greenmagics/Ender5plus_greenmaker_mod/zdj/1.jpg

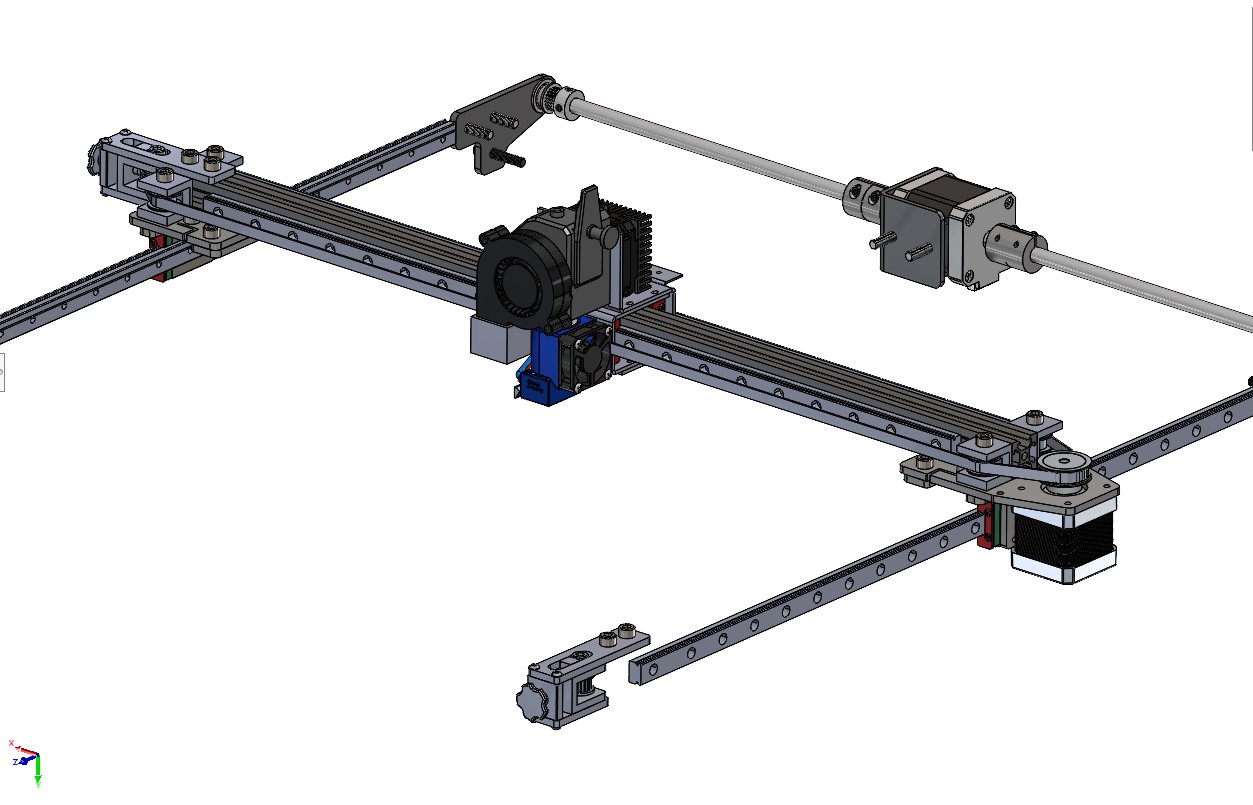
zdj/1.jpg
