greenmagics/Ender5plus_greenmaker_mod/zdj/2.jpg

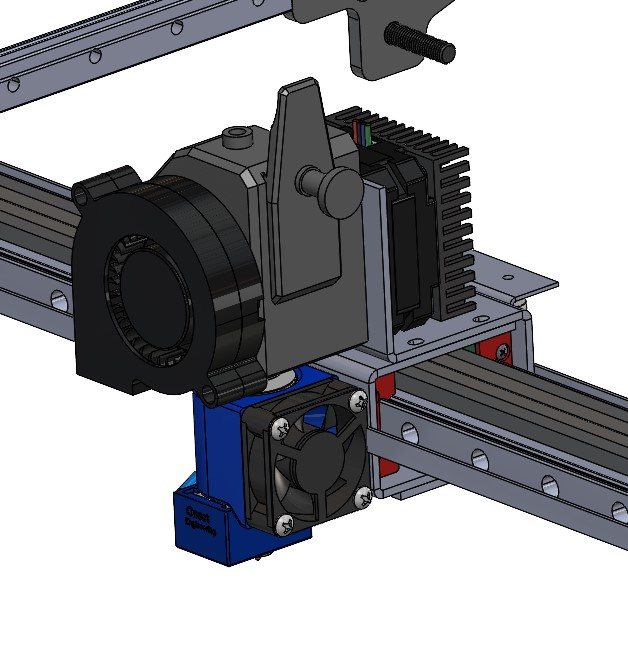
zdj/2.jpg
