greenmagics/Ender5plus_greenmaker_mod/zdj/3.jpg

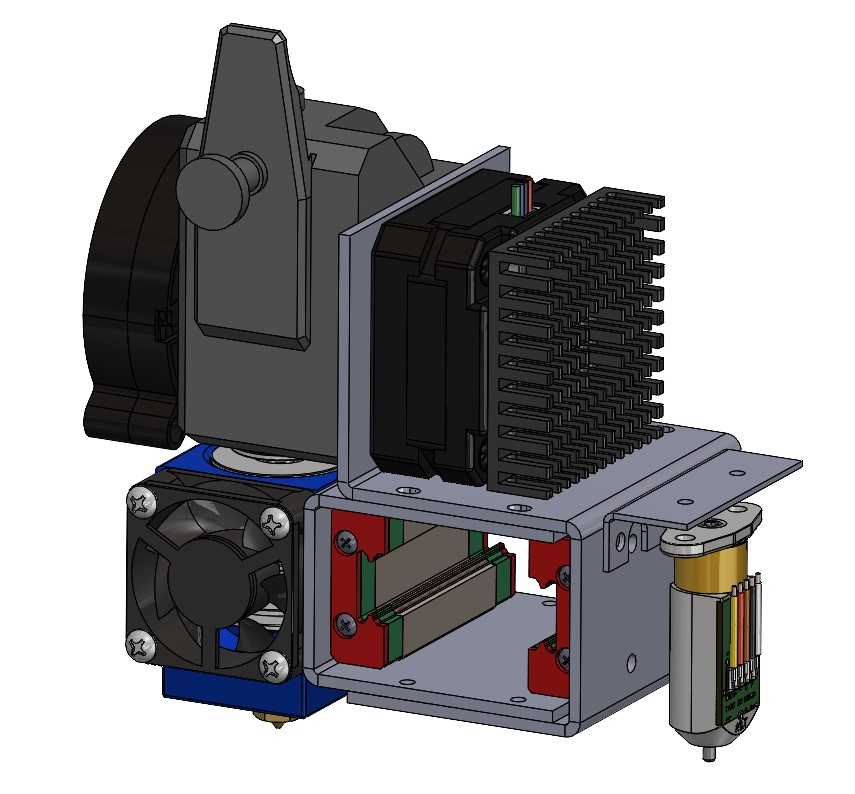
zdj/3.jpg
