greenmagics/Ender5plus_greenmaker_mod/zdj/4.jpg

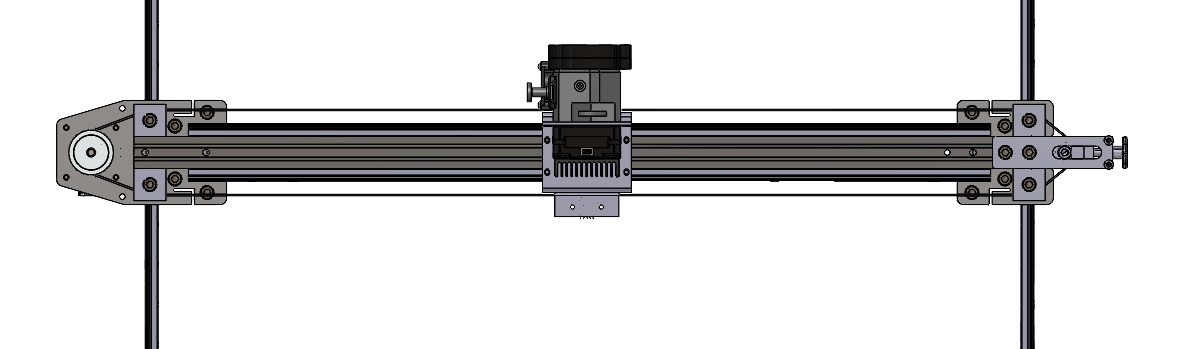
zdj/4.jpg
