greenmagics/Ender5plus_greenmaker_mod/zdj/5.jpg

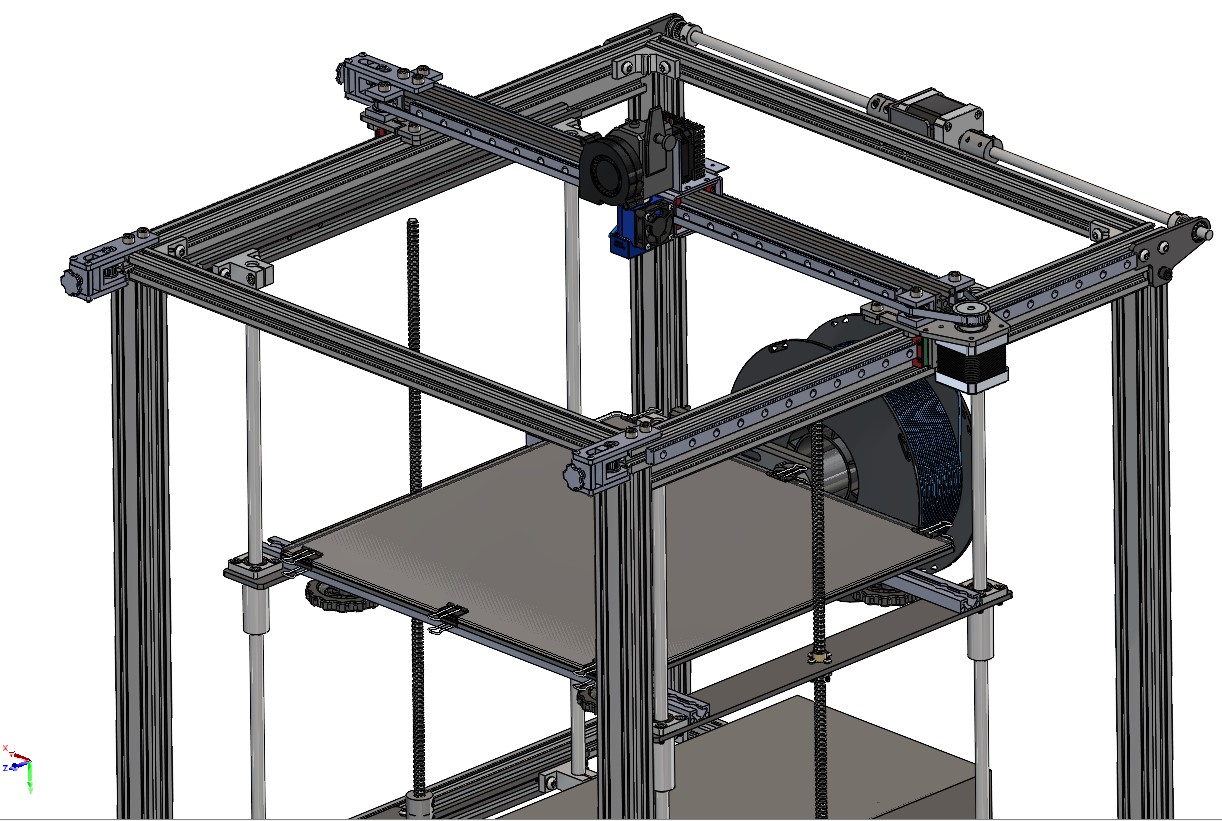
zdj/5.jpg
