greenmagics/Ender5plus_greenmaker_mod/parts/z-axis-drive-assem/z-axis-assem.SLDASM

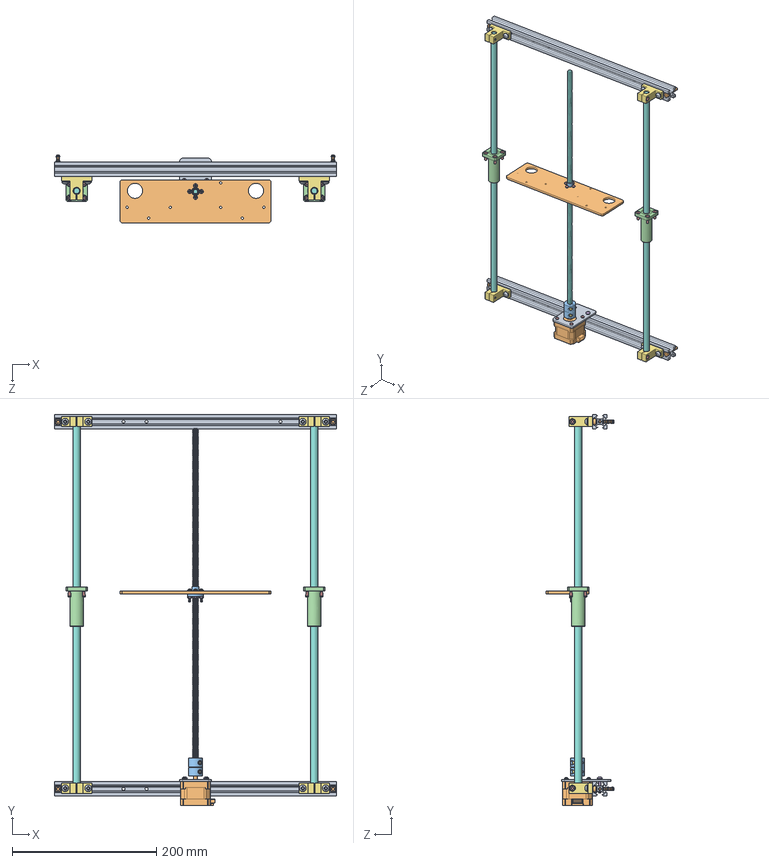
[picture p20: CAD file, 2021-08-18]
parts/z-axis-drive-assem/z-axis-assem.SLDASM
392.0 x 543.0 x 95.0 mm
z-axis-stepper-bracket
stepper-motor
shaft-coupling
lock-washer x 22
bhcs-M3 x 8
bhcs-M4 x 2
shcs-M3 x 2
lead-screw
z-axis-strut-20x20 x 2
z-axis-bearing-plate
lead-screw-nut
flanged-bearing-10mm x 2
shcs-M4 x 12
hex-nut-3mm x 4
guide-rod-bracket x 4
guide-rod x 2
bhcs-M5 x 8
shcs-M5 x 4
