greenmagics/Ender5plus_greenmaker_mod/heatbreak and part cooling fan/heatbreak fan mount assembly.SLDASM

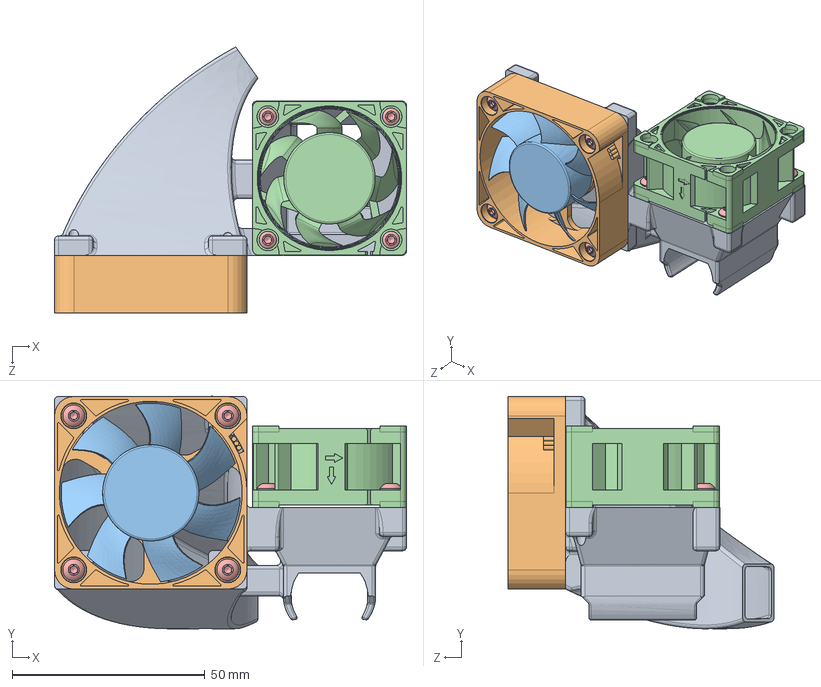
[picture p21: CAD file, 2021-08-12]
heatbreak and part cooling fan/heatbreak fan mount assembly.SLDASM
91.4 x 60.4 x 69.1 mm
heatbreak fan mount
Gelid Silent 5 frame
Gelid Silent 5 rotor
NF-A4X20 5V PWM.step
socket button head cap screw_am x 8
