greenmagics/Ender5plus_greenmaker_mod/parts/frame/frame assembly.SLDASM

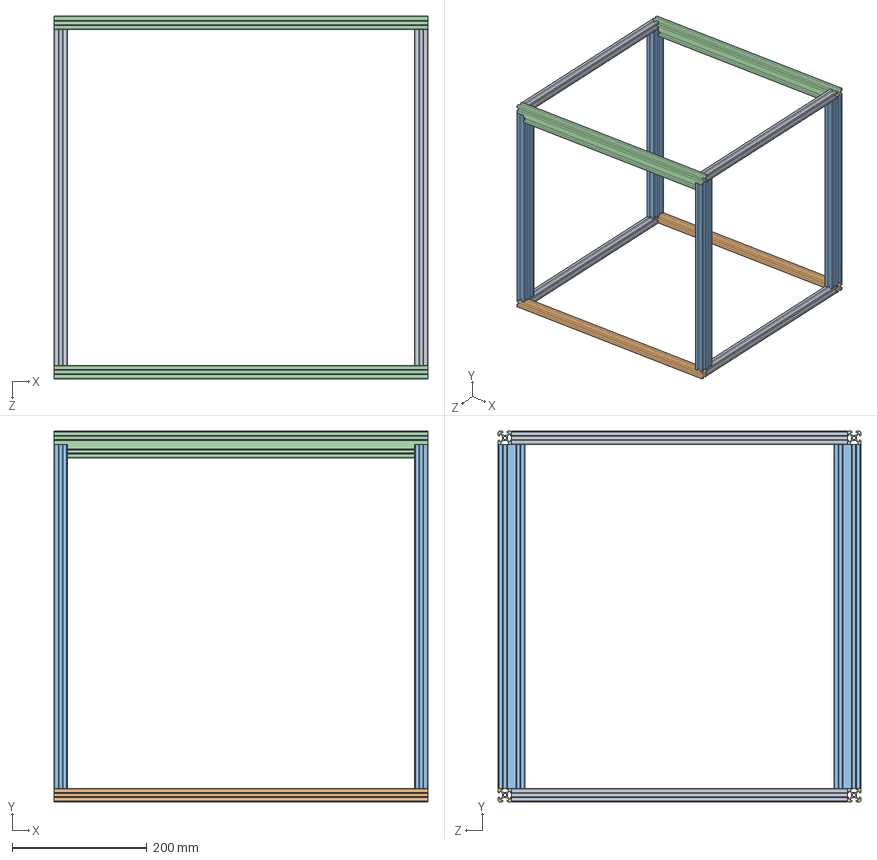
[picture p22: CAD file, 2021-08-12]
parts/frame/frame assembly.SLDASM
555.0 x 550.0 x 538.0 mm
base_498mm x 4
base_555mm x 2
vertical_510mm x 4
top_555 x 2
