greenmagics/Ender5plus_greenmaker_mod/parts/Y-AXIS-ASSEM/rear-pulley-assem.SLDASM

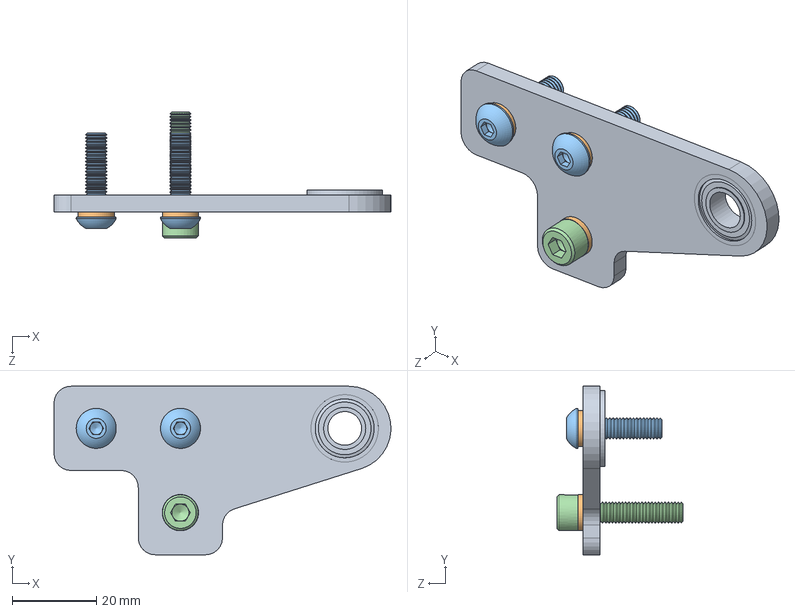
[picture p23: CAD file, 2021-08-12]
parts/Y-AXIS-ASSEM/rear-pulley-assem.SLDASM
80.0 x 40.0 x 30.0 mm
rear-pulley-bracket
lock-washer x 3
bhcs-M5 x 2
shcs-M5
