greenmagics/Ender5plus_greenmaker_mod/parts/z-axis-drive-assem/limit-switch-assem.sldasm

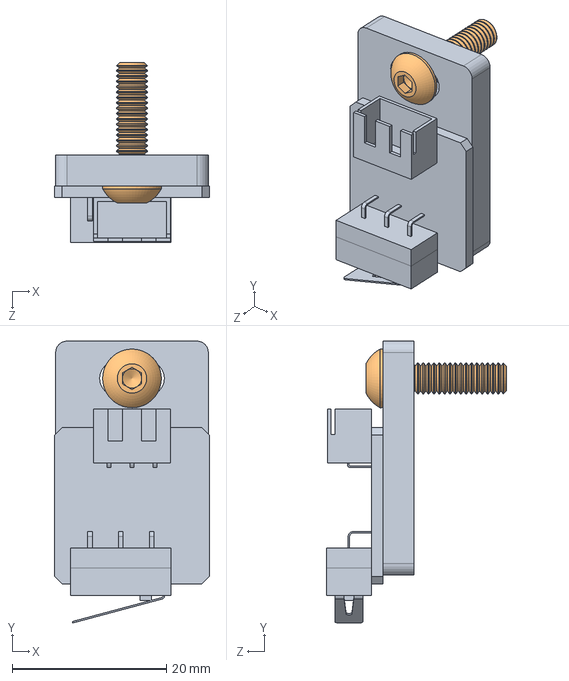
[picture p24: CAD file, 2021-08-12]
parts/z-axis-drive-assem/limit-switch-assem.sldasm
20.1 x 36.5 x 23.3 mm
limit-switch
bhcs-M4
