greenmagics/Ender5plus_greenmaker_mod/parts/hot-end/hot-end-assem.SLDASM

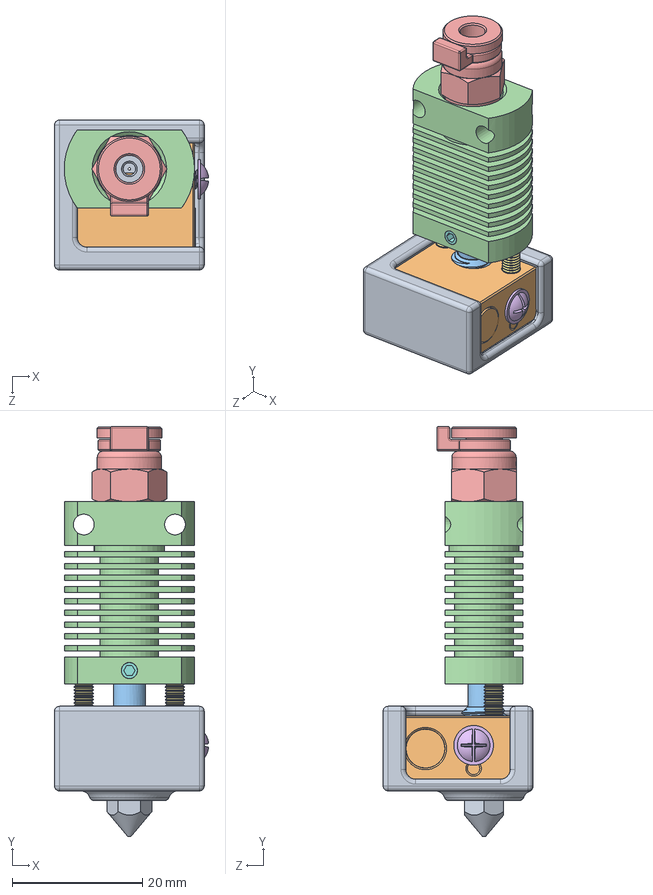
[picture p25: CAD file, 2021-08-12]
parts/hot-end/hot-end-assem.SLDASM
23.6 x 63.0 x 23.0 mm
nozzle-04
hot-end-heater-block
heat-break
heat-sink
hose-fitting-4x10mm
bh-screw-flanged-M3
fhsc-M3 x 2
set-screw-M3 x 2
hot-end-boot
