greenmagics/Ender5plus_greenmaker_mod/parts/x-axis-assem/x-axis-pulley-assem.SLDASM

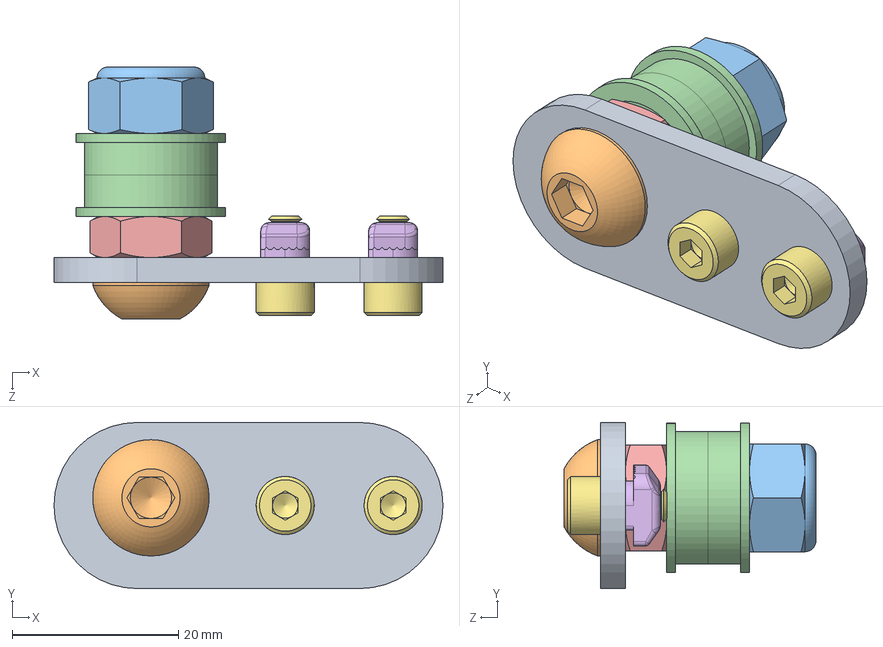
[picture p26: CAD file, 2021-08-12]
parts/x-axis-assem/x-axis-pulley-assem.SLDASM
46.8 x 20.0 x 30.4 mm
x-axis-pulley-mount
bhcs-M8
locknut-M8
pulley-half x 2
hex-nut-8mm
t-slot-nut x 2
shcs-M4 x 2
