greenmagics/Ender5plus_greenmaker_mod/czesci_dodane/GT2/GT2 Timing Pulley, Configurable.SLDASM

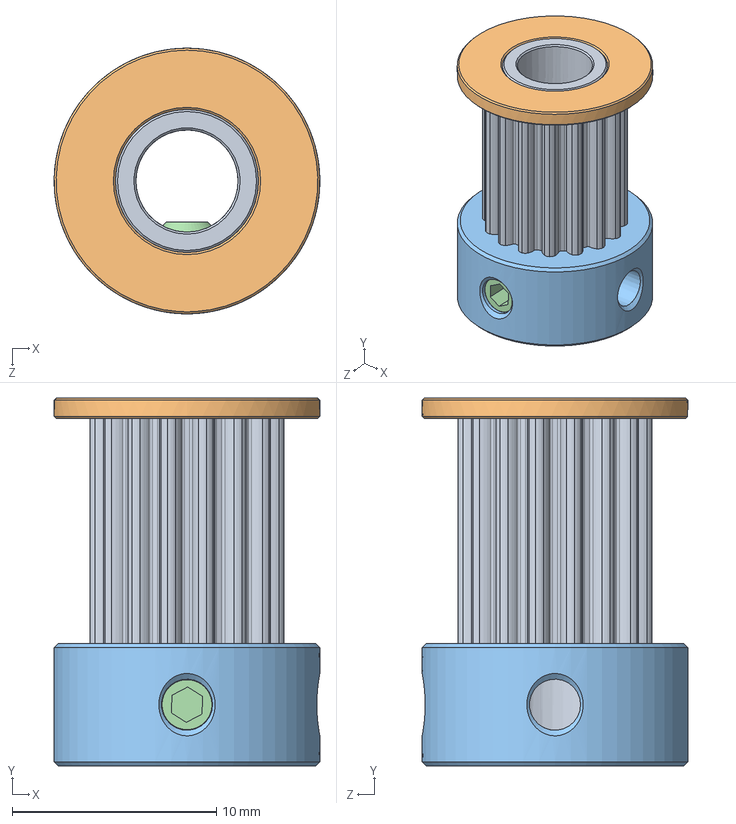
[picture p27: CAD file, 2021-08-12]
czesci_dodane/GT2/GT2 Timing Pulley, Configurable.SLDASM
13.0 x 18.0 x 13.0 mm
Body, GT2 Timing Pulley, Configurable
Top Flange, GT2 Timing Pulley, Configurable
Bottom Base, GT2 Timing Pulley, Configurable
socket set screw flat point_am
