greenmagics/Ender5plus_greenmaker_mod/parts/Y-AXIS-ASSEM/y-axis-drive-shaft-assem.sldasm

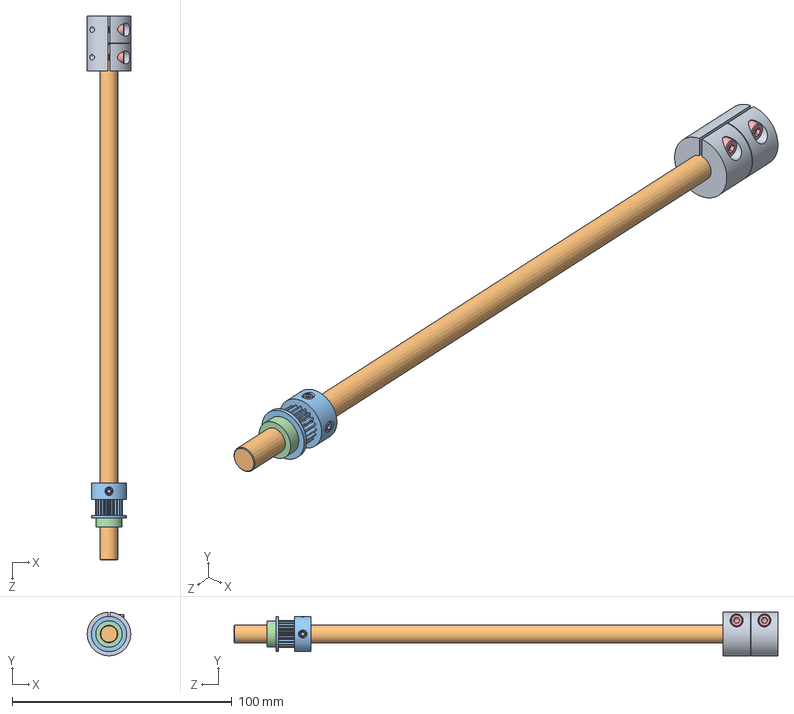
[picture p28: CAD file, 2021-08-12]
parts/Y-AXIS-ASSEM/y-axis-drive-shaft-assem.sldasm
19.8 x 19.8 x 247.6 mm
shaft-coupling
drive-shaft-8mm
toothed-pulley
delrin-spacer
shcs-M3 x 2
set-screw-M3 x 2
