greenmagics/Ender5plus_greenmaker_mod/czesci_dodane/GT2/Configurable GT2 Timing Pulleys Lined Up.SLDASM

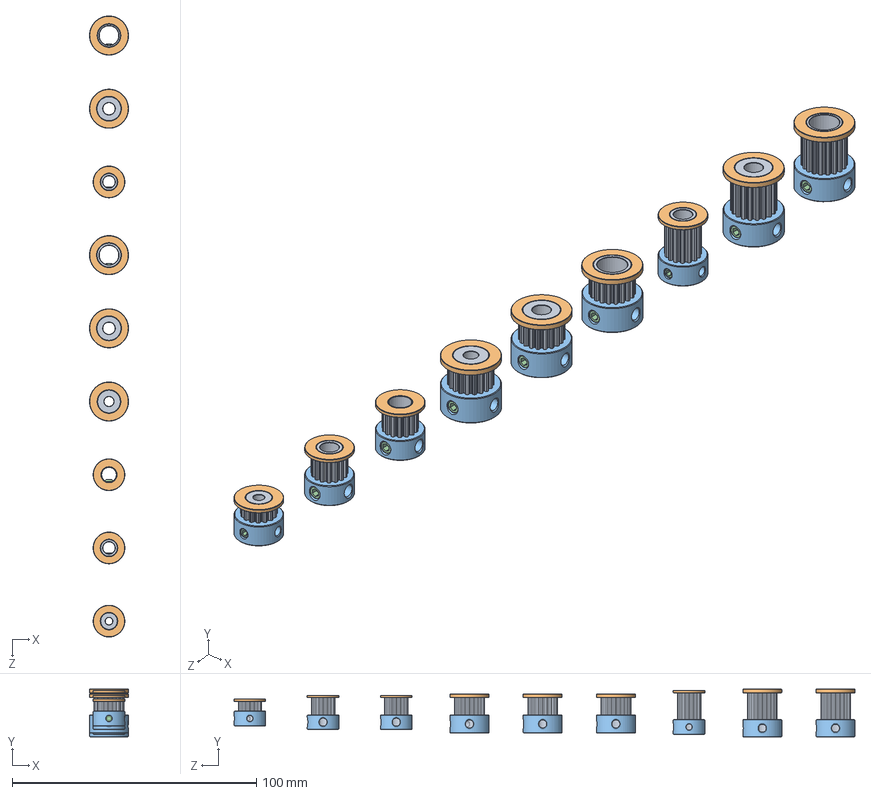
[picture p29: CAD file, 2021-08-12]
czesci_dodane/GT2/Configurable GT2 Timing Pulleys Lined Up.SLDASM
16.0 x 19.5 x 254.5 mm
Body, GT2 Timing Pulley, Configurable x 9
Top Flange, GT2 Timing Pulley, Configurable x 9
Bottom Base, GT2 Timing Pulley, Configurable x 9
socket set screw flat point_am x 9
