greenmagics/Ender5plus_greenmaker_mod/parts/x-axis-assem/x-axis-bogey-left.SLDASM

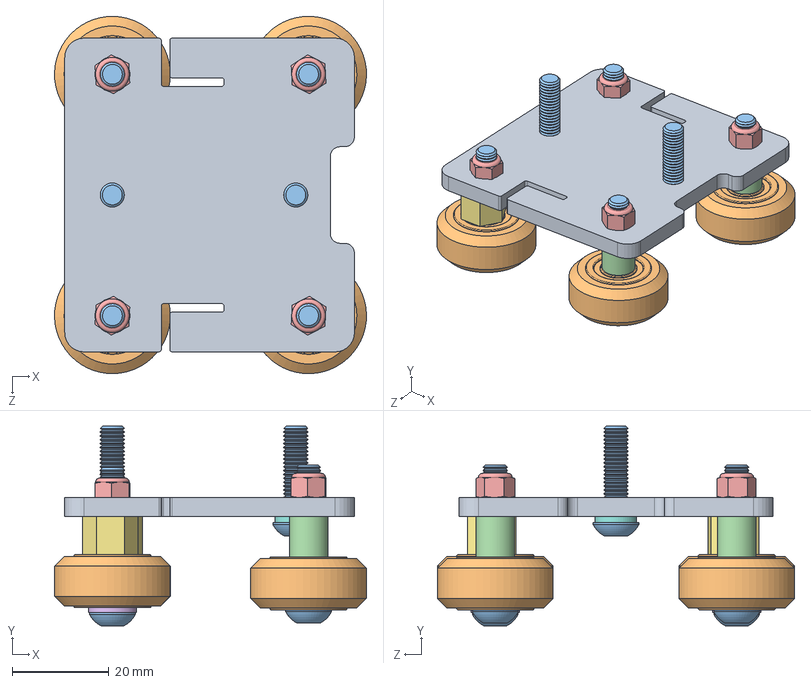
[picture p30: CAD file, 2021-08-12]
parts/x-axis-assem/x-axis-bogey-left.SLDASM
64.6 x 41.3 x 74.0 mm
x-axis-stepper-mount
wheel x 4
bhcs-M5 x 6
wheel-spacer x 2
locknut-M4 x 4
flat-washer x 2
eccentric-nut x 2
lock-washer x 2
