greenmagics/Ender5plus_greenmaker_mod/parts/Y-AXIS-ASSEM/y-axis-drive-assem.SLDASM

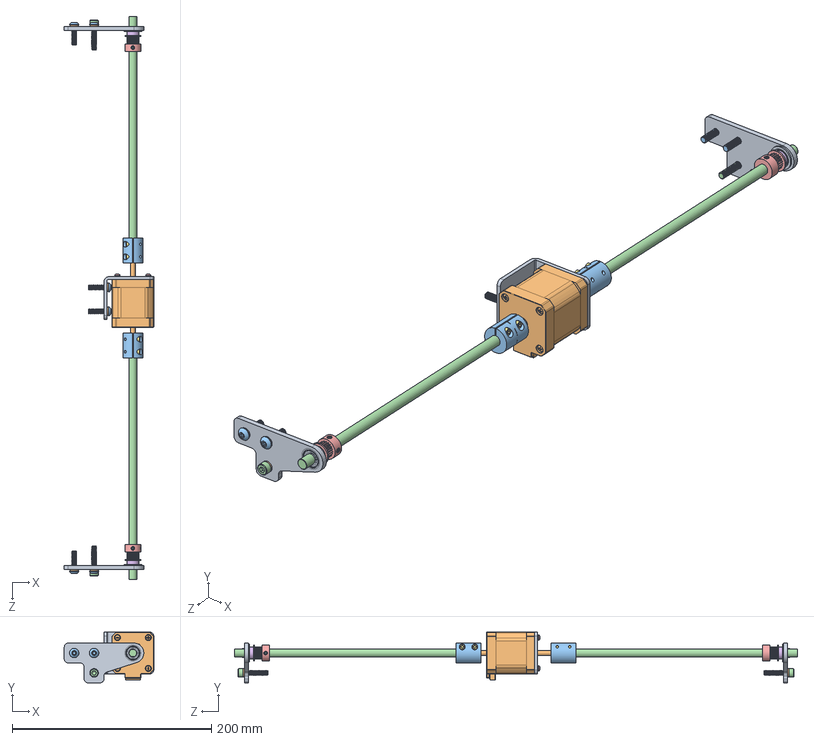
[picture p31: CAD file, 2021-08-12]
parts/Y-AXIS-ASSEM/y-axis-drive-assem.SLDASM
90.0 x 51.0 x 565.7 mm
y-axis-stepper-bracket
stepper-motor
shaft-coupling x 2
drive-shaft-8mm x 2
toothed-pulley x 2
delrin-spacer x 2
shcs-M3 x 4
set-screw-M3 x 4
rear-pulley-bracket x 2
lock-washer x 12
bhcs-M5 x 6
shcs-M5 x 2
bhcs-M3 x 4
