greenmagics/Ender5plus_greenmaker_mod/parts/x-axis-assem/x-axis-bogey-right.SLDASM

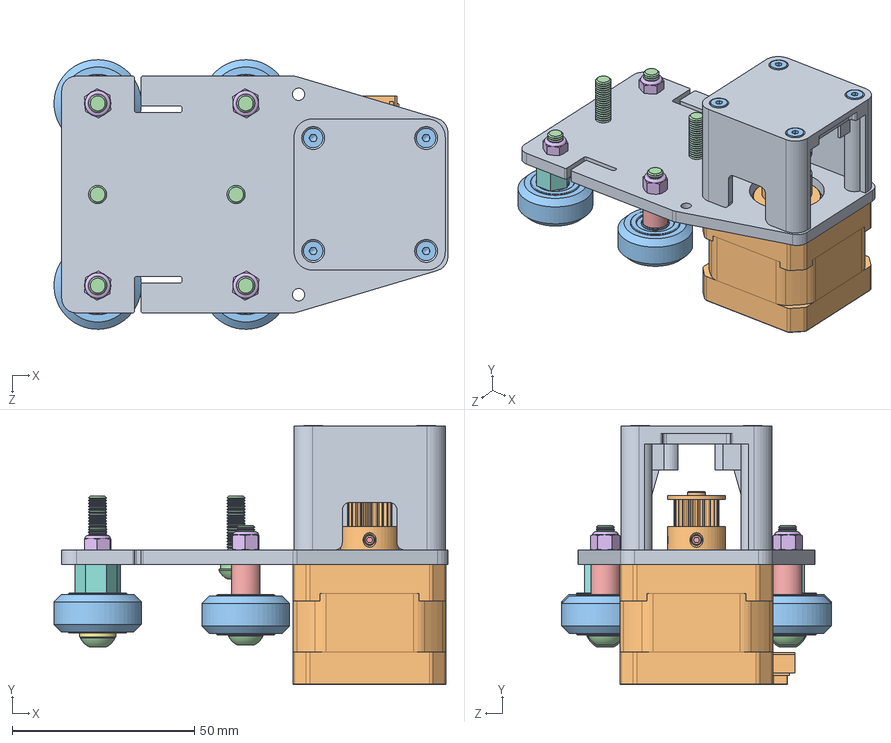
[picture p32: CAD file, 2021-08-12]
parts/x-axis-assem/x-axis-bogey-right.SLDASM
108.1 x 71.2 x 74.0 mm
x-axis-stepper-mount
toothed-pulley
wheel x 4
bhcs-M5 x 6
wheel-spacer x 2
locknut-M4 x 4
flat-washer x 2
eccentric-nut x 2
x-axis-stepper-cover
stepper-motor
fhsc-M3 x 4
lock-washer x 2
set-screw-M3 x 2
