greenmagics/Ender5plus_greenmaker_mod/parts/z-axis-drive-assem/guide-rod-assem.SLDASM

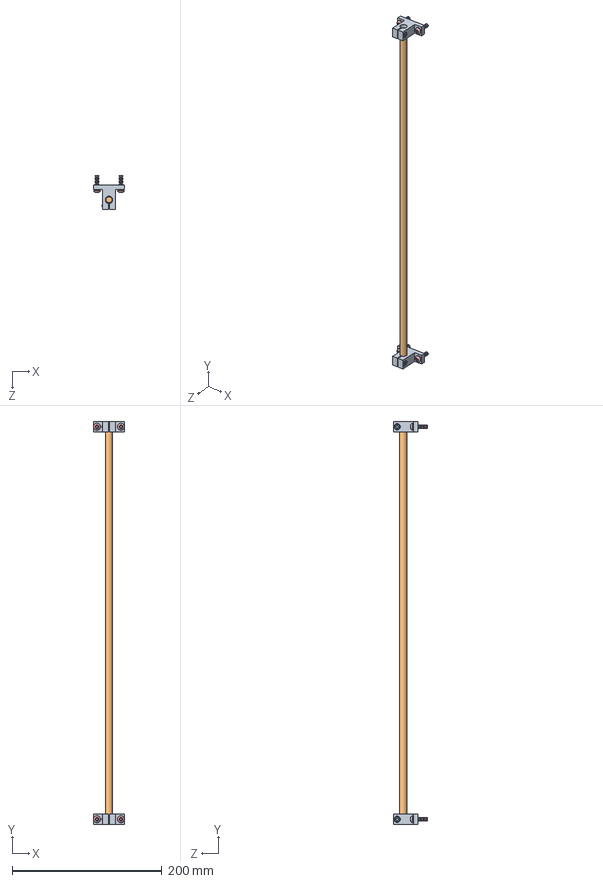
[picture p33: CAD file, 2021-08-12]
parts/z-axis-drive-assem/guide-rod-assem.SLDASM
42.0 x 538.0 x 45.5 mm
guide-rod-bracket x 2
guide-rod
shcs-M4 x 2
lock-washer x 4
bhcs-M5 x 4
