greenmagics/Ender5plus_greenmaker_mod/parts/extruder/bltouch assembly.SLDASM

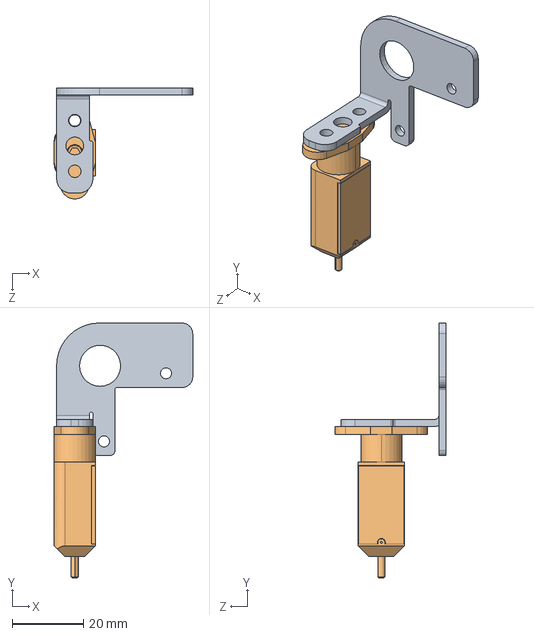
[picture p34: CAD file, 2021-08-12]
parts/extruder/bltouch assembly.SLDASM
38.9 x 71.5 x 31.1 mm
bltouch bracket
BLTouch.step
