greenmagics/Ender5plus_greenmaker_mod/parts/z-axis-drive-assem/z-axis-stepper-assem.sldasm

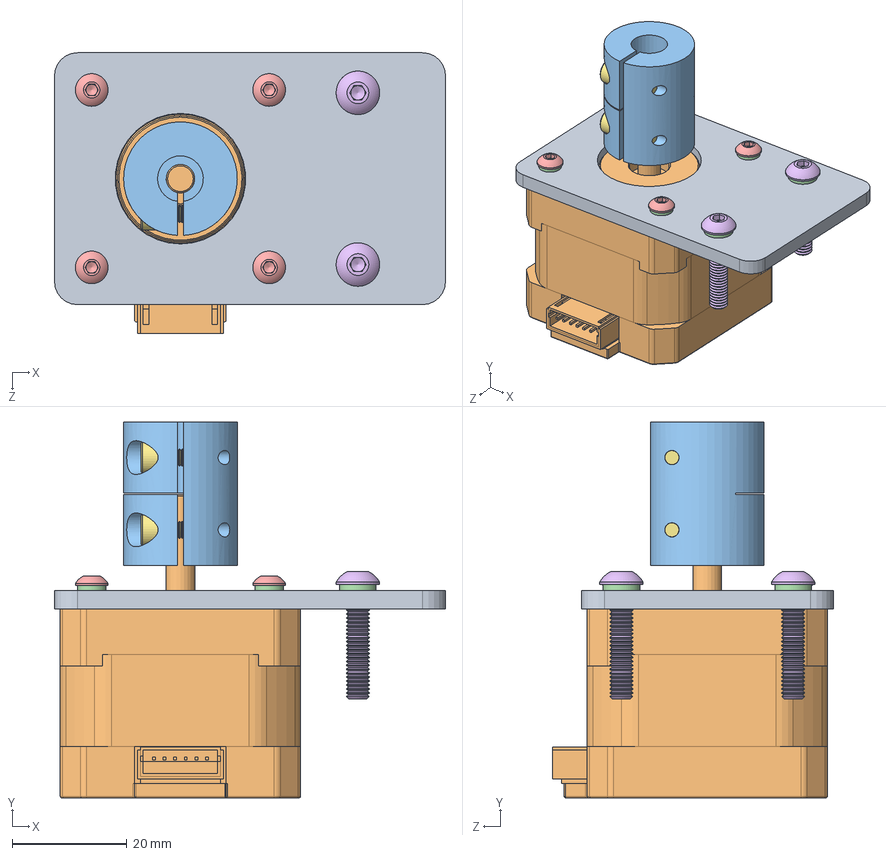
[picture p35: CAD file, 2021-08-12]
parts/z-axis-drive-assem/z-axis-stepper-assem.sldasm
68.3 x 65.6 x 49.0 mm
z-axis-stepper-bracket
stepper-motor
shaft-coupling
lock-washer x 6
bhcs-M3 x 4
bhcs-M4 x 2
shcs-M3 x 2
