greenmagics/Ender5plus_greenmaker_mod/czesci_dodane/direct/hotend_v6/grzalka.stp

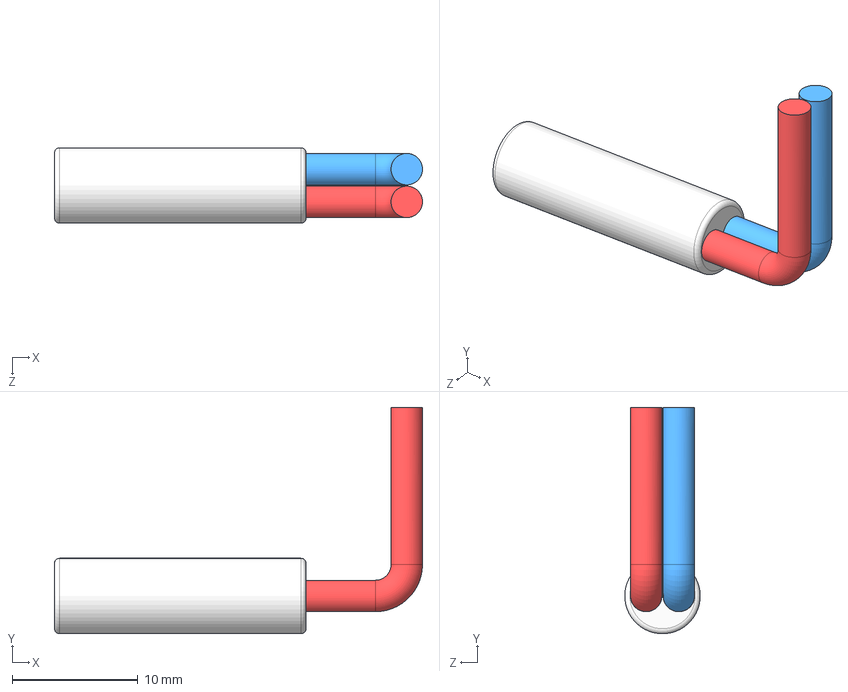
[picture p36: CAD file, 2021-08-12]
czesci_dodane/direct/hotend_v6/grzalka.stp
29.2 x 18.0 x 6.00 mm
