greenmagics/Ender5plus_greenmaker_mod/czesci_dodane/direct/karetka/cz2.SLDPRT

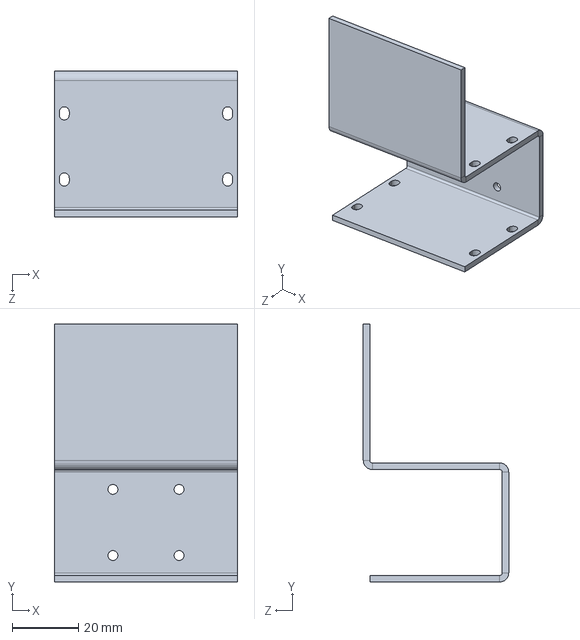
[picture p37: CAD file, 2021-08-12]
czesci_dodane/direct/karetka/cz2.SLDPRT
55.4 x 78.0 x 44.0 mm
