greenmagics/Ender5plus_greenmaker_mod/czesci_dodane/GT2/Belt Tensioner Type B.STEP

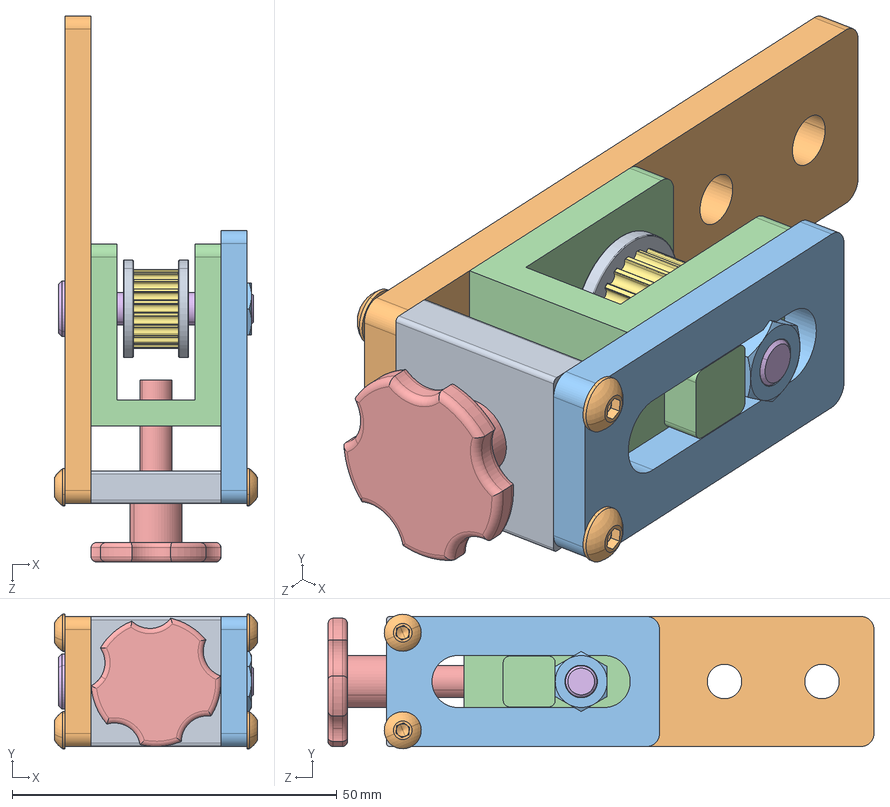
[picture p38: CAD file, 2021-08-12]
czesci_dodane/GT2/Belt Tensioner Type B.STEP
31.3 x 20.7 x 84.0 mm
Plate1
Plate2
Knob
socket head cap screw_am_B18.3.1M - 5 x 0.8 x 25 Hex SHCS -- 25NHX
Gates_2GT_20T_Toothed_Vychoz｡
socket button head cap screw_am_B18.3.4M - 3 x 0.5 x 8 SBHCS --N x 4
hex nut style 1_am_B18.2.4.1M - Hex nut, Style 1, M5 x 0.8 --D-N
