greenmagics/Ender5plus_greenmaker_mod/czesci_dodane/mgn12/szyna450mm.SLDPRT

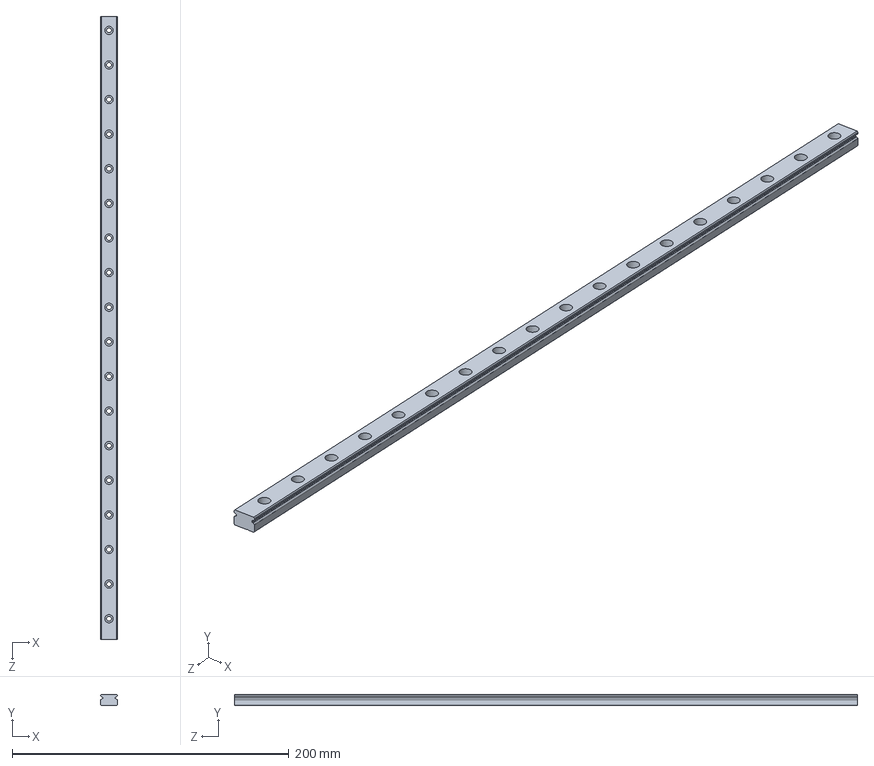
[picture p39: CAD file, 2021-08-18]
czesci_dodane/mgn12/szyna450mm.SLDPRT
12.0 x 8.00 x 450.0 mm
