greenmagics/Ender5plus_greenmaker_mod/czesci_dodane/mocowania_prowadnic/podstawa_prawa.stp

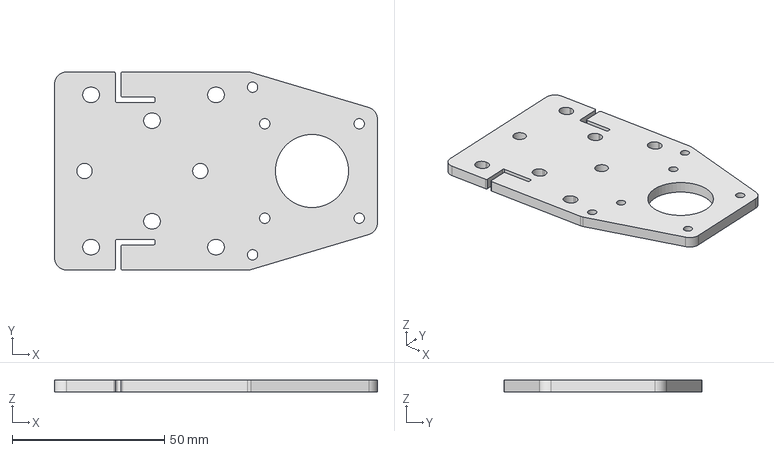
[picture p40: CAD file, 2021-08-12]
czesci_dodane/mocowania_prowadnic/podstawa_prawa.stp
106.0 x 65.0 x 4.00 mm
