greenmagics/Ender5plus_greenmaker_mod/czesci_dodane/nadmuch/dysza.SLDPRT

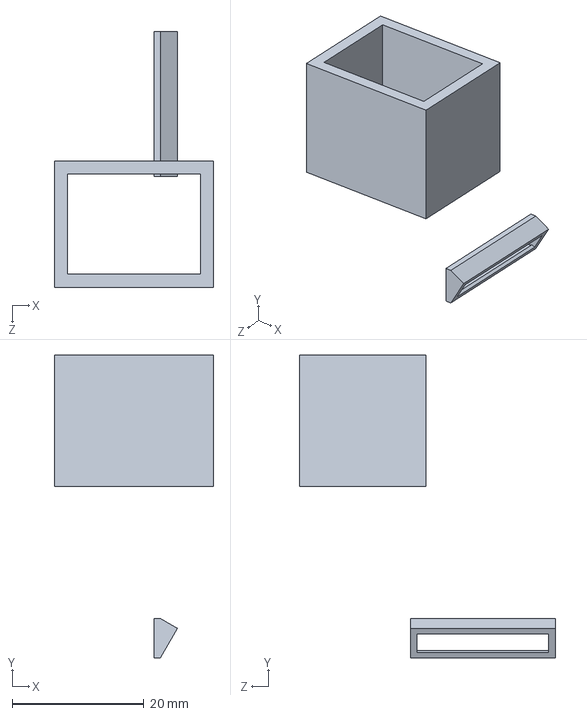
[picture p41: CAD file, 2021-08-12]
czesci_dodane/nadmuch/dysza.SLDPRT
24.2 x 46.0 x 38.8 mm
