greenmagics/Ender5plus_greenmaker_mod/heatbreak and part cooling fan/Gelid Silent 5 rotor.SLDPRT

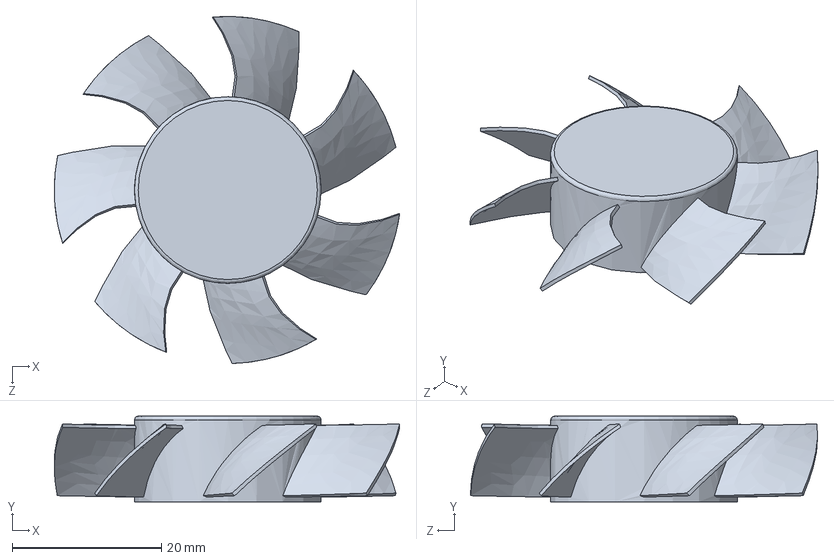
[picture p42: CAD file, 2021-08-12]
heatbreak and part cooling fan/Gelid Silent 5 rotor.SLDPRT
46.3 x 11.5 x 46.5 mm
