greenmagics/Ender5plus_greenmaker_mod/parts/build-plate-assem/leveling-wheel.SLDPRT

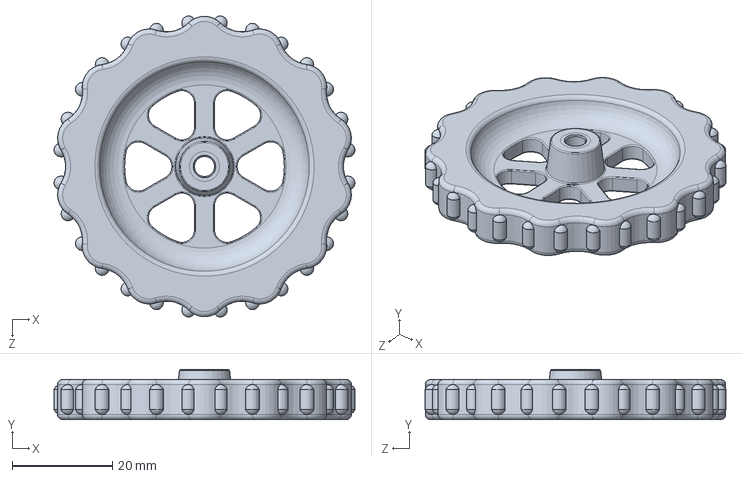
[picture p43: CAD file, 2021-08-12]
parts/build-plate-assem/leveling-wheel.SLDPRT
60.1 x 10.0 x 60.1 mm
