greenmagics/Ender5plus_greenmaker_mod/parts/endcap.SLDPRT

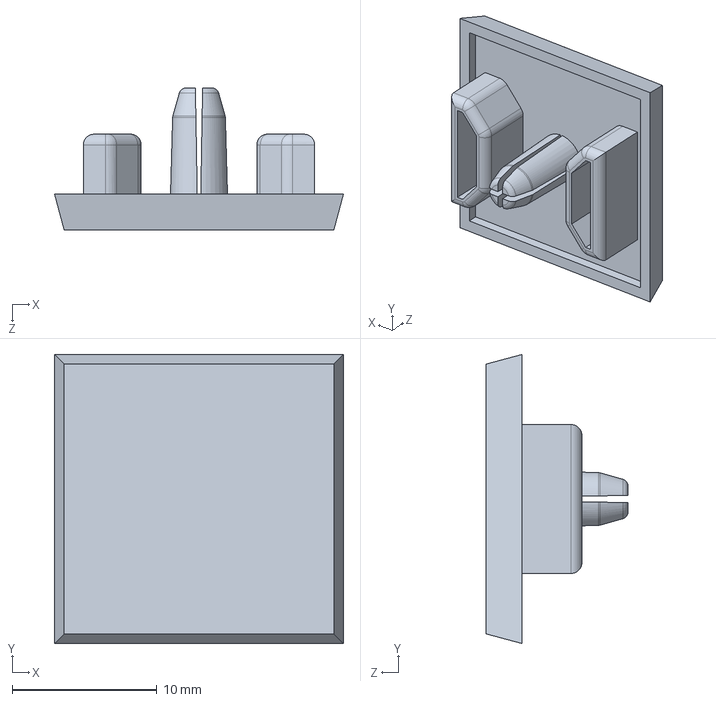
[picture p44: CAD file, 2021-08-12]
parts/endcap.SLDPRT
20.0 x 20.0 x 9.85 mm
