greenmagics/Ender5plus_greenmaker_mod/parts/extruder/extruder-pivot-bushing.SLDPRT

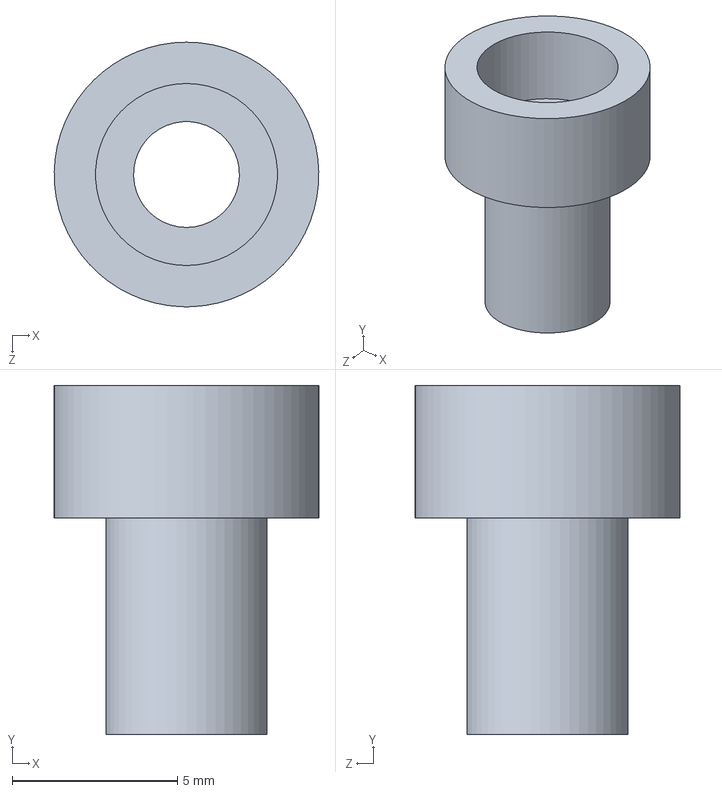
[picture p45: CAD file, 2021-08-12]
parts/extruder/extruder-pivot-bushing.SLDPRT
8.00 x 10.6 x 8.00 mm
