greenmagics/Ender5plus_greenmaker_mod/parts/frame/base_498mm.SLDPRT

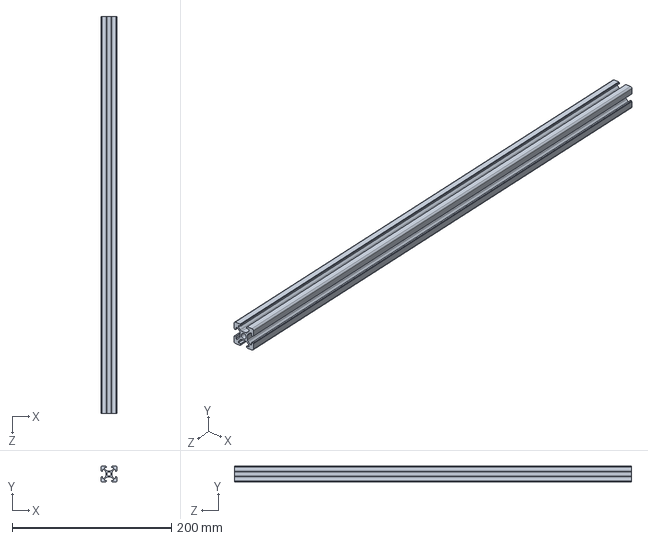
[picture p46: CAD file, 2021-08-12]
parts/frame/base_498mm.SLDPRT
20.0 x 20.0 x 498.0 mm
