greenmagics/Ender5plus_greenmaker_mod/parts/x-axis-assem/x-axis-stepper-cover.SLDPRT

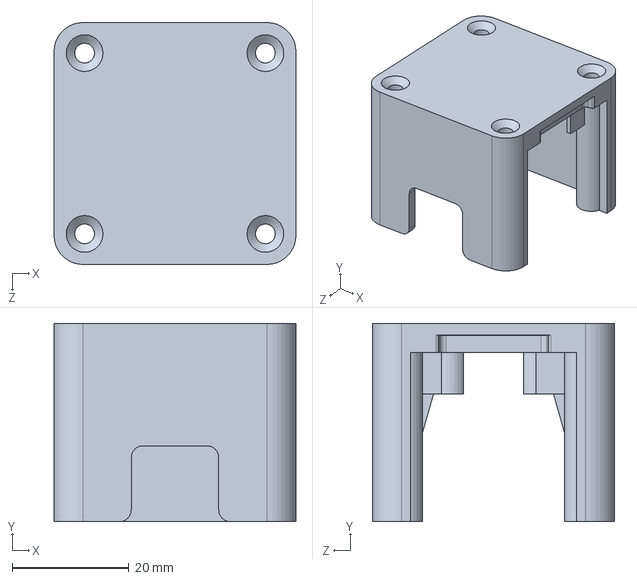
[picture p47: CAD file, 2021-08-12]
parts/x-axis-assem/x-axis-stepper-cover.SLDPRT
41.5 x 34.0 x 41.5 mm
