greenmagics/Ender5plus_greenmaker_mod/parts/Y-AXIS-ASSEM/delrin-spacer.SLDPRT

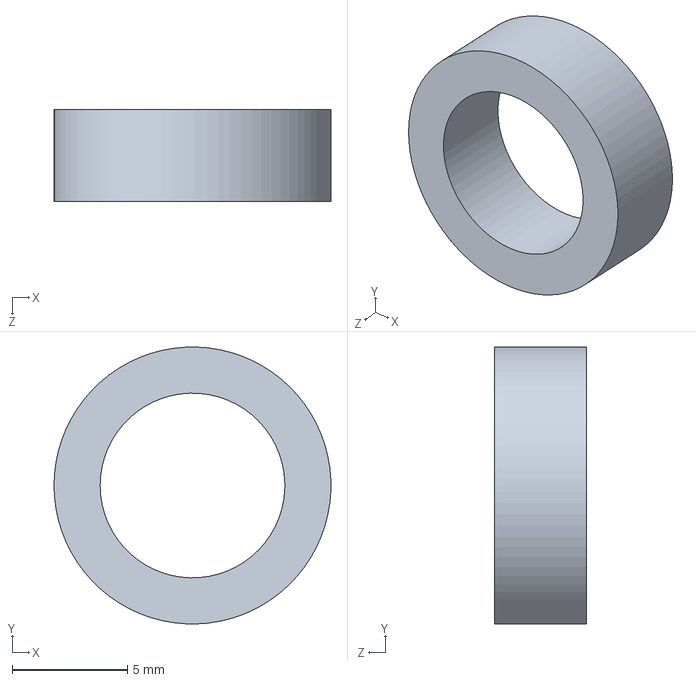
[picture p48: CAD file, 2021-08-12]
parts/Y-AXIS-ASSEM/delrin-spacer.SLDPRT
12.0 x 12.0 x 4.00 mm
