greenmagics/Ender5plus_greenmaker_mod/czesci_dodane/direct/hotend_v6/sock.step

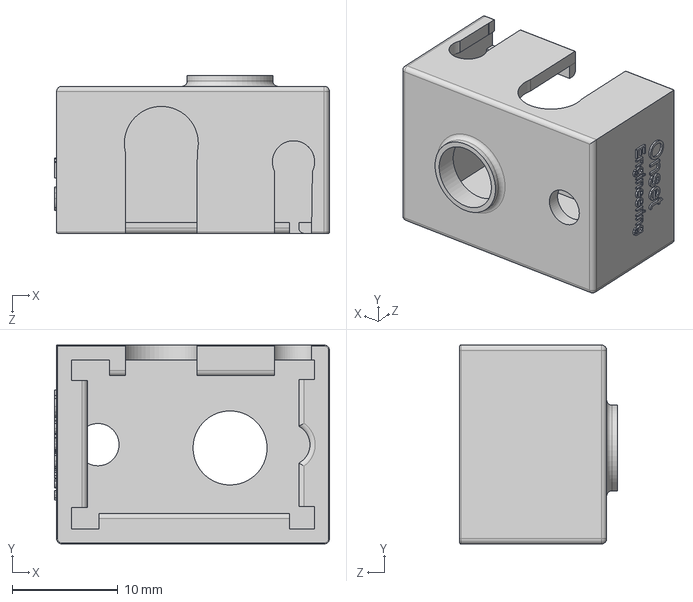
[picture p49: CAD file, 2021-08-12]
czesci_dodane/direct/hotend_v6/sock.step
26.0 x 18.8 x 14.9 mm
