greenmagics/Ender5plus_greenmaker_mod/czesci_dodane/direct/karetka/mocowanie_bltouch.SLDPRT

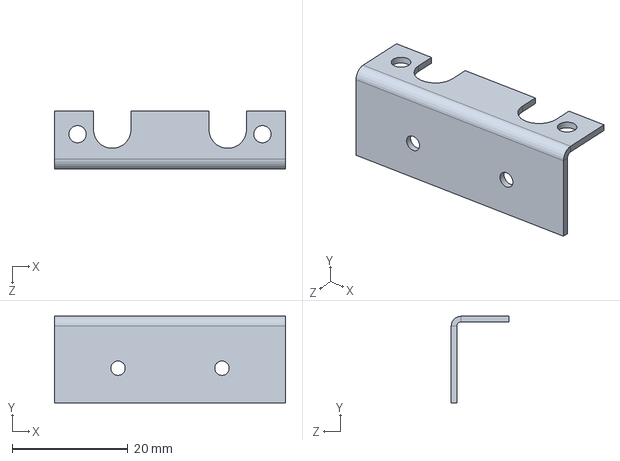
[picture p50: CAD file, 2021-08-12]
czesci_dodane/direct/karetka/mocowanie_bltouch.SLDPRT
40.0 x 15.0 x 10.0 mm
