greenmagics/Ender5plus_greenmaker_mod/czesci_dodane/GT2/GT2_20T-sh8.SLDPRT

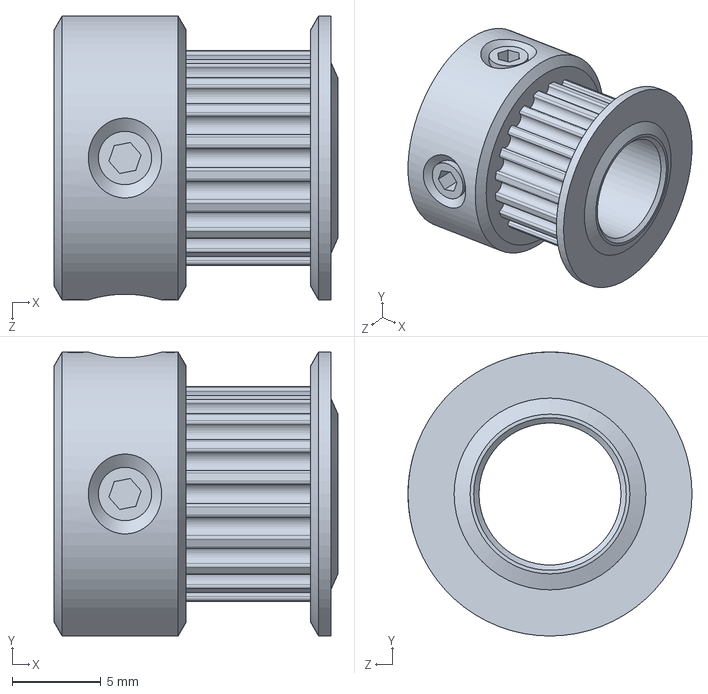
[picture p51: CAD file, 2021-08-12]
czesci_dodane/GT2/GT2_20T-sh8.SLDPRT
16.0 x 16.0 x 16.0 mm
