greenmagics/Ender5plus_greenmaker_mod/czesci_dodane/mgn12/MGN12 LINEAR GUIDE RAIL, CONFIGURABLE, 500 mm.STEP

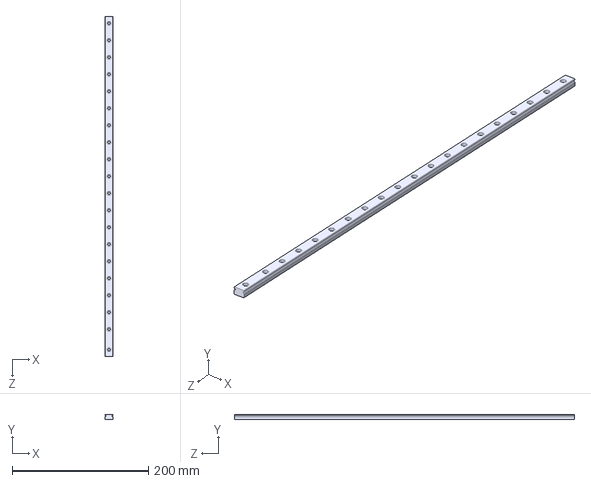
[picture p52: CAD file, 2021-08-12]
czesci_dodane/mgn12/MGN12 LINEAR GUIDE RAIL, CONFIGURABLE, 500 mm.STEP
12.0 x 8.00 x 500.0 mm
