greenmagics/Ender5plus_greenmaker_mod/czesci_dodane/mocowania_prowadnic/podstawa_lewa.stp

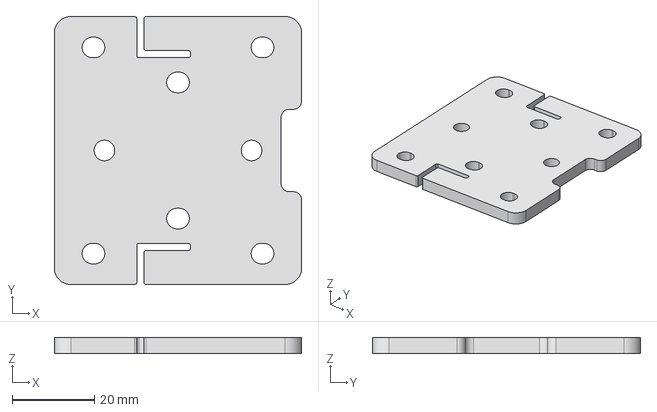
[picture p53: CAD file, 2021-08-12]
czesci_dodane/mocowania_prowadnic/podstawa_lewa.stp
60.0 x 65.0 x 4.00 mm
