greenmagics/Ender5plus_greenmaker_mod/czesci_dodane/nema17/Rotor.SLDPRT

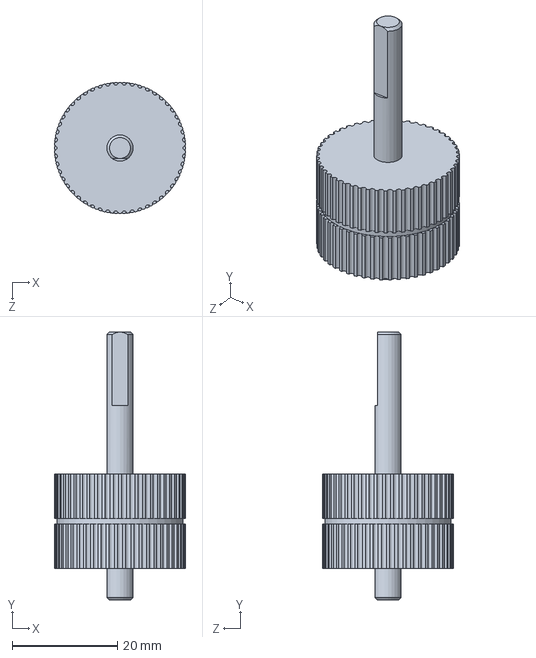
[picture p54: CAD file, 2021-08-12]
czesci_dodane/nema17/Rotor.SLDPRT
25.0 x 51.0 x 25.0 mm
