greenmagics/Ender5plus_greenmaker_mod/parts/build-plate-assem/hotbed crossmember short.SLDPRT

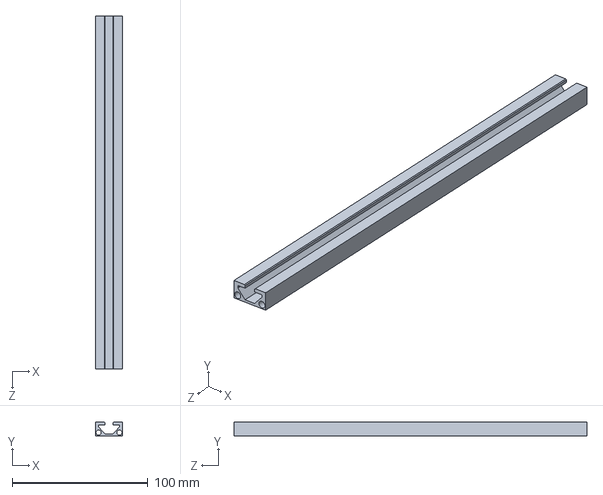
[picture p55: CAD file, 2021-08-12]
parts/build-plate-assem/hotbed crossmember short.SLDPRT
20.0 x 10.0 x 260.0 mm
