greenmagics/Ender5plus_greenmaker_mod/parts/electronics/iec320_703W-00_04.SLDPRT

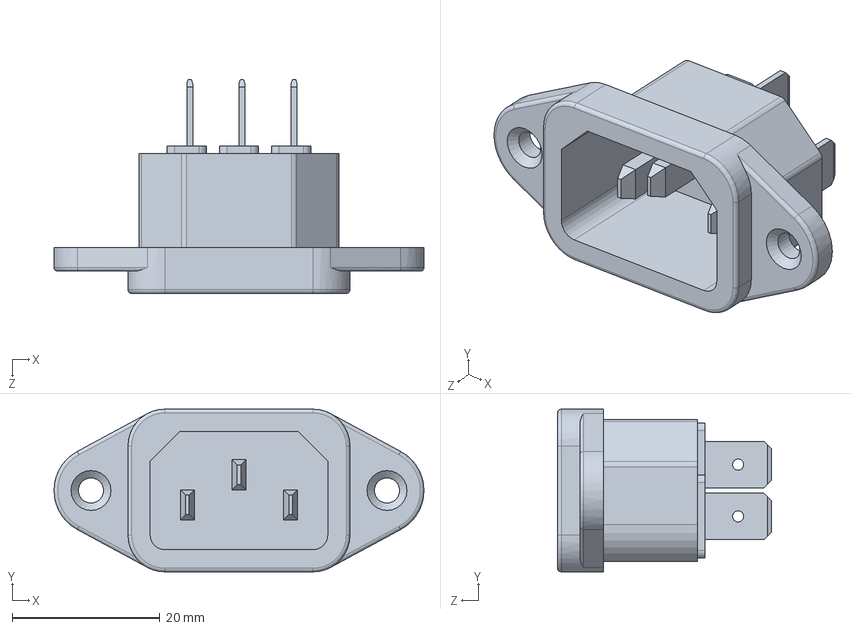
[picture p56: CAD file, 2021-08-12]
parts/electronics/iec320_703W-00_04.SLDPRT
50.0 x 22.0 x 28.9 mm
