greenmagics/Ender5plus_greenmaker_mod/parts/extruder/bltouch bracket.SLDPRT

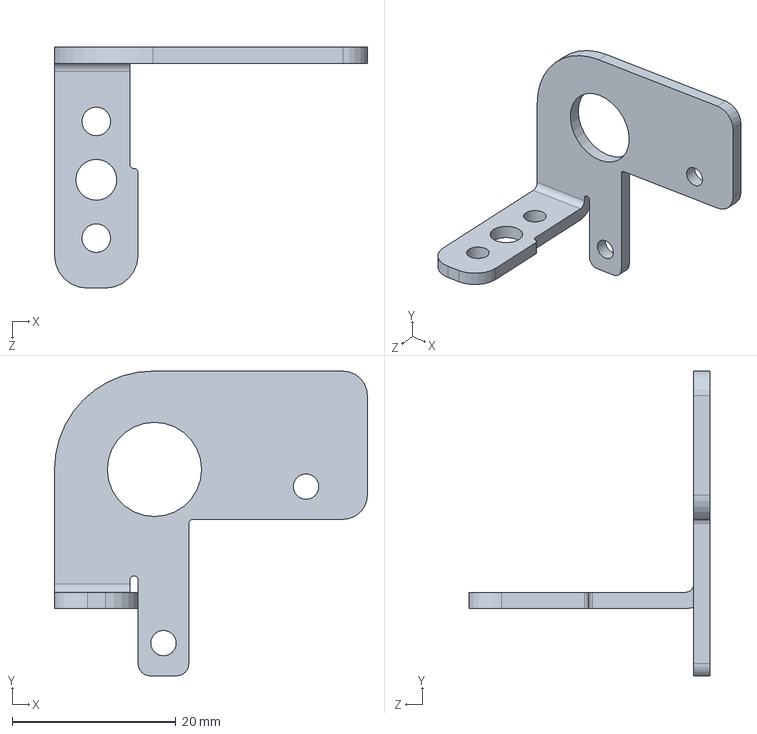
[picture p57: CAD file, 2021-08-12]
parts/extruder/bltouch bracket.SLDPRT
38.2 x 37.2 x 29.4 mm
