greenmagics/Ender5plus_greenmaker_mod/parts/frame/top_555.SLDPRT

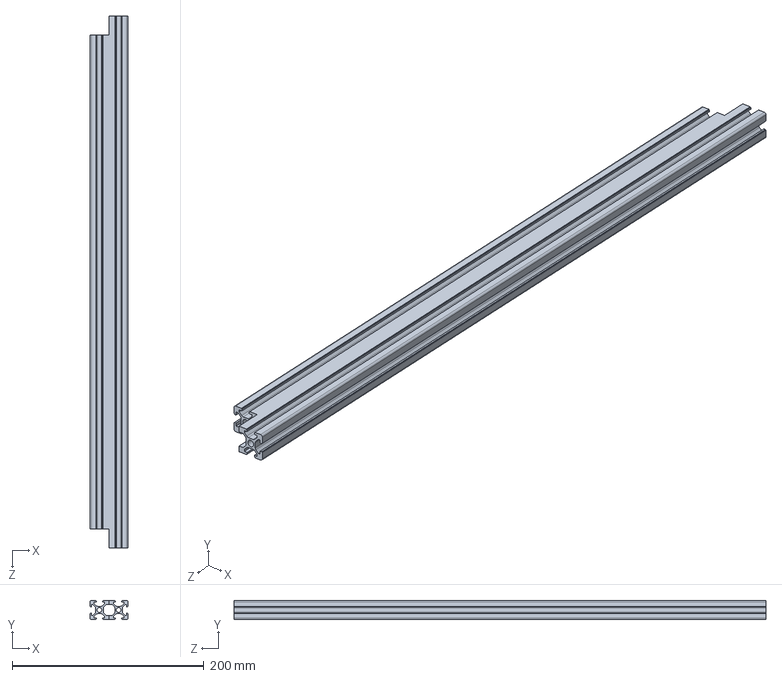
[picture p58: CAD file, 2021-08-12]
parts/frame/top_555.SLDPRT
40.0 x 20.0 x 555.0 mm
