greenmagics/Ender5plus_greenmaker_mod/parts/hot-end/hot-end-fan.SLDPRT

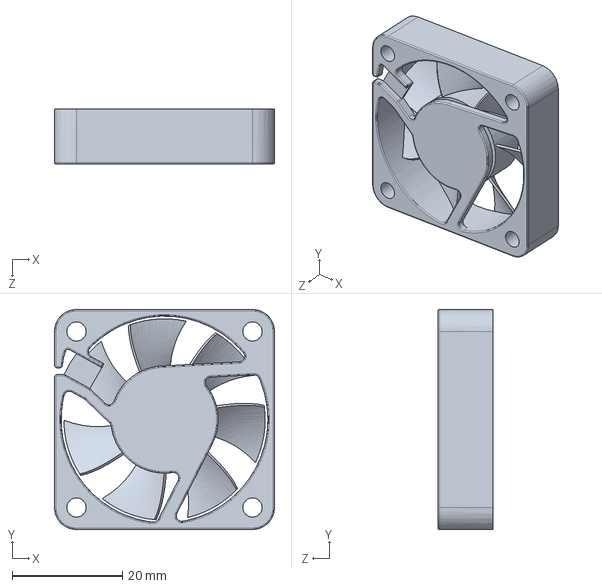
[picture p59: CAD file, 2021-08-12]
parts/hot-end/hot-end-fan.SLDPRT
40.0 x 40.0 x 10.0 mm
