greenmagics/Ender5plus_greenmaker_mod/parts/spool-holder/spool-spindle-ring.SLDPRT

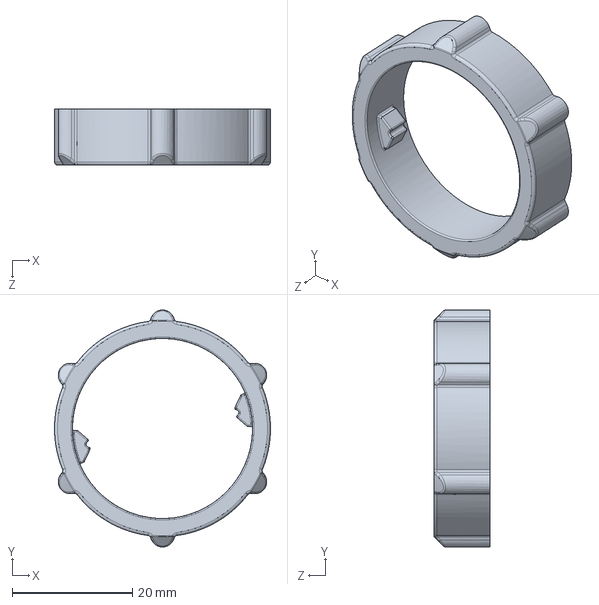
[picture p60: CAD file, 2021-08-12]
parts/spool-holder/spool-spindle-ring.SLDPRT
36.0 x 39.5 x 9.40 mm
