greenmagics/Ender5plus_greenmaker_mod/parts/x-axis-assem/wheel-assem/wheel.SLDPRT

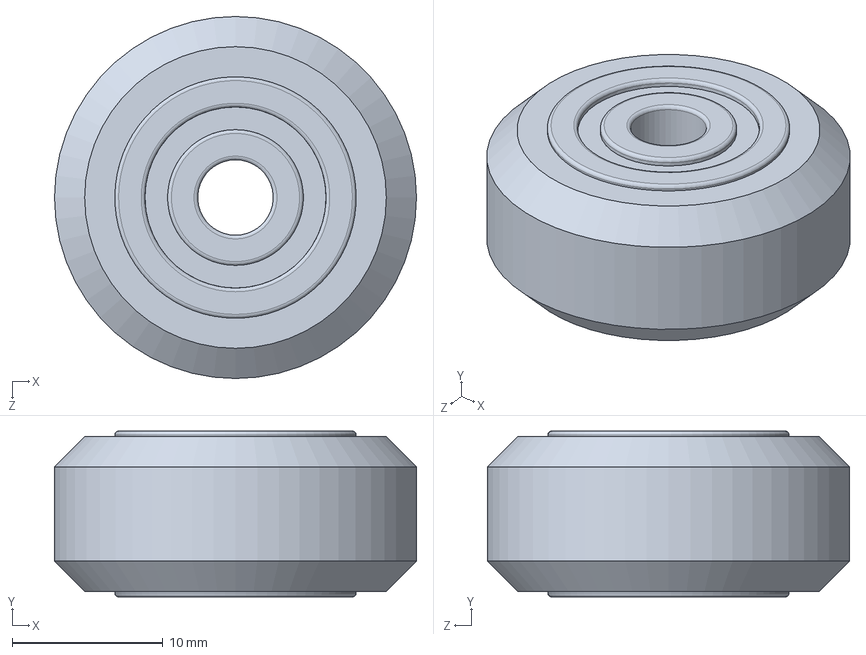
[picture p61: CAD file, 2021-08-12]
parts/x-axis-assem/wheel-assem/wheel.SLDPRT
24.0 x 11.0 x 24.0 mm
