greenmagics/Ender5plus_greenmaker_mod/parts/Y-AXIS-ASSEM/rear-pulley-bracket.SLDPRT

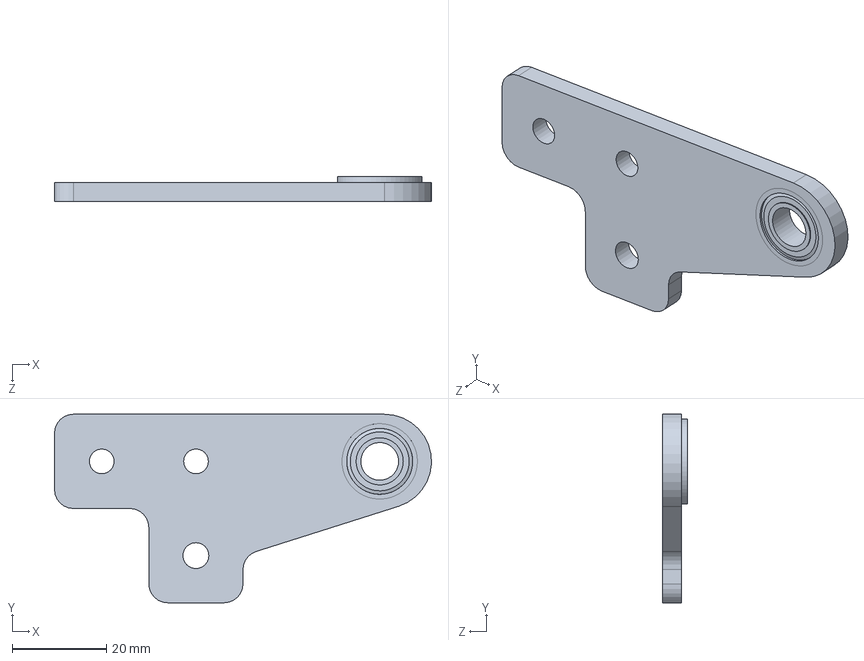
[picture p62: CAD file, 2021-08-12]
parts/Y-AXIS-ASSEM/rear-pulley-bracket.SLDPRT
80.0 x 40.0 x 5.20 mm
