greenmagics/Ender5plus_greenmaker_mod/squash ball feet/squash ball foot v1.SLDPRT

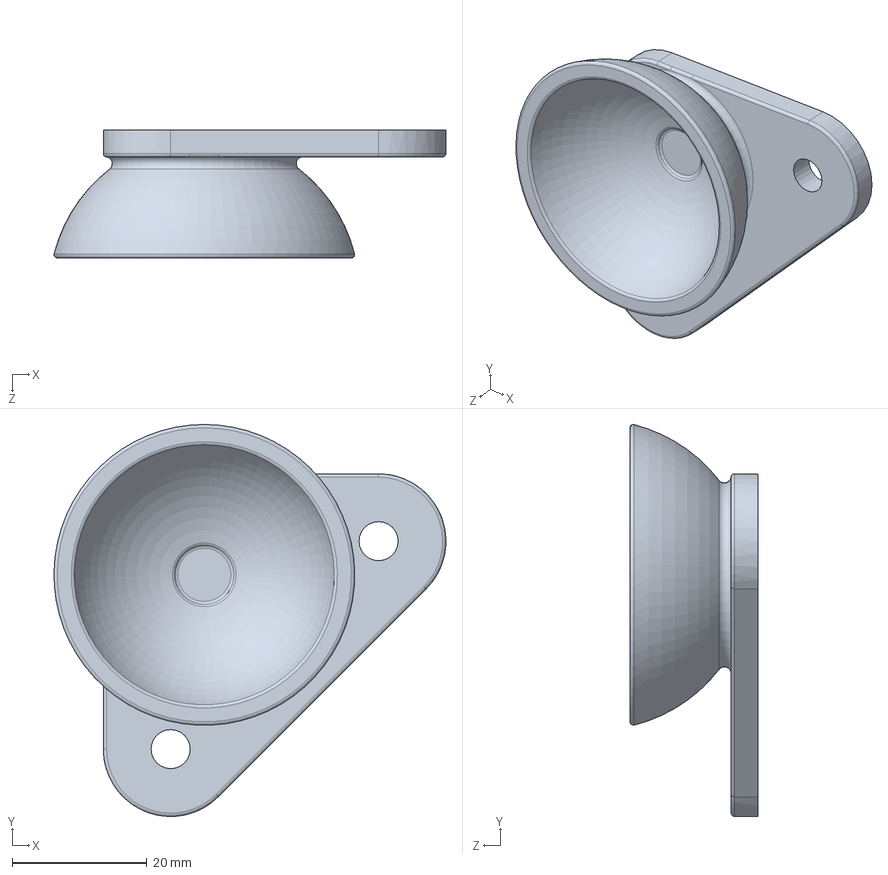
[picture p63: CAD file, 2021-08-12]
squash ball feet/squash ball foot v1.SLDPRT
58.2 x 58.2 x 19.0 mm
