greenmagics/Ender5plus_greenmaker_mod/czesci_dodane/direct/hotend_v6/heat_block.stp

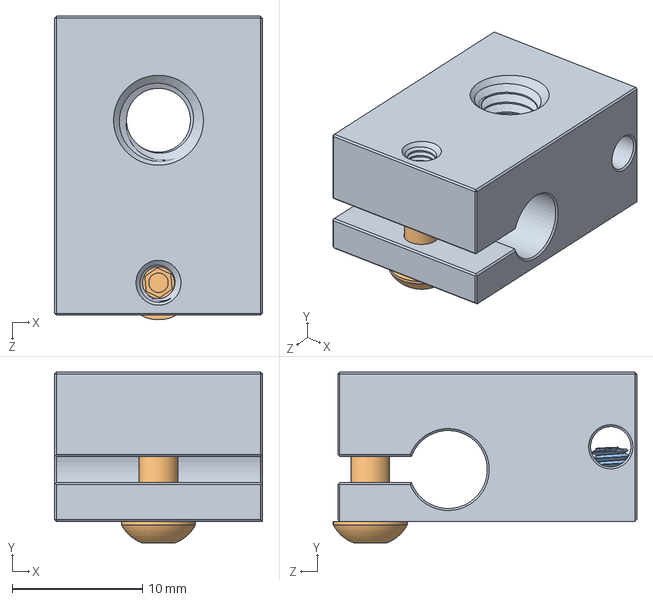
[picture p64: CAD file, 2021-08-12]
czesci_dodane/direct/hotend_v6/heat_block.stp
16.0 x 13.2 x 23.3 mm
