greenmagics/Ender5plus_greenmaker_mod/czesci_dodane/direct/karetka/cz1.SLDPRT

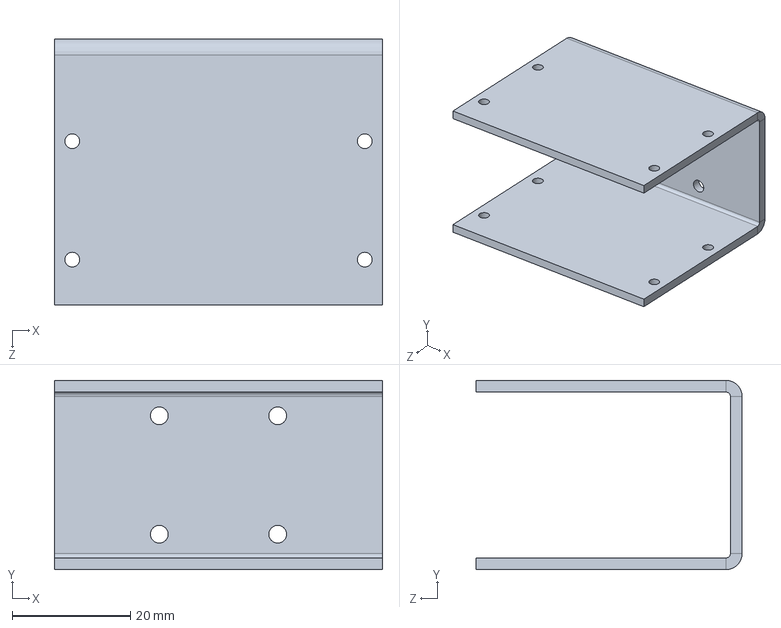
[picture p65: CAD file, 2021-08-12]
czesci_dodane/direct/karetka/cz1.SLDPRT
55.4 x 32.0 x 45.0 mm
