greenmagics/Ender5plus_greenmaker_mod/czesci_dodane/direct/monowanie_wentylatora.SLDPRT

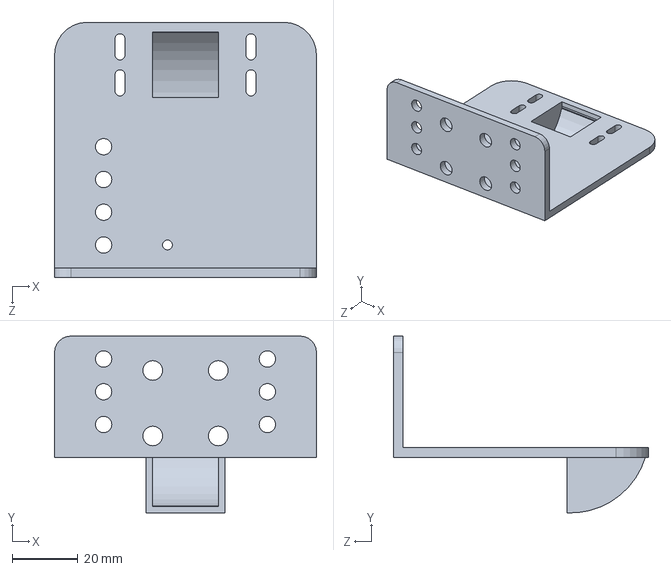
[picture p66: CAD file, 2021-08-12]
czesci_dodane/direct/monowanie_wentylatora.SLDPRT
80.0 x 54.0 x 78.0 mm
