greenmagics/Ender5plus_greenmaker_mod/czesci_dodane/GT2/pasek_gt2.SLDPRT

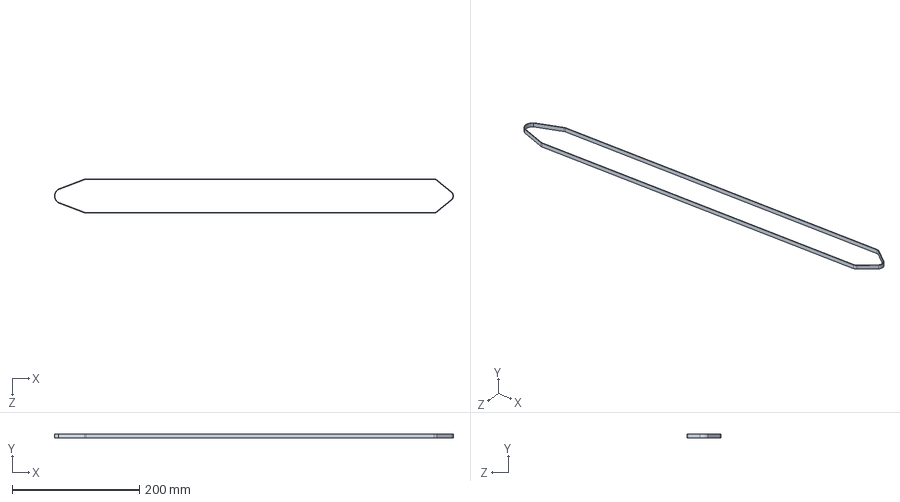
[picture p67: CAD file, 2021-08-12]
czesci_dodane/GT2/pasek_gt2.SLDPRT
628.1 x 6.00 x 54.0 mm
