greenmagics/Ender5plus_greenmaker_mod/czesci_dodane/mgn12/MGN12H.SLDPRT

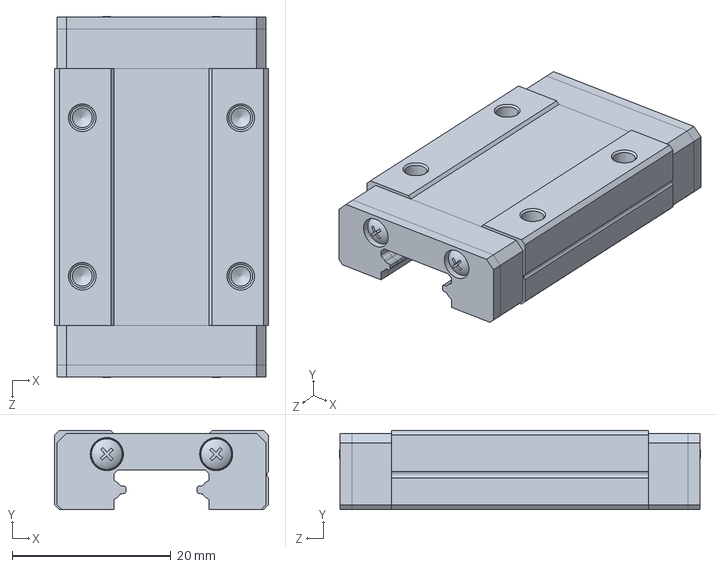
[picture p68: CAD file, 2021-08-12]
czesci_dodane/mgn12/MGN12H.SLDPRT
27.0 x 10.0 x 45.6 mm
