greenmagics/Ender5plus_greenmaker_mod/czesci_dodane/mocowania_prowadnic/mocowanie_prowadnic.stp

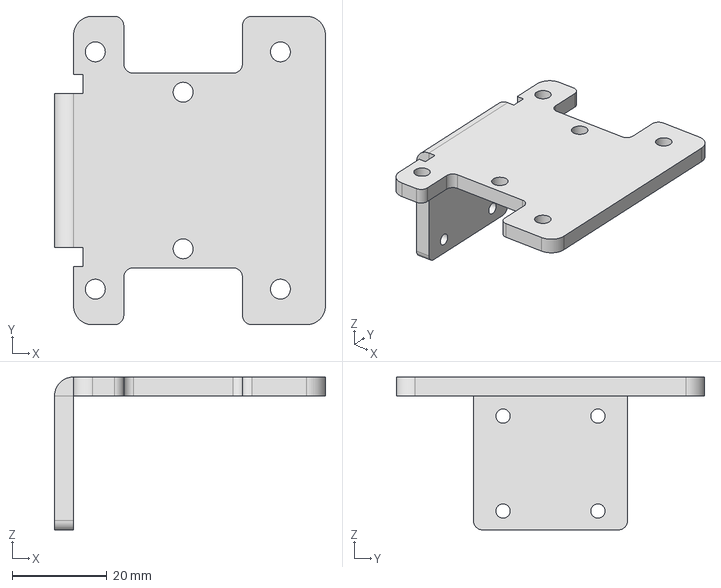
[picture p69: CAD file, 2021-08-12]
czesci_dodane/mocowania_prowadnic/mocowanie_prowadnic.stp
57.1 x 65.0 x 32.2 mm
