greenmagics/Ender5plus_greenmaker_mod/heatbreak and part cooling fan/heatbreak fan mount.SLDPRT

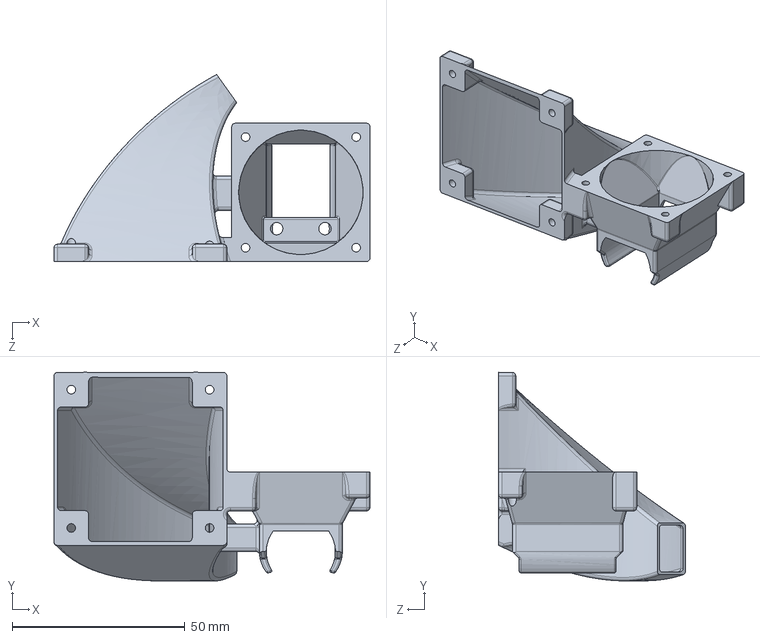
[picture p70: CAD file, 2021-08-12]
heatbreak and part cooling fan/heatbreak fan mount.SLDPRT
91.4 x 60.4 x 54.1 mm
