greenmagics/Ender5plus_greenmaker_mod/parts/build-plate-assem/glass-plate.SLDPRT

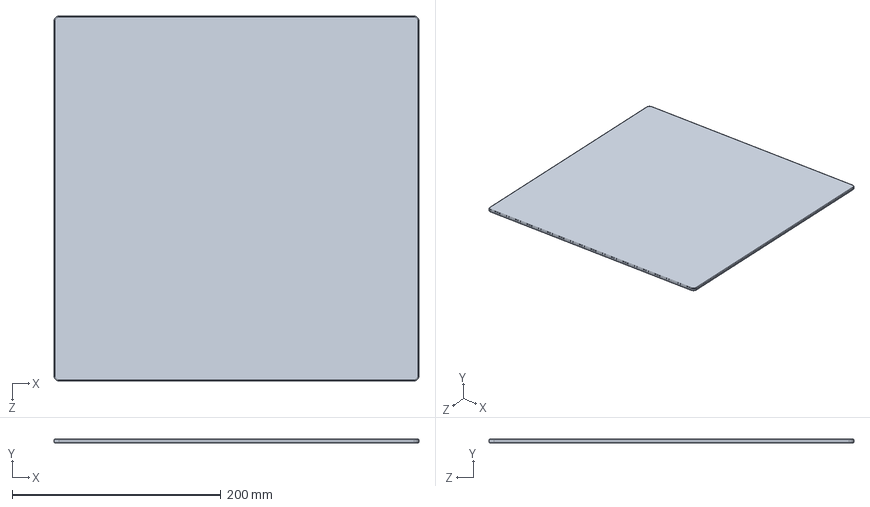
[picture p71: CAD file, 2021-08-12]
parts/build-plate-assem/glass-plate.SLDPRT
350.0 x 4.00 x 350.0 mm
