greenmagics/Ender5plus_greenmaker_mod/parts/corner-bracket.SLDPRT

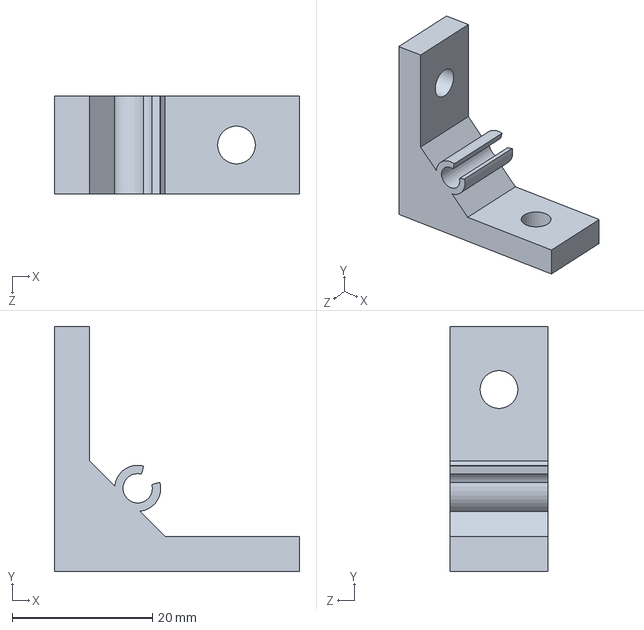
[picture p72: CAD file, 2021-08-12]
parts/corner-bracket.SLDPRT
35.0 x 35.0 x 14.0 mm
