greenmagics/Ender5plus_greenmaker_mod/parts/electronics/electronics box.SLDPRT

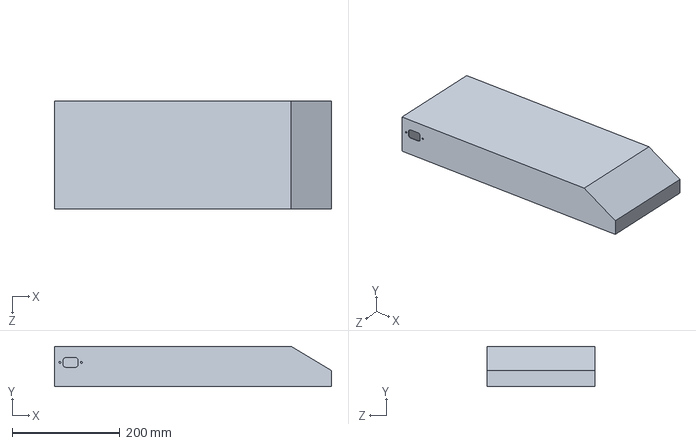
[picture p73: CAD file, 2021-08-12]
parts/electronics/electronics box.SLDPRT
515.0 x 75.0 x 200.0 mm
