greenmagics/Ender5plus_greenmaker_mod/parts/frame/base_555mm.SLDPRT

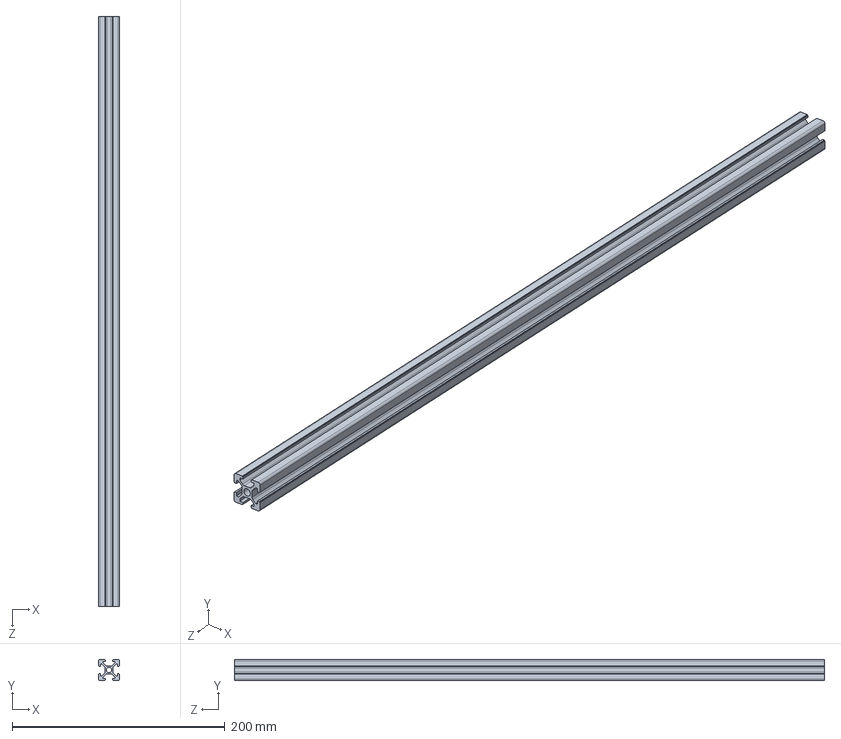
[picture p74: CAD file, 2021-08-12]
parts/frame/base_555mm.SLDPRT
20.0 x 20.0 x 555.0 mm
