greenmagics/Ender5plus_greenmaker_mod/parts/hot-end/hot-end-boot.SLDPRT

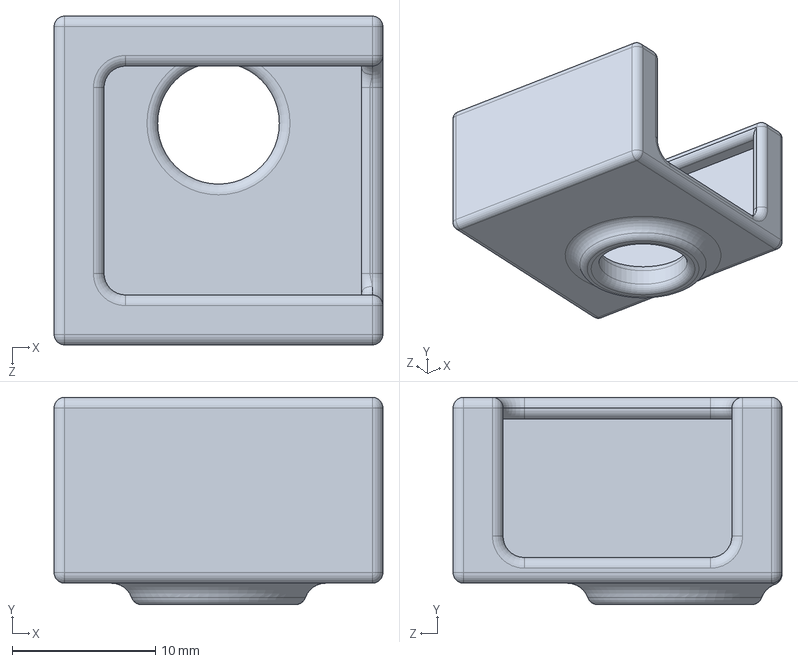
[picture p75: CAD file, 2021-08-12]
parts/hot-end/hot-end-boot.SLDPRT
23.0 x 14.5 x 23.0 mm
