greenmagics/Ender5plus_greenmaker_mod/parts/spool-holder/spool-bracket.SLDPRT

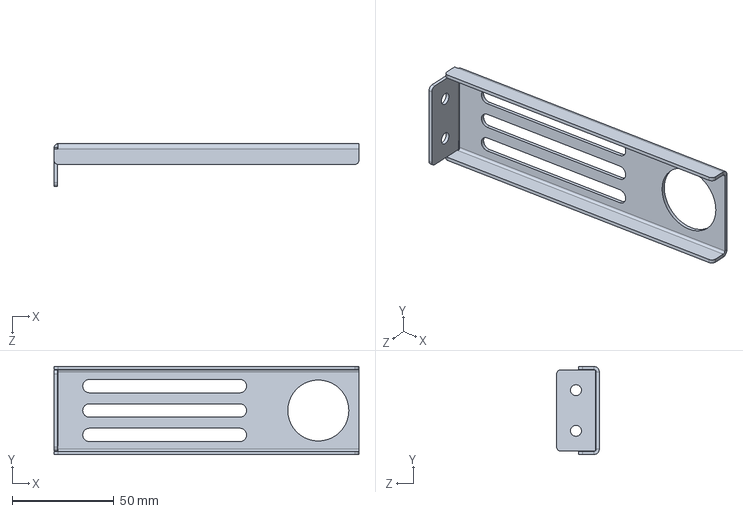
[picture p76: CAD file, 2021-08-12]
parts/spool-holder/spool-bracket.SLDPRT
150.0 x 43.4 x 21.0 mm
