greenmagics/Ender5plus_greenmaker_mod/squash ball feet/squash ball.SLDPRT

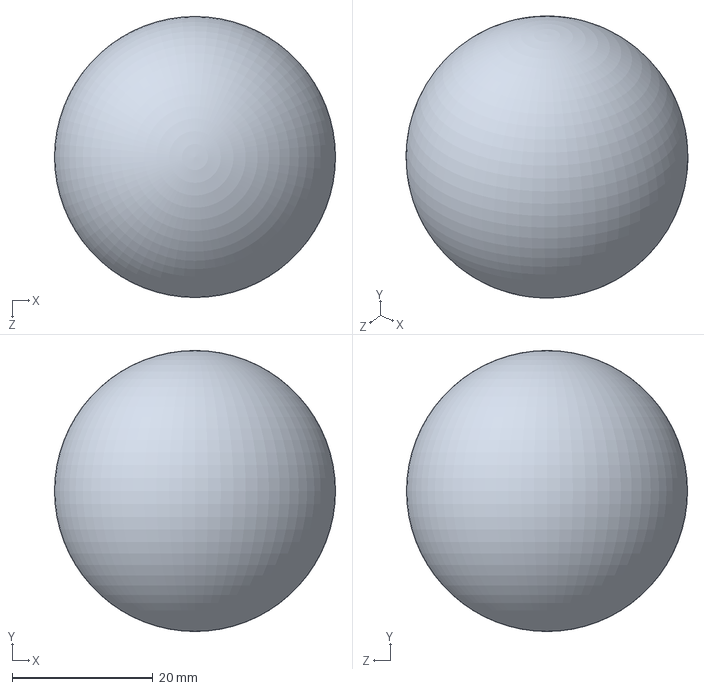
[picture p77: CAD file, 2021-08-12]
squash ball feet/squash ball.SLDPRT
40.0 x 40.0 x 40.0 mm
