greenmagics/Ender5plus_greenmaker_mod/czesci_dodane/direct/Kit Extrusora - Hotend E3D-V6_175-300.stp

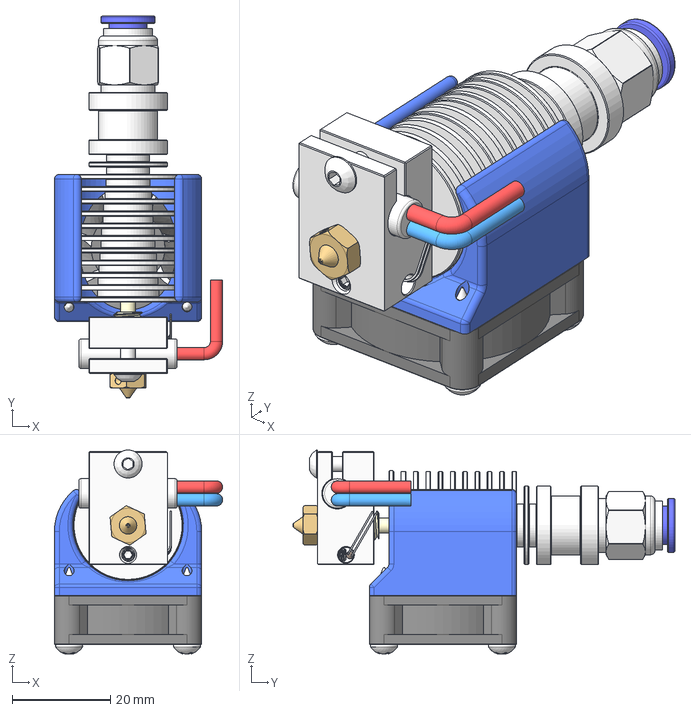
[picture p78: CAD file, 2021-08-12]
czesci_dodane/direct/Kit Extrusora - Hotend E3D-V6_175-300.stp
34.2 x 77.7 x 41.5 mm
