greenmagics/Ender5plus_greenmaker_mod/czesci_dodane/GT2/GT2 - 20T_Tension Pulley Without Teeth+603ZZ _dzino.SLDPRT

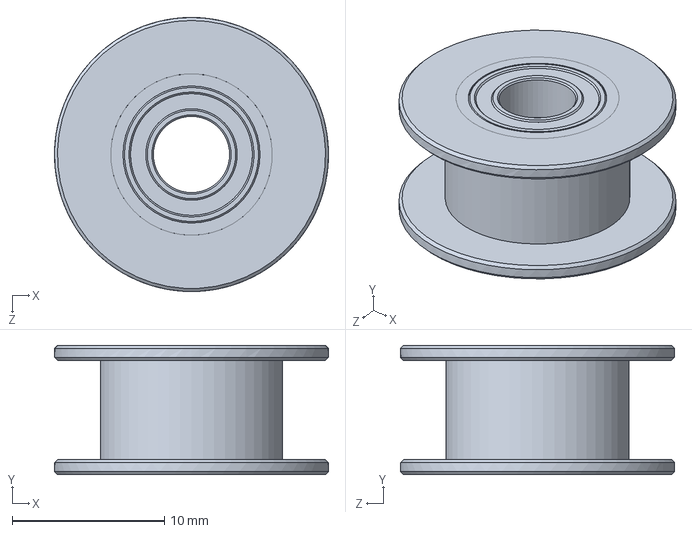
[picture p79: CAD file, 2021-08-12]
czesci_dodane/GT2/GT2 - 20T_Tension Pulley Without Teeth+603ZZ _dzino.SLDPRT
18.0 x 8.50 x 18.0 mm
