greenmagics/Ender5plus_greenmaker_mod/czesci_dodane/nema17/Top_cap.SLDPRT

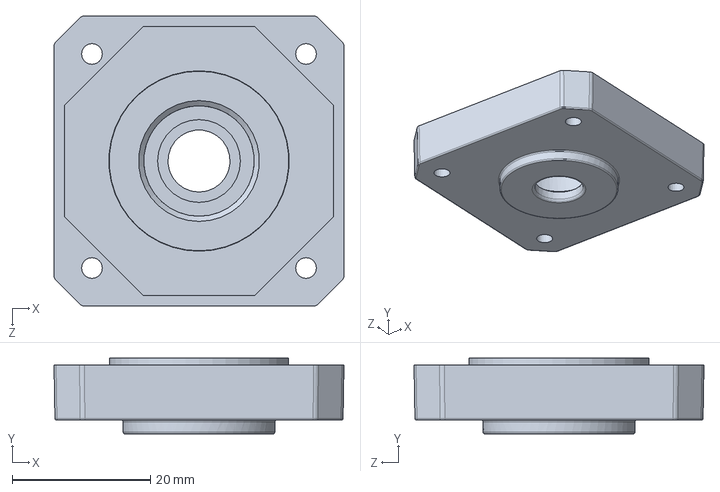
[picture p80: CAD file, 2021-08-12]
czesci_dodane/nema17/Top_cap.SLDPRT
42.0 x 11.0 x 42.0 mm
