greenmagics/Ender5plus_greenmaker_mod/parts/build-plate-assem/hotbed crossmember.SLDPRT

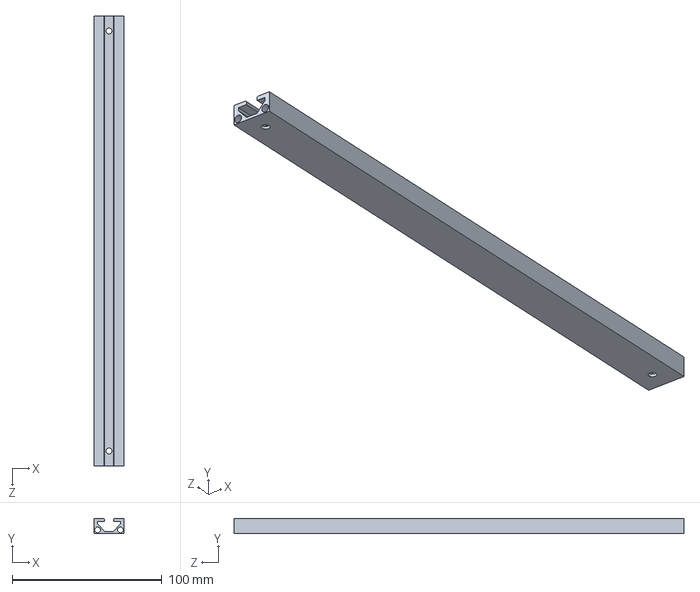
[picture p81: CAD file, 2021-08-12]
parts/build-plate-assem/hotbed crossmember.SLDPRT
20.0 x 10.0 x 300.0 mm
