greenmagics/Ender5plus_greenmaker_mod/parts/electronics/rsp-500-24.SLDPRT

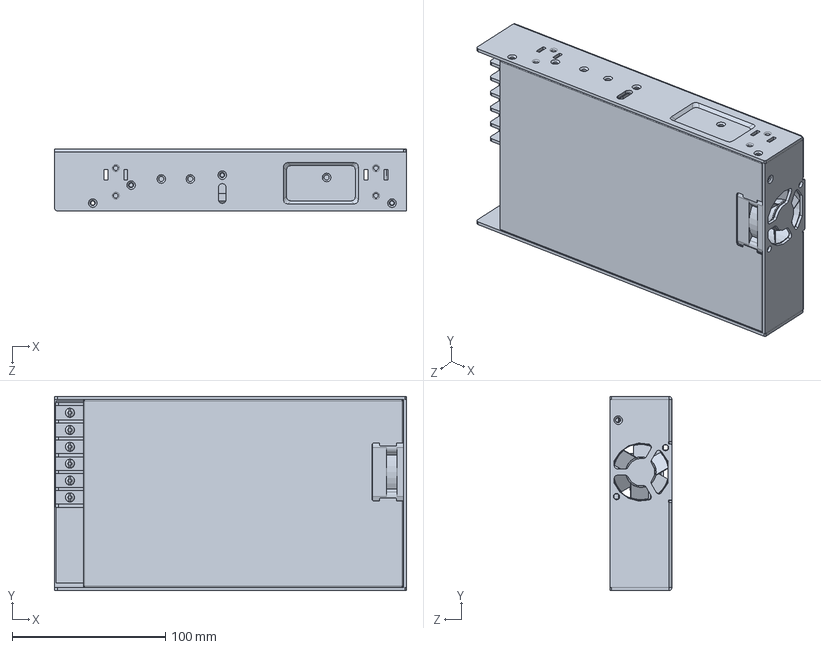
[picture p82: CAD file, 2021-08-12]
parts/electronics/rsp-500-24.SLDPRT
230.0 x 127.0 x 40.5 mm
