greenmagics/Ender5plus_greenmaker_mod/parts/extruder/BLTouch.STEP

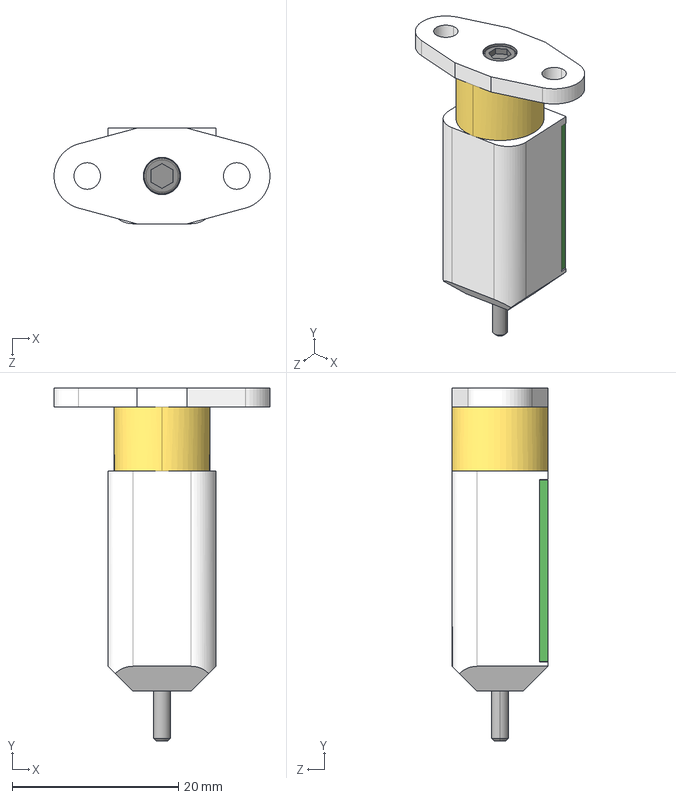
[picture p83: CAD file, 2021-08-12]
parts/extruder/BLTouch.STEP
26.0 x 42.5 x 11.5 mm
