greenmagics/Ender5plus_greenmaker_mod/parts/hot-end/hose-fitting-4x10mm.SLDPRT

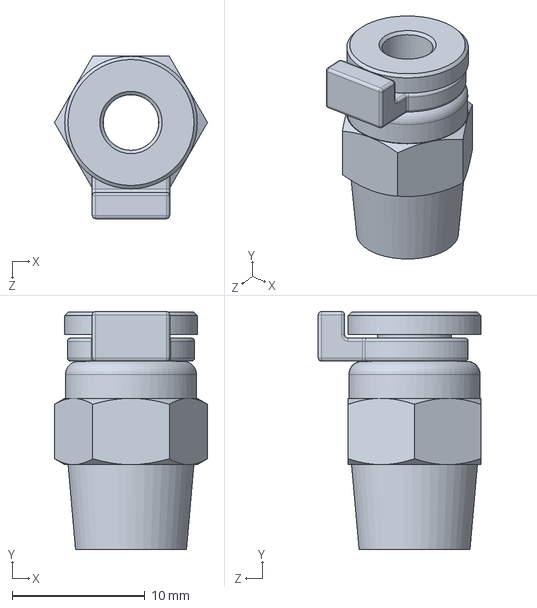
[picture p84: CAD file, 2021-08-12]
parts/hot-end/hose-fitting-4x10mm.SLDPRT
11.5 x 18.0 x 12.3 mm
