greenmagics/Ender5plus_greenmaker_mod/parts/spool-holder/spool-spindle.SLDPRT

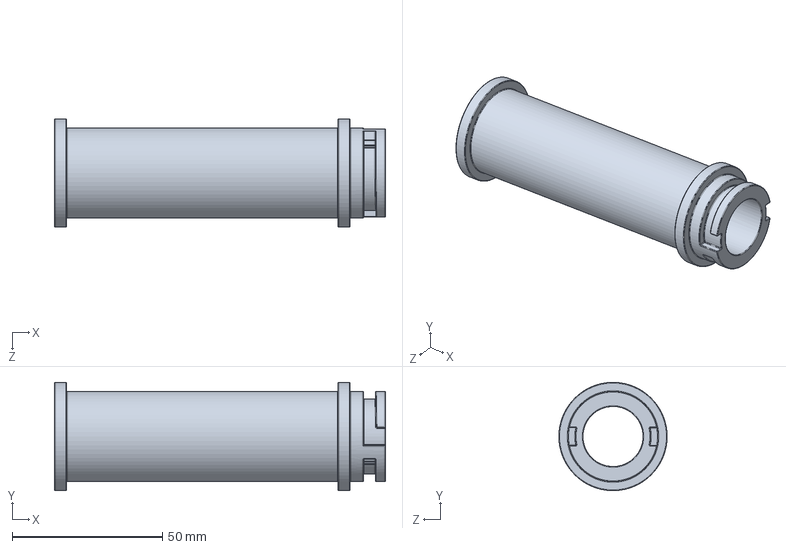
[picture p85: CAD file, 2021-08-12]
parts/spool-holder/spool-spindle.SLDPRT
110.0 x 36.0 x 36.0 mm
