greenmagics/Ender5plus_greenmaker_mod/parts/x-axis-assem/hot-end-carriage-plate.SLDPRT

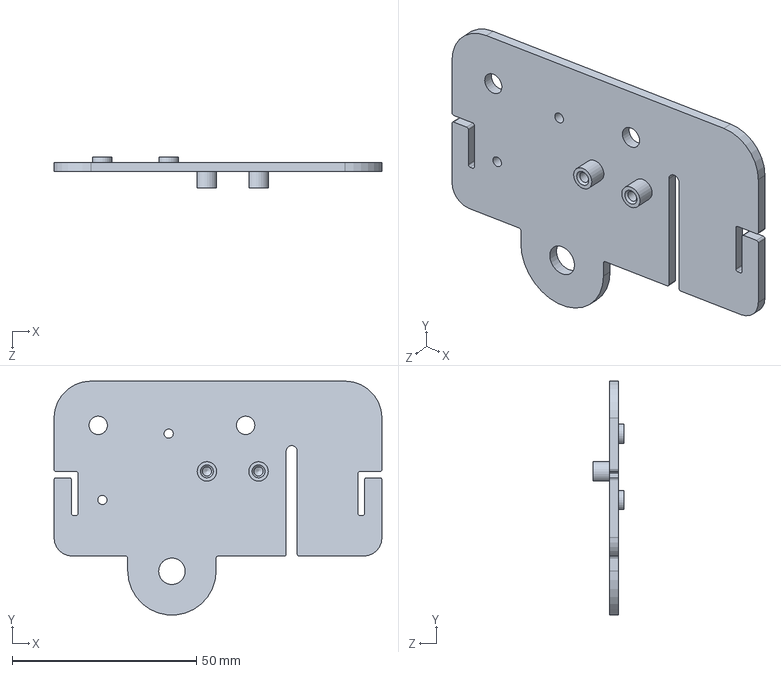
[picture p86: CAD file, 2021-08-12]
parts/x-axis-assem/hot-end-carriage-plate.SLDPRT
89.0 x 63.4 x 8.50 mm
