greenmagics/Ender5plus_greenmaker_mod/parts/x-axis-assem/wheel-assem/wheel-spacer.SLDPRT

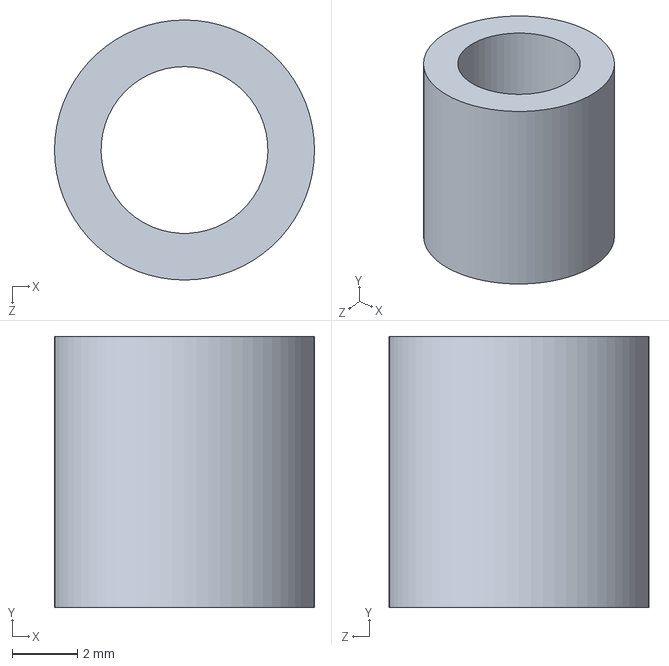
[picture p87: CAD file, 2021-08-12]
parts/x-axis-assem/wheel-assem/wheel-spacer.SLDPRT
7.95 x 8.30 x 7.95 mm
