greenmagics/Ender5plus_greenmaker_mod/czesci_dodane/direct/Nozzle V6 v3.SLDPRT

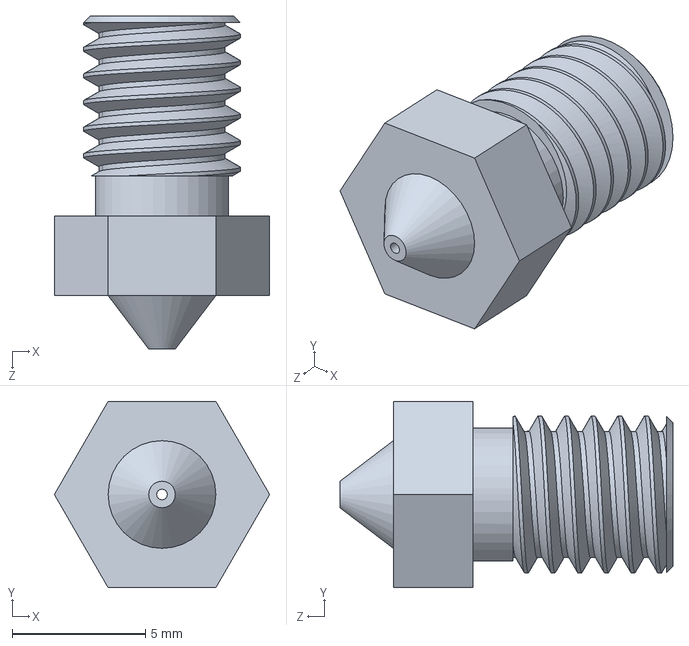
[picture p88: CAD file, 2021-08-12]
czesci_dodane/direct/Nozzle V6 v3.SLDPRT
8.08 x 7.00 x 12.5 mm
