greenmagics/Ender5plus_greenmaker_mod/czesci_dodane/GT2/GT2_40T_5_6.SLDPRT

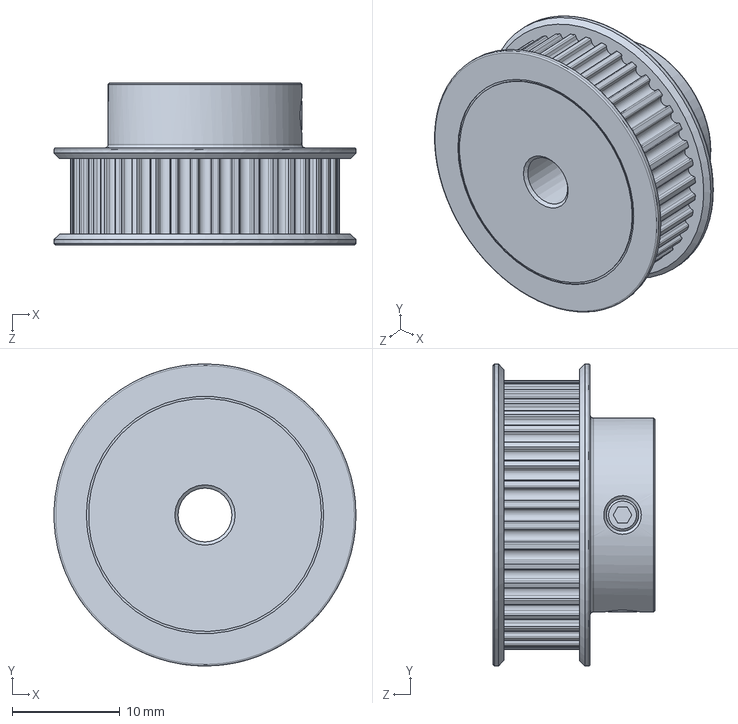
[picture p89: CAD file, 2021-08-12]
czesci_dodane/GT2/GT2_40T_5_6.SLDPRT
28.0 x 28.0 x 15.0 mm
