greenmagics/Ender5plus_greenmaker_mod/heatbreak and part cooling fan/NF-A4X20 5V PWM.STEP

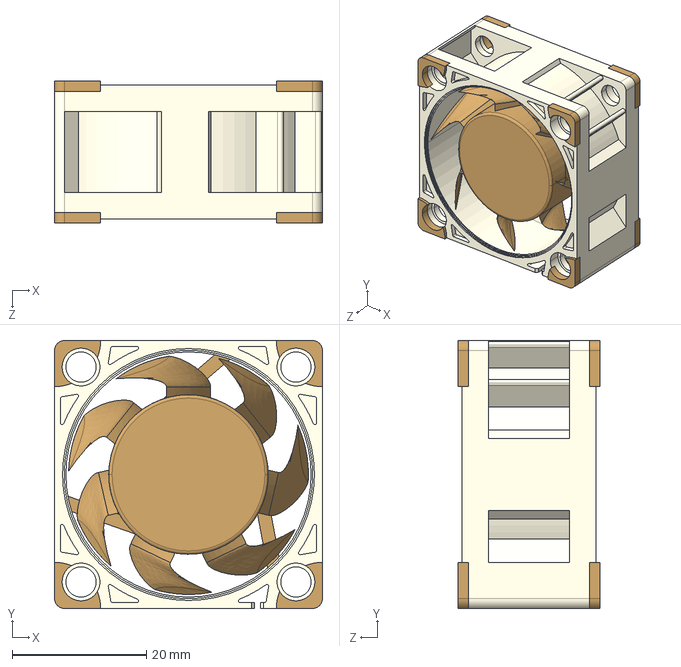
[picture p90: CAD file, 2021-08-12]
heatbreak and part cooling fan/NF-A4X20 5V PWM.STEP
39.9 x 39.9 x 21.1 mm
