greenmagics/Ender5plus_greenmaker_mod/parts/build-plate-assem/build plate crossmember.SLDPRT

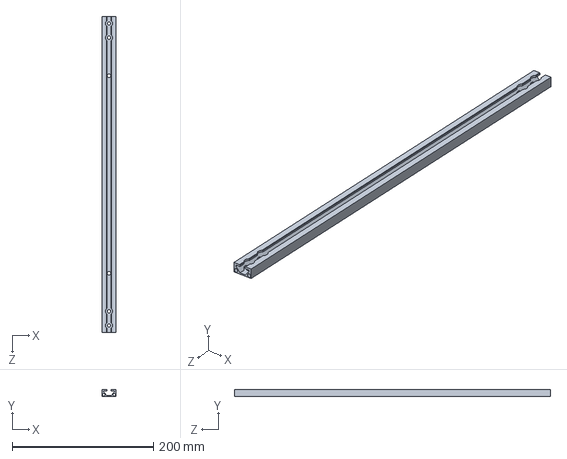
[picture p91: CAD file, 2021-08-12]
parts/build-plate-assem/build plate crossmember.SLDPRT
20.0 x 10.0 x 448.0 mm
