greenmagics/Ender5plus_greenmaker_mod/parts/extruder/extruder-gear.SLDPRT

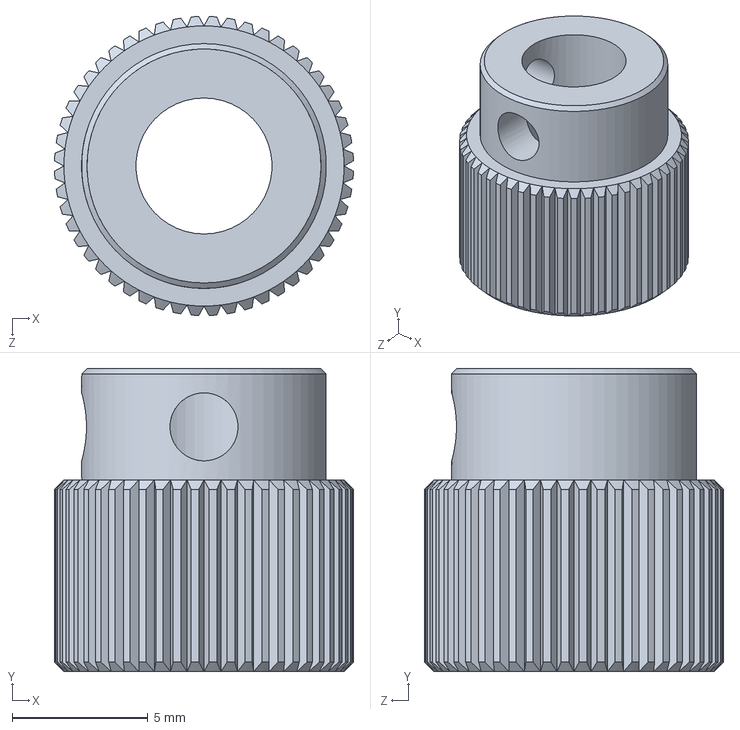
[picture p92: CAD file, 2021-08-12]
parts/extruder/extruder-gear.SLDPRT
11.0 x 11.1 x 11.0 mm
