greenmagics/Ender5plus_greenmaker_mod/parts/frame/vertical_510mm.SLDPRT

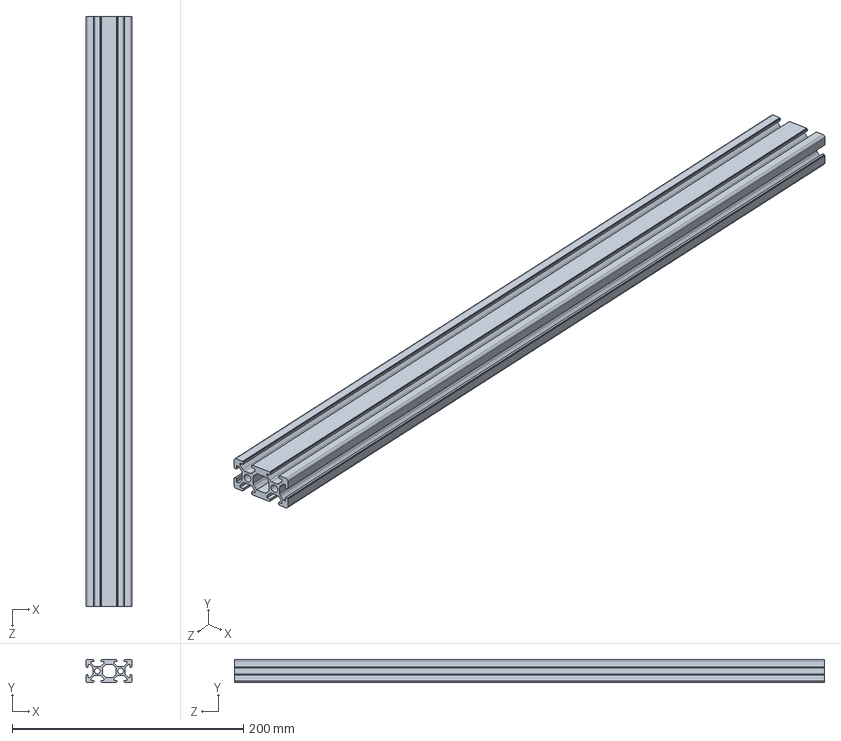
[picture p93: CAD file, 2021-08-12]
parts/frame/vertical_510mm.SLDPRT
40.0 x 20.0 x 510.0 mm
