greenmagics/Ender5plus_greenmaker_mod/parts/Y-AXIS-ASSEM/y-axis-stepper-bracket.SLDPRT

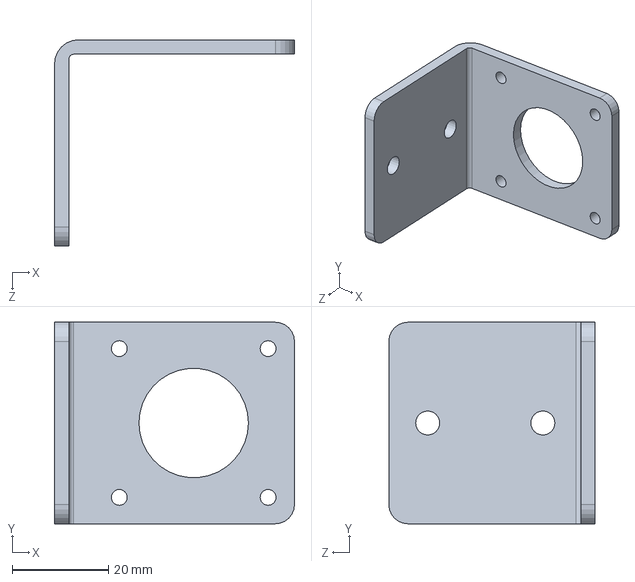
[picture p94: CAD file, 2021-08-12]
parts/Y-AXIS-ASSEM/y-axis-stepper-bracket.SLDPRT
50.0 x 42.0 x 43.0 mm
