greenmagics/Ender5plus_greenmaker_mod/czesci_dodane/direct/uchwyt_bl.SLDPRT

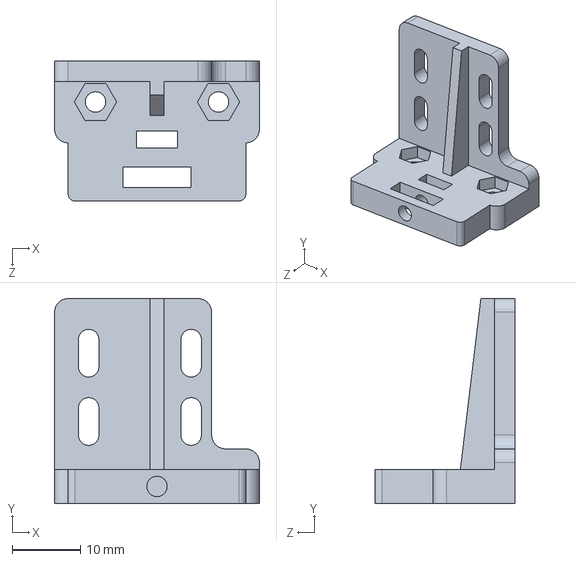
[picture p95: CAD file, 2021-08-12]
czesci_dodane/direct/uchwyt_bl.SLDPRT
30.0 x 30.0 x 20.5 mm
