greenmagics/Ender5plus_greenmaker_mod/czesci_dodane/nema17/Protective_film_bottom.SLDPRT

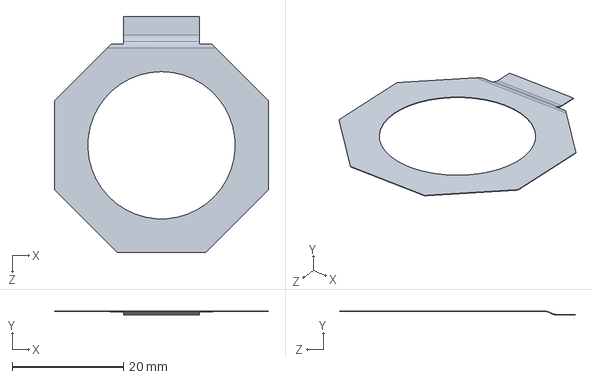
[picture p96: CAD file, 2021-08-12]
czesci_dodane/nema17/Protective_film_bottom.SLDPRT
38.5 x 0.74 x 42.4 mm
