greenmagics/Ender5plus_greenmaker_mod/heatbreak and part cooling fan/Gelid Silent 5 frame.SLDPRT

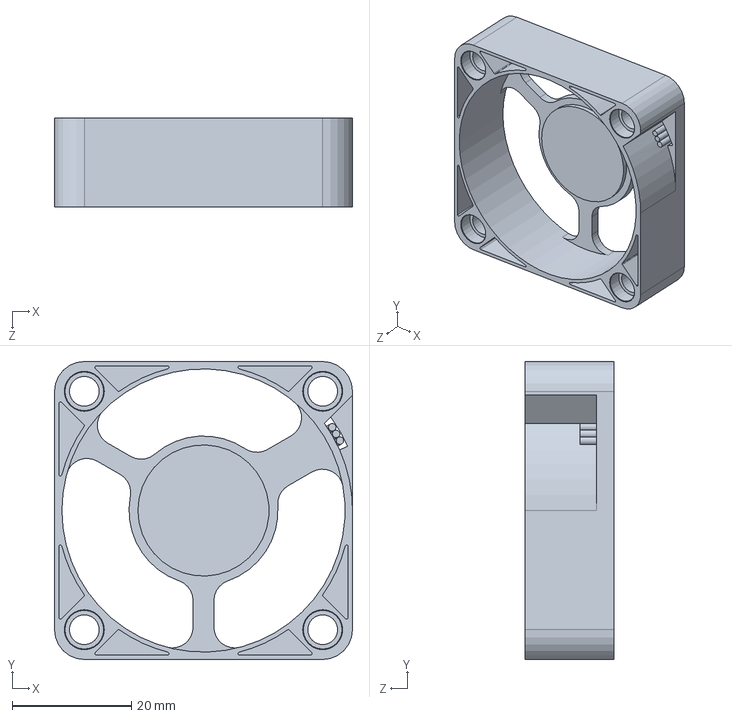
[picture p97: CAD file, 2021-08-12]
heatbreak and part cooling fan/Gelid Silent 5 frame.SLDPRT
50.0 x 50.0 x 15.0 mm
