greenmagics/Ender5plus_greenmaker_mod/parts/build-plate-assem/binder-clip.SLDPRT

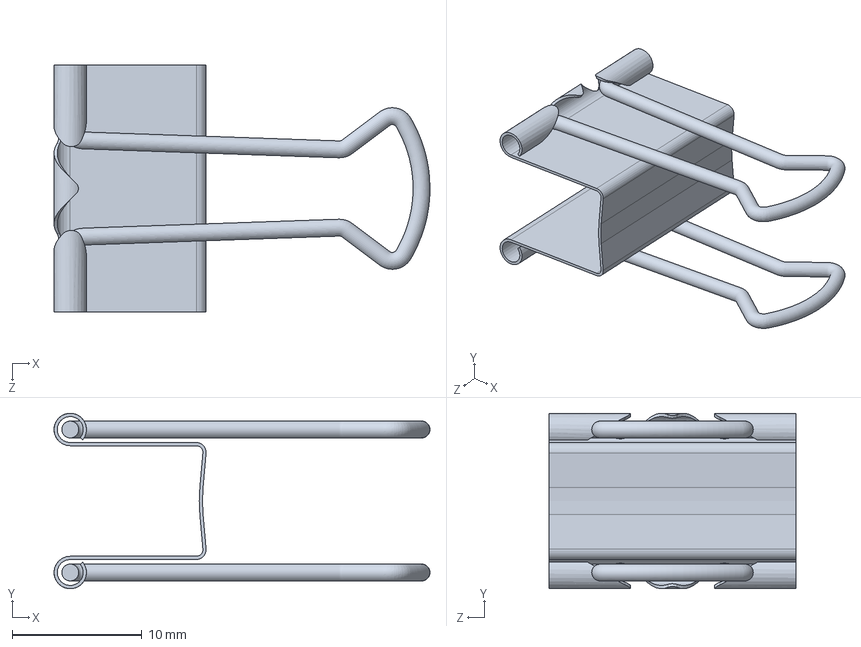
[picture p98: CAD file, 2021-08-12]
parts/build-plate-assem/binder-clip.SLDPRT
28.9 x 13.5 x 19.0 mm
