greenmagics/Ender5plus_greenmaker_mod/parts/extruder/BLTouch.step.SLDPRT

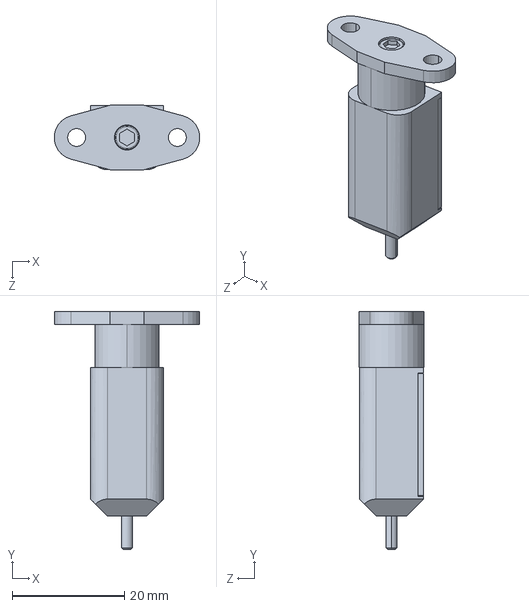
[picture p99: CAD file, 2021-08-12]
parts/extruder/BLTouch.step.SLDPRT
25.9 x 42.5 x 11.5 mm
