greenmagics/Ender5plus_greenmaker_mod/parts/hot-end/nozzle-04.SLDPRT

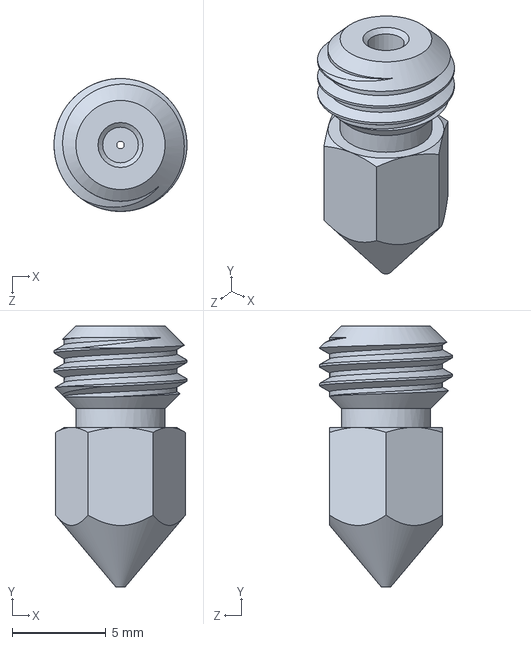
[picture p100: CAD file, 2021-08-12]
parts/hot-end/nozzle-04.SLDPRT
7.08 x 13.9 x 7.08 mm
