greenmagics/Ender5plus_greenmaker_mod/parts/Y-AXIS-ASSEM/front-pulley-bracket.SLDPRT

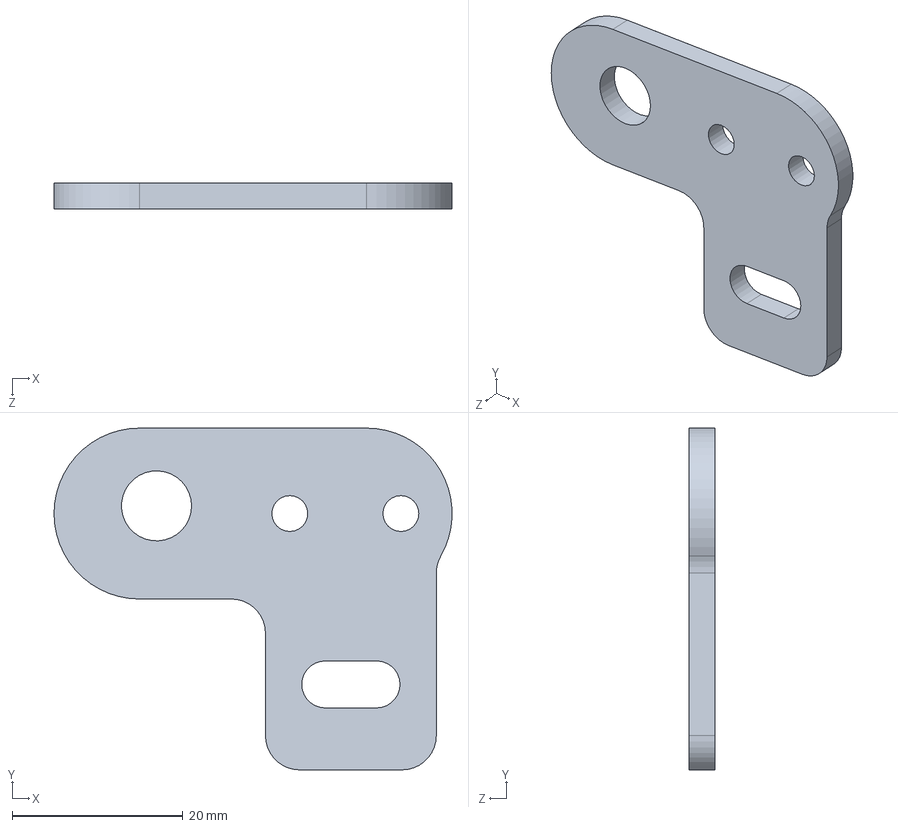
[picture p101: CAD file, 2021-08-12]
parts/Y-AXIS-ASSEM/front-pulley-bracket.SLDPRT
46.6 x 40.0 x 3.00 mm
