greenmagics/Ender5plus_greenmaker_mod/parts/z-axis-drive-assem/guide-rod.SLDPRT

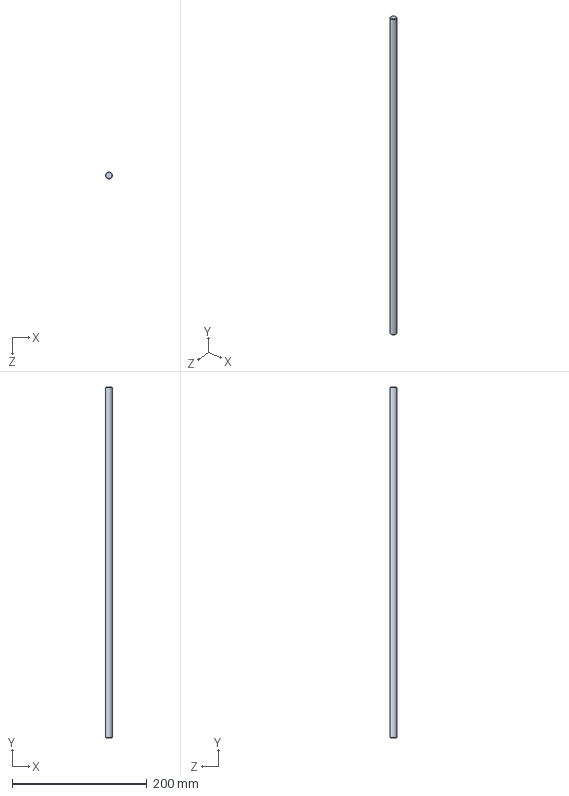
[picture p102: CAD file, 2021-08-12]
parts/z-axis-drive-assem/guide-rod.SLDPRT
10.0 x 520.0 x 10.0 mm
