greenmagics/Ender5plus_greenmaker_mod/czesci_dodane/direct/nema 17 Heatsink 40x40x11 v4.step

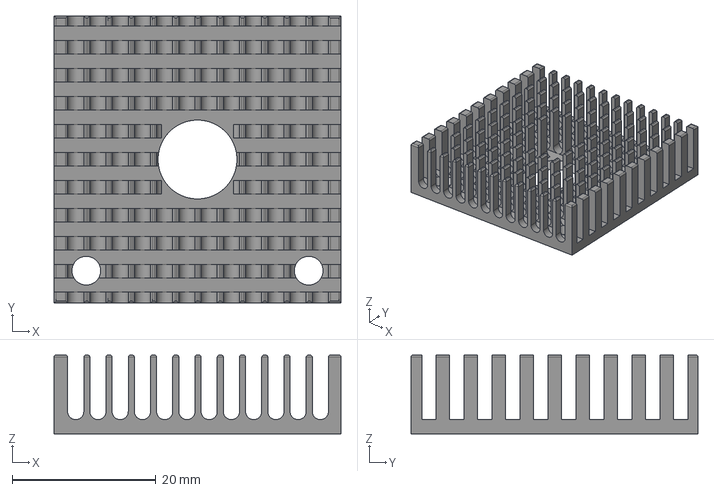
[picture p103: CAD file, 2021-08-12]
czesci_dodane/direct/nema 17 Heatsink 40x40x11 v4.step
40.0 x 40.0 x 11.0 mm
