greenmagics/Ender5plus_greenmaker_mod/czesci_dodane/nema17/Bearing.SLDPRT

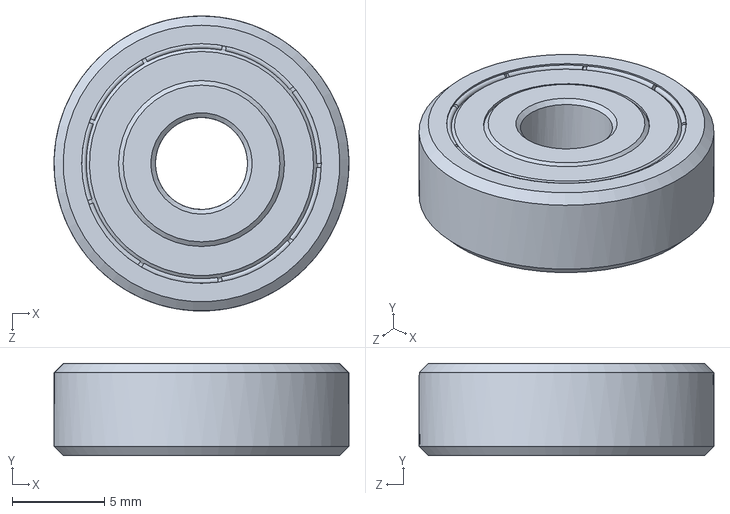
[picture p105: CAD file, 2021-08-12]
czesci_dodane/nema17/Bearing.SLDPRT
16.0 x 5.00 x 16.0 mm
