greenmagics/Ender5plus_greenmaker_mod/parts/extruder/extruder-mount-plate.SLDPRT

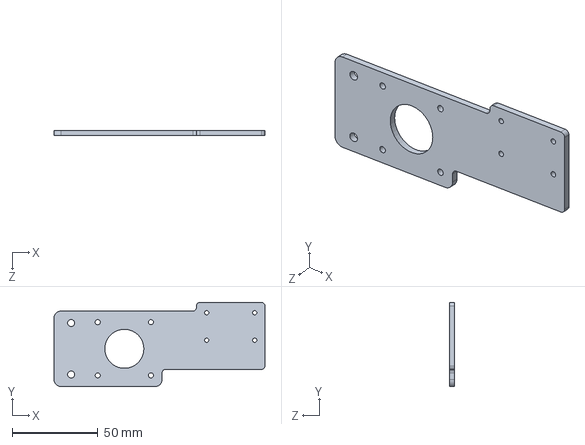
[picture p106: CAD file, 2021-08-12]
parts/extruder/extruder-mount-plate.SLDPRT
123.0 x 49.0 x 3.00 mm
