greenmagics/Ender5plus_greenmaker_mod/parts/hot-end/part-fan-duct.SLDPRT

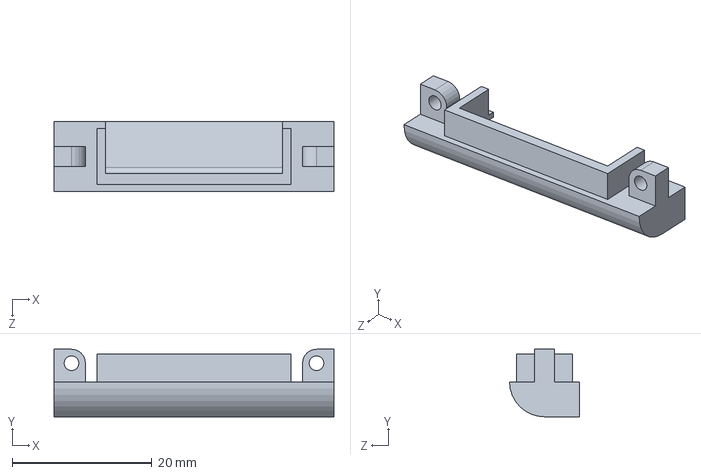
[picture p107: CAD file, 2021-08-12]
parts/hot-end/part-fan-duct.SLDPRT
40.0 x 9.65 x 10.0 mm
