greenmagics/Ender5plus_greenmaker_mod/parts/z-axis-drive-assem/z-axis-strut-20x20.SLDPRT

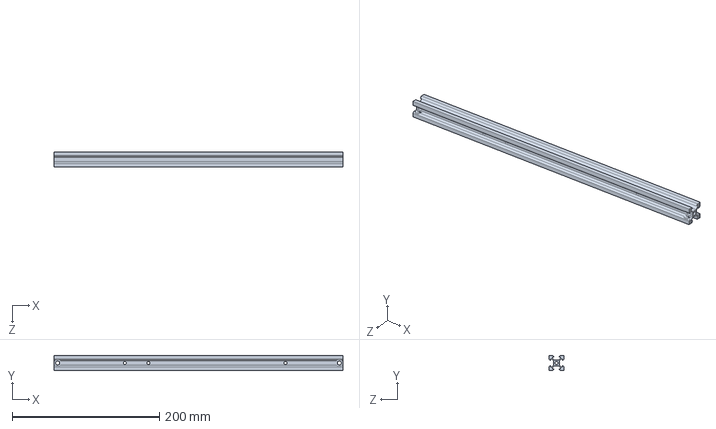
[picture p108: CAD file, 2021-08-12]
parts/z-axis-drive-assem/z-axis-strut-20x20.SLDPRT
392.0 x 20.0 x 20.0 mm
