greenmagics/Ender5plus_greenmaker_mod/czesci_dodane/direct/17HM08-1204S Nema17 Pancake 21mm.step

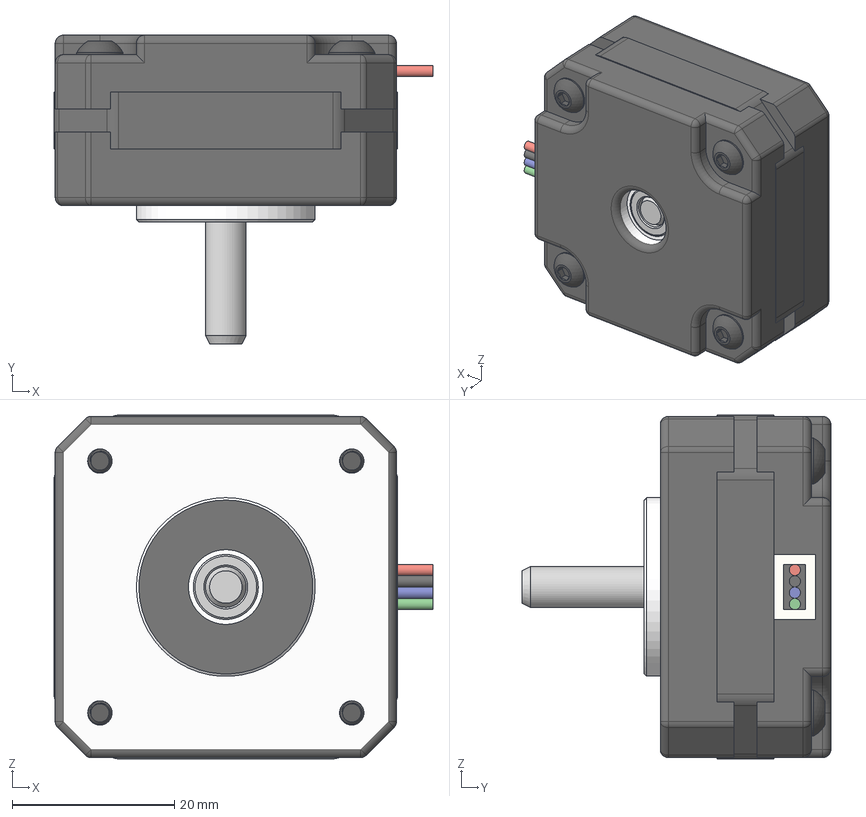
[picture p109: CAD file, 2021-08-12]
czesci_dodane/direct/17HM08-1204S Nema17 Pancake 21mm.step
46.7 x 38.0 x 42.3 mm
M3 - 12mm 92095A183 x 4
Front body
Back body
Middle body
Bearings
Shaft
Wire guard
Wires
