greenmagics/Ender5plus_greenmaker_mod/czesci_dodane/nema17/Bottom_cap.SLDPRT

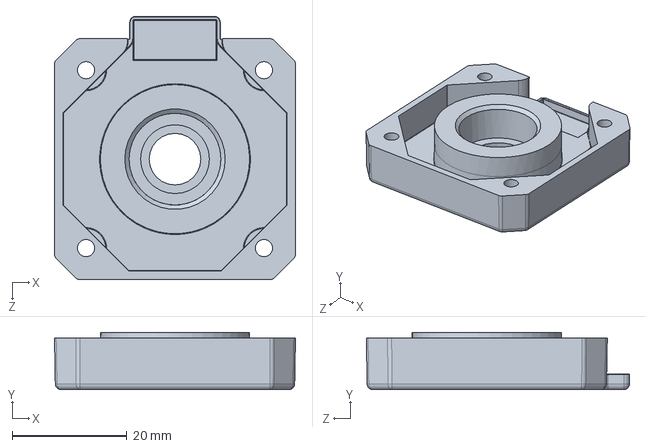
[picture p110: CAD file, 2021-08-12]
czesci_dodane/nema17/Bottom_cap.SLDPRT
42.0 x 10.0 x 45.9 mm
