greenmagics/Ender5plus_greenmaker_mod/parts/extruder/extruder-feed-arm.SLDPRT

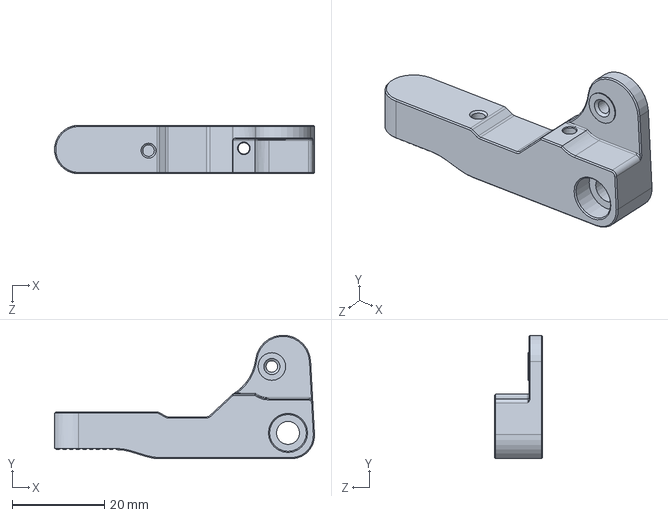
[picture p111: CAD file, 2021-08-12]
parts/extruder/extruder-feed-arm.SLDPRT
56.4 x 26.8 x 10.5 mm
