greenmagics/Ender5plus_greenmaker_mod/parts/hot-end/heat-sink.SLDPRT

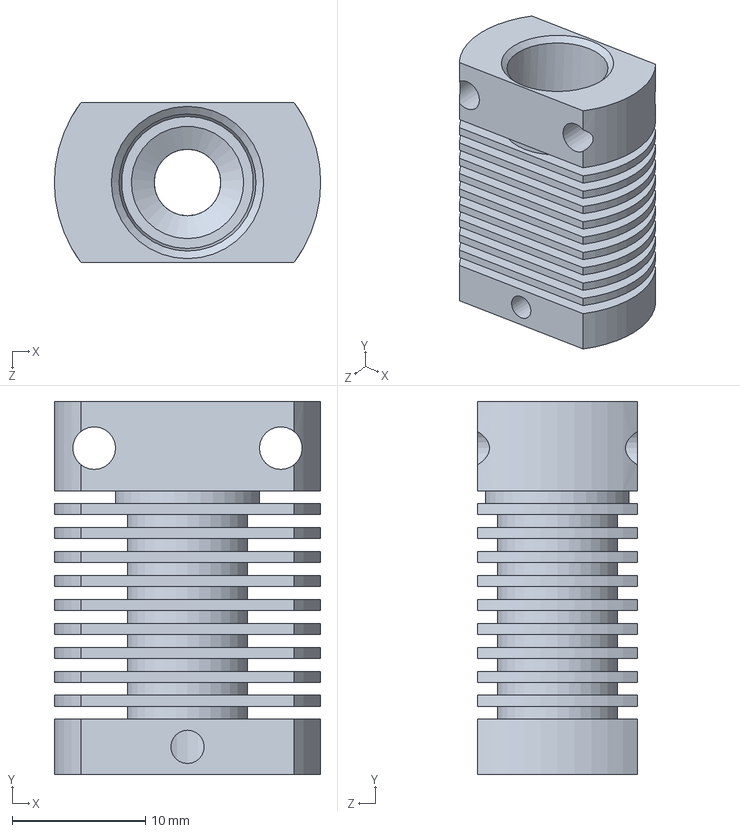
[picture p112: CAD file, 2021-08-12]
parts/hot-end/heat-sink.SLDPRT
20.0 x 28.0 x 12.0 mm
