greenmagics/Ender5plus_greenmaker_mod/czesci_dodane/direct/stabilizator.SLDPRT

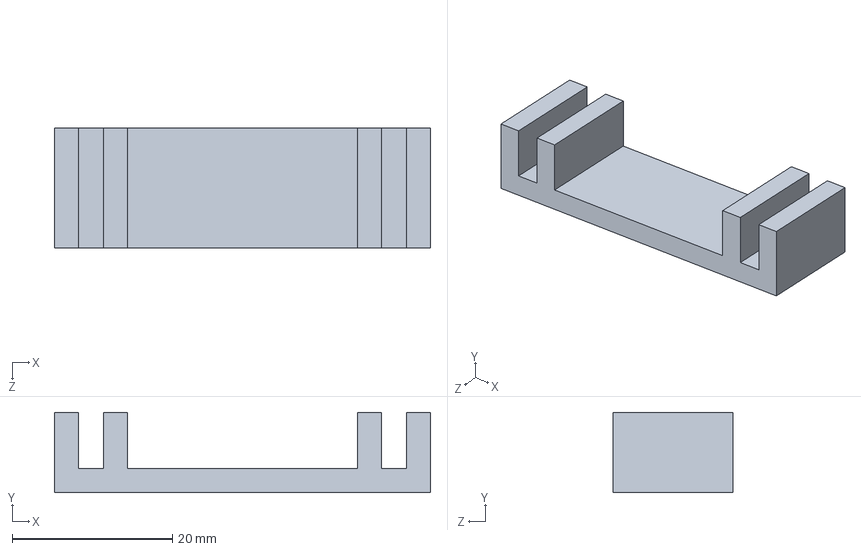
[picture p113: CAD file, 2021-08-12]
czesci_dodane/direct/stabilizator.SLDPRT
47.0 x 10.0 x 15.0 mm
