greenmagics/Ender5plus_greenmaker_mod/czesci_dodane/GT2/mocowanie_rolki.SLDPRT

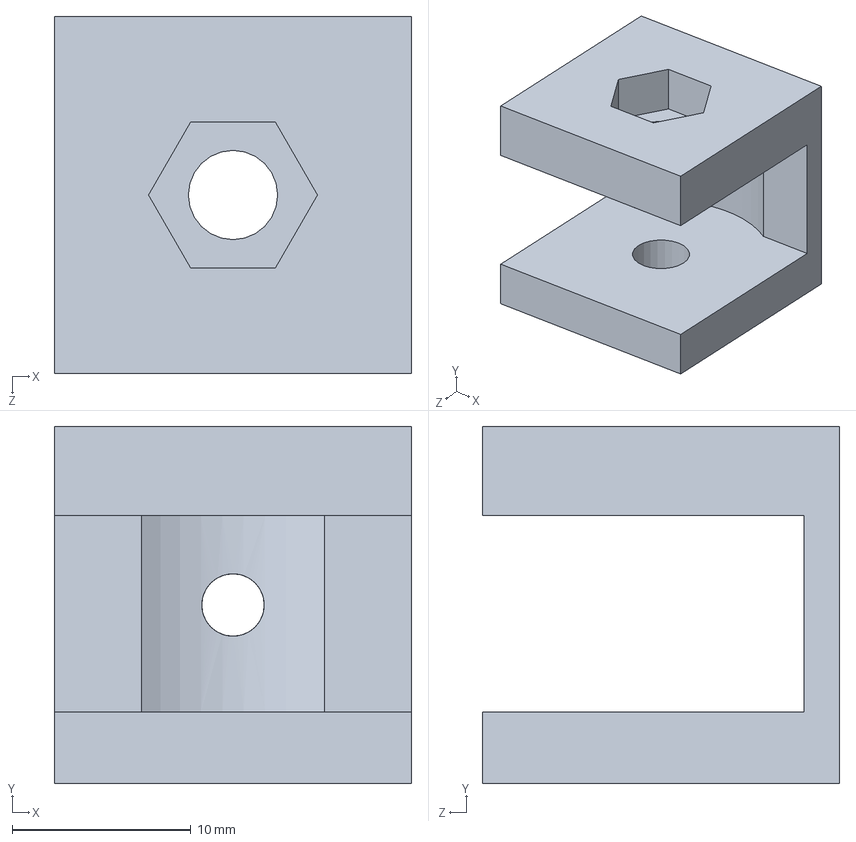
[picture p114: CAD file, 2021-08-12]
czesci_dodane/GT2/mocowanie_rolki.SLDPRT
20.0 x 20.0 x 20.0 mm
