greenmagics/Ender5plus_greenmaker_mod/czesci_dodane/nema17/Bearing_spring.SLDPRT

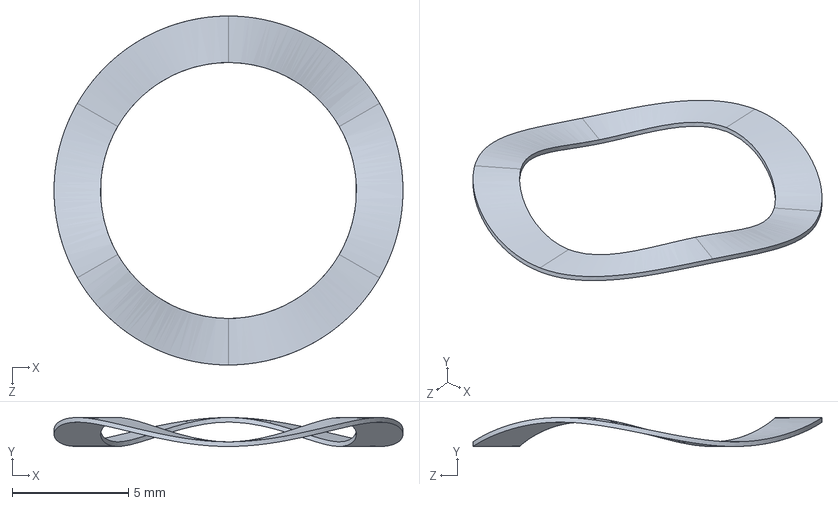
[picture p115: CAD file, 2021-08-12]
czesci_dodane/nema17/Bearing_spring.SLDPRT
15.0 x 1.25 x 15.0 mm
