greenmagics/Ender5plus_greenmaker_mod/parts/extruder/filament sensor.SLDPRT

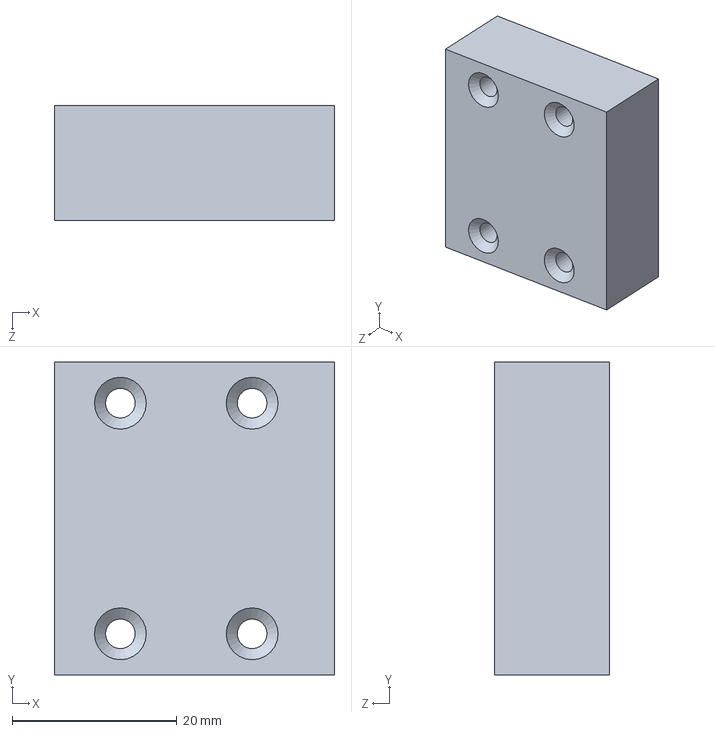
[picture p116: CAD file, 2021-08-12]
parts/extruder/filament sensor.SLDPRT
34.0 x 38.0 x 14.0 mm
