greenmagics/Ender5plus_greenmaker_mod/parts/hot-end/heat-break.SLDPRT

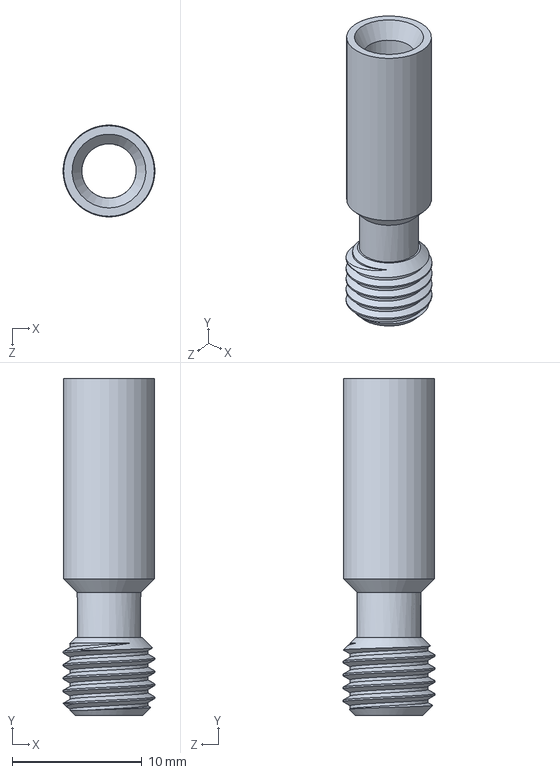
[picture p117: CAD file, 2021-08-12]
parts/hot-end/heat-break.SLDPRT
7.08 x 26.0 x 7.08 mm
