greenmagics/Ender5plus_greenmaker_mod/parts/Y-AXIS-ASSEM/drive-shaft-8mm.SLDPRT

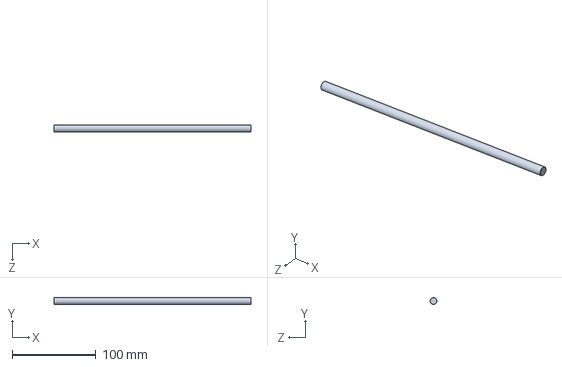
[picture p118: CAD file, 2021-08-12]
parts/Y-AXIS-ASSEM/drive-shaft-8mm.SLDPRT
235.0 x 8.00 x 8.00 mm
