greenmagics/Ender5plus_greenmaker_mod/parts/z-axis-drive-assem/stepper-motor.SLDPRT

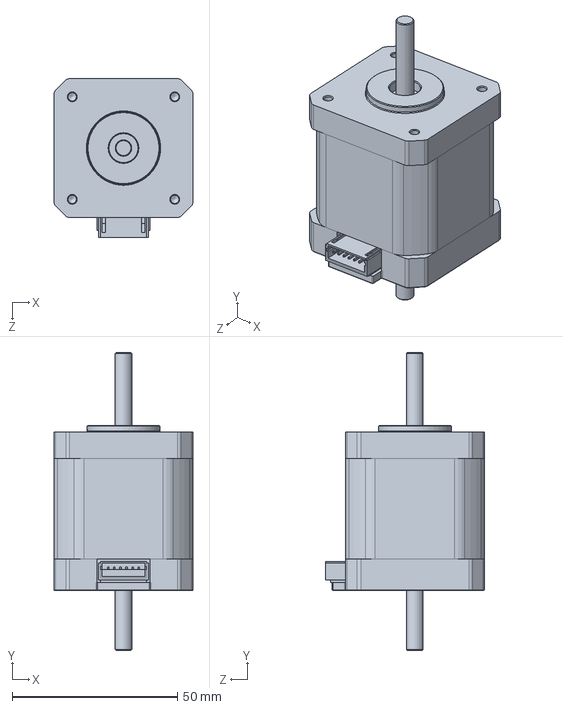
[picture p119: CAD file, 2021-08-12]
parts/z-axis-drive-assem/stepper-motor.SLDPRT
42.0 x 90.1 x 48.0 mm
