greenmagics/Ender5plus_greenmaker_mod/czesci_dodane/direct/E3D V6 Lite v8.SLDPRT

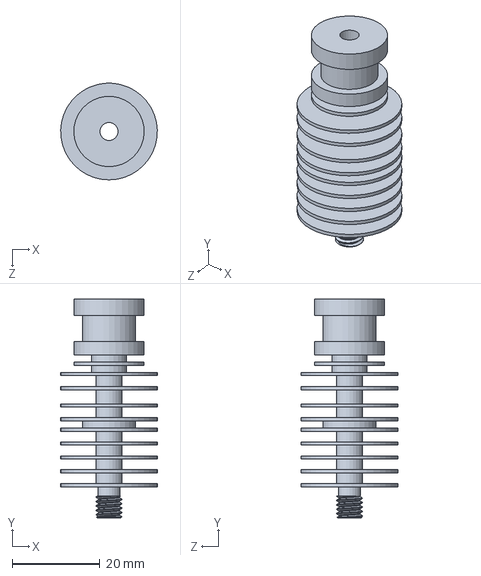
[picture p120: CAD file, 2021-08-12]
czesci_dodane/direct/E3D V6 Lite v8.SLDPRT
22.0 x 49.8 x 22.0 mm
