greenmagics/Ender5plus_greenmaker_mod/parts/extruder/extruder-pulley.SLDPRT

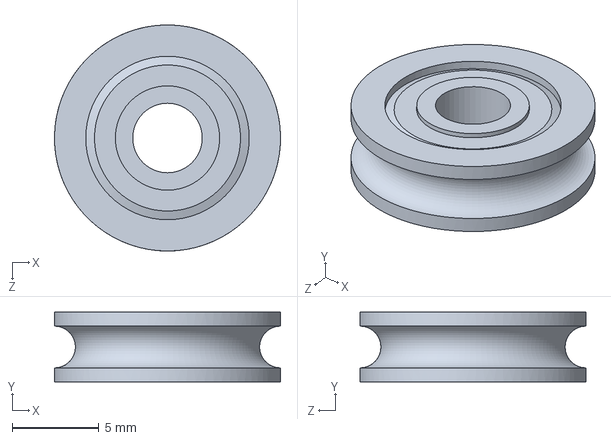
[picture p121: CAD file, 2021-08-12]
parts/extruder/extruder-pulley.SLDPRT
13.0 x 4.00 x 13.0 mm
