greenmagics/Ender5plus_greenmaker_mod/parts/hot-end/hot-end-heater-block.SLDPRT

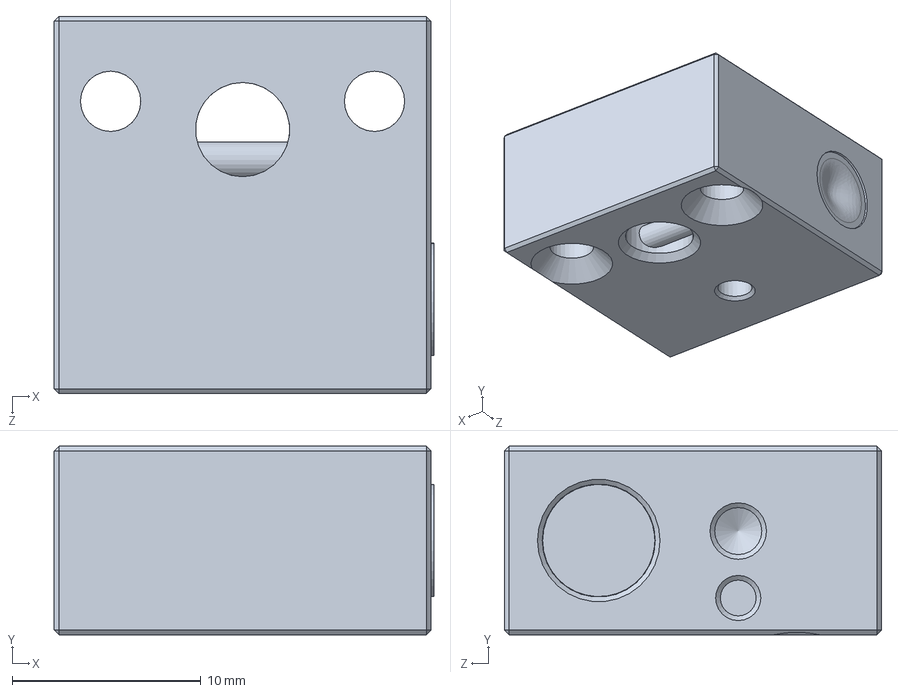
[picture p122: CAD file, 2021-08-12]
parts/hot-end/hot-end-heater-block.SLDPRT
20.1 x 10.0 x 20.0 mm
