greenmagics/Ender5plus_greenmaker_mod/parts/x-axis-assem/pulley-half.SLDPRT

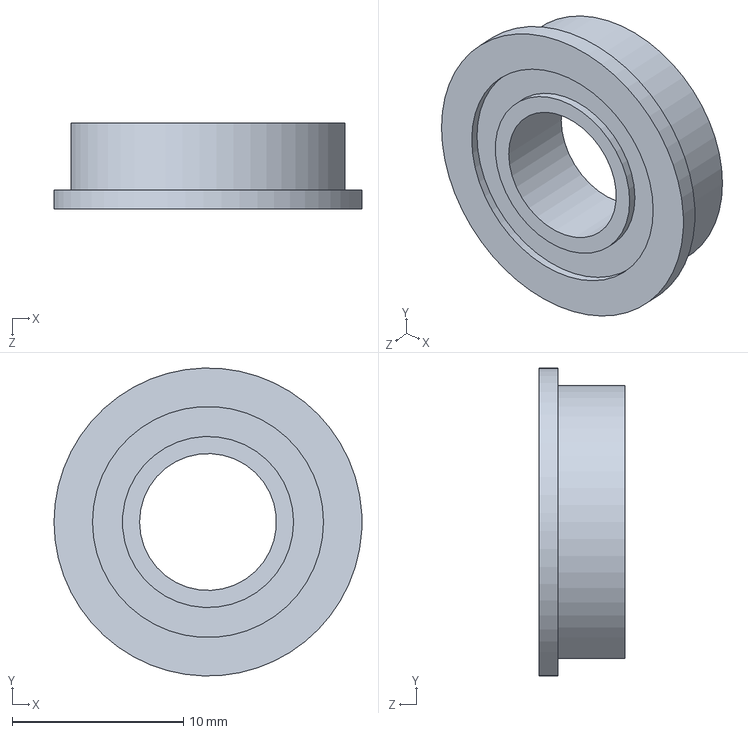
[picture p123: CAD file, 2021-08-12]
parts/x-axis-assem/pulley-half.SLDPRT
18.0 x 18.0 x 5.00 mm
