greenmagics/Ender5plus_greenmaker_mod/czesci_dodane/direct/bmg_extruder.SLDPRT

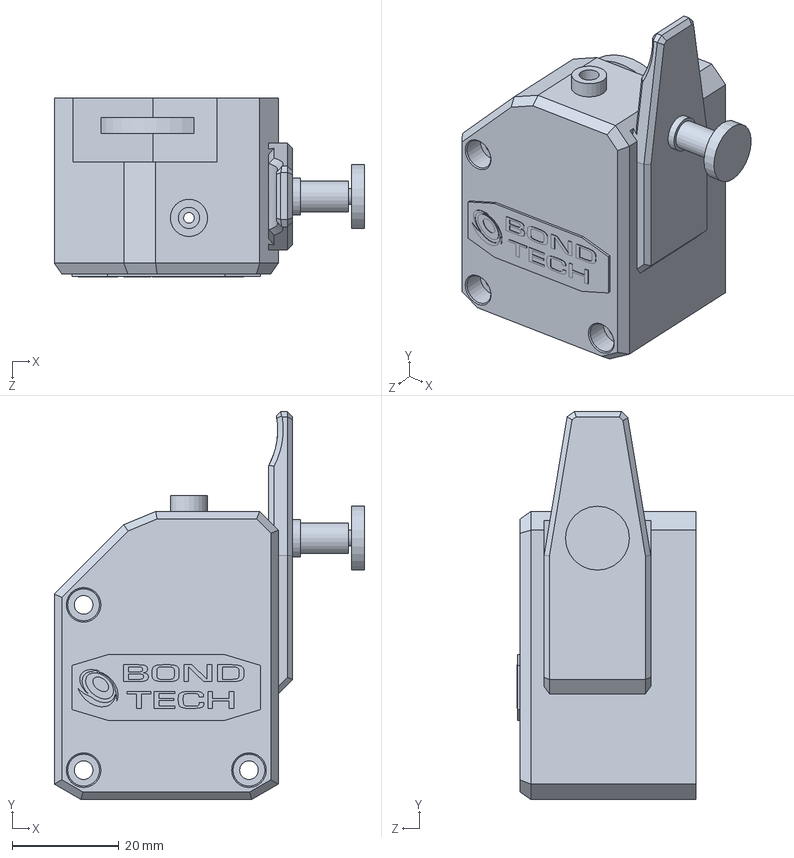
[picture p124: CAD file, 2021-08-12]
czesci_dodane/direct/bmg_extruder.SLDPRT
58.2 x 72.8 x 33.6 mm
