greenmagics/Ender5plus_greenmaker_mod/parts/extruder/hose-fitting-4x6mm.SLDPRT

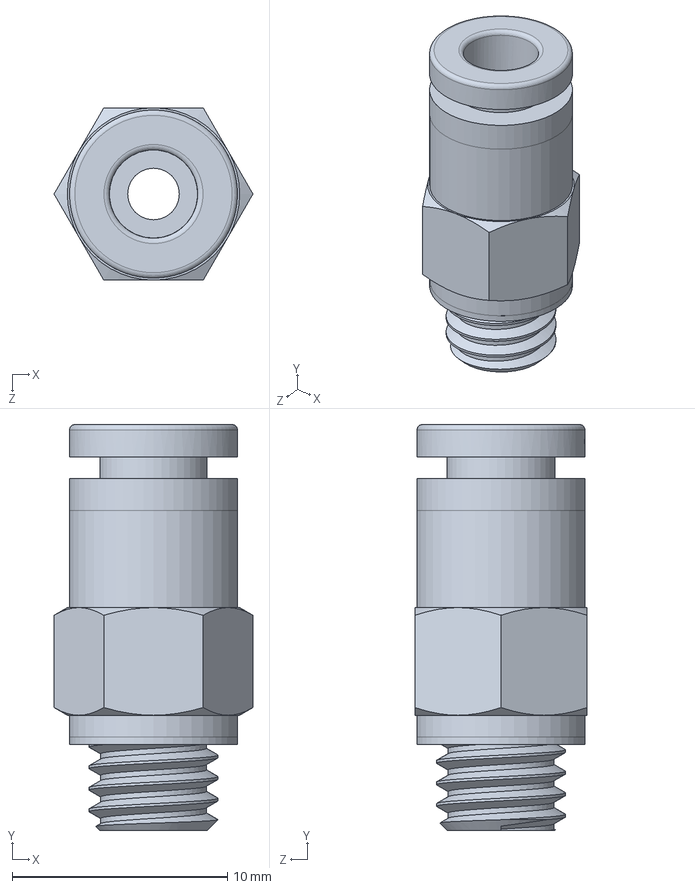
[picture p125: CAD file, 2021-08-12]
parts/extruder/hose-fitting-4x6mm.SLDPRT
9.24 x 18.9 x 8.00 mm
