greenmagics/Ender5plus_greenmaker_mod/parts/hot-end/fan-shroud.SLDPRT

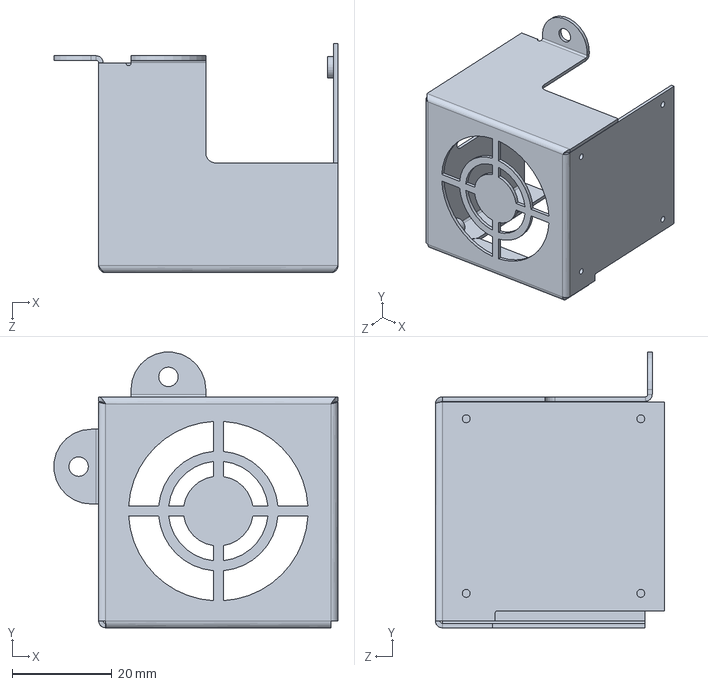
[picture p126: CAD file, 2021-08-12]
parts/hot-end/fan-shroud.SLDPRT
56.9 x 55.3 x 46.0 mm
