greenmagics/Ender5plus_greenmaker_mod/parts/x-axis-assem/x-axis-belt.sldprt

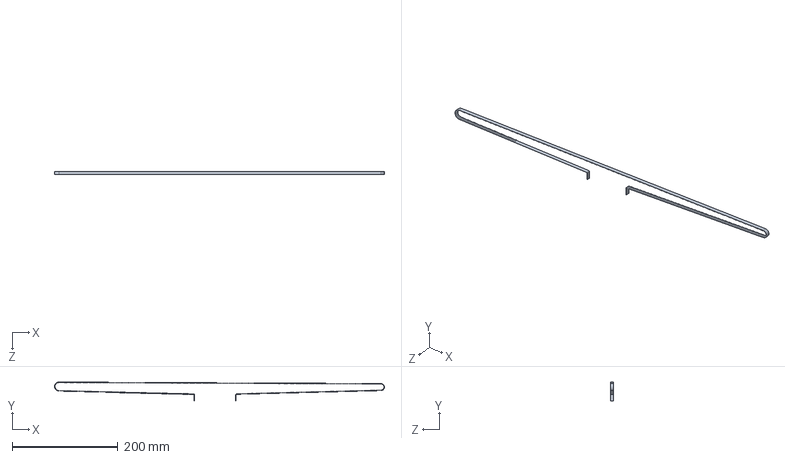
[picture p127: CAD file, 2021-08-12]
parts/x-axis-assem/x-axis-belt.sldprt
624.3 x 35.9 x 6.00 mm
