greenmagics/Ender5plus_greenmaker_mod/parts/z-axis-drive-assem/guide-rod-bracket.SLDPRT

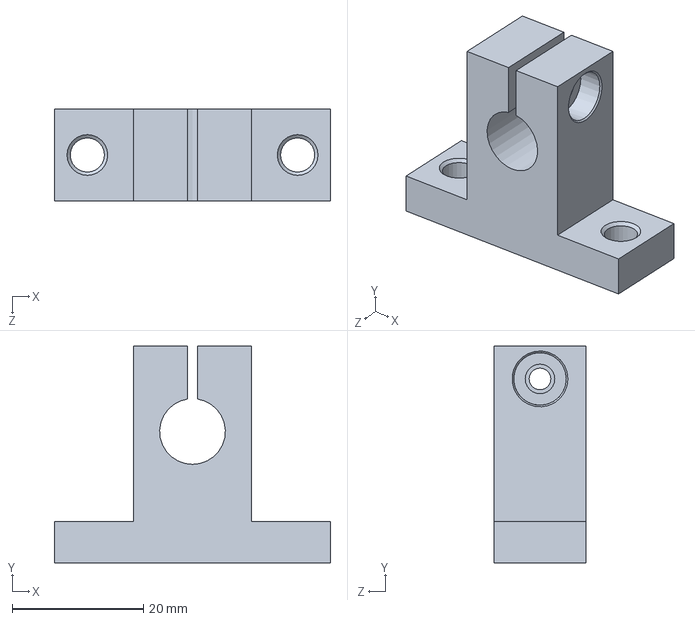
[picture p128: CAD file, 2021-08-12]
parts/z-axis-drive-assem/guide-rod-bracket.SLDPRT
42.0 x 33.0 x 14.0 mm
