greenmagics/Ender5plus_greenmaker_mod/czesci_dodane/direct/E3D V6 Heaterblock v4.SLDPRT

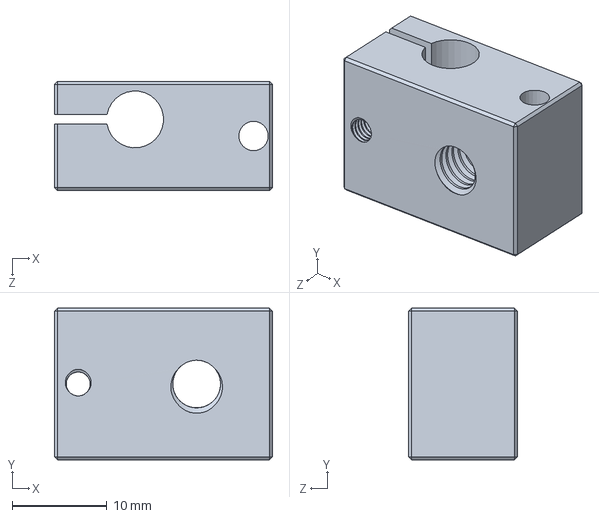
[picture p129: CAD file, 2021-08-12]
czesci_dodane/direct/E3D V6 Heaterblock v4.SLDPRT
23.0 x 16.0 x 11.5 mm
