greenmagics/Ender5plus_greenmaker_mod/parts/extruder/extruder-feed-bracket.SLDPRT

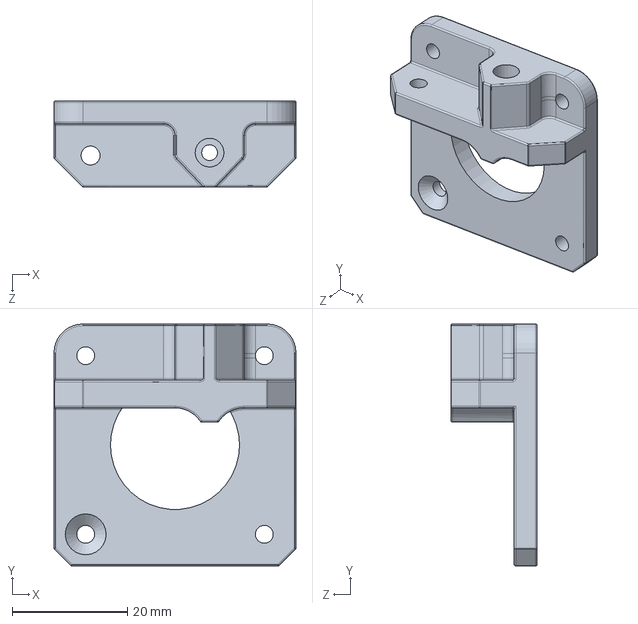
[picture p130: CAD file, 2021-08-12]
parts/extruder/extruder-feed-bracket.SLDPRT
42.0 x 42.0 x 15.0 mm
