greenmagics/Ender5plus_greenmaker_mod/parts/hot-end/part-cooling-fan.SLDPRT

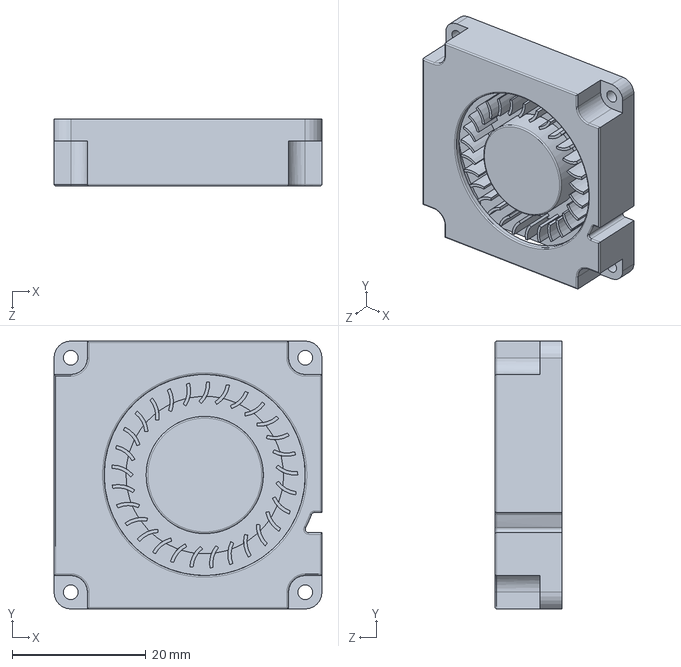
[picture p131: CAD file, 2021-08-12]
parts/hot-end/part-cooling-fan.SLDPRT
40.0 x 40.0 x 10.0 mm
