greenmagics/Ender5plus_greenmaker_mod/parts/x-axis-assem/x-axis-pulley-mount.SLDPRT

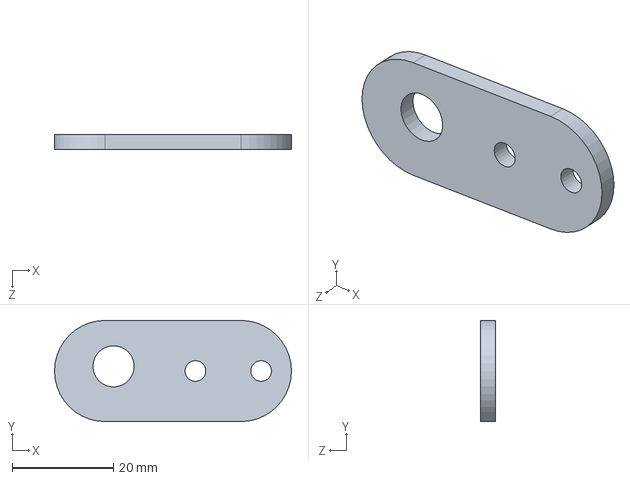
[picture p132: CAD file, 2021-08-12]
parts/x-axis-assem/x-axis-pulley-mount.SLDPRT
46.8 x 20.0 x 3.00 mm
