greenmagics/Ender5plus_greenmaker_mod/parts/z-axis-drive-assem/z-axis-stepper-bracket.SLDPRT

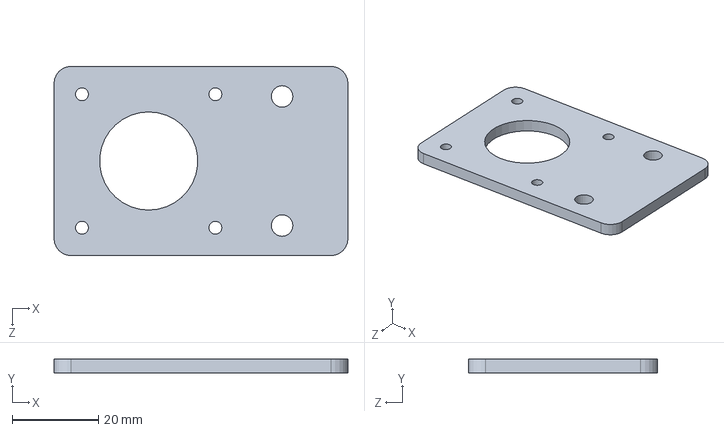
[picture p133: CAD file, 2021-08-12]
parts/z-axis-drive-assem/z-axis-stepper-bracket.SLDPRT
68.3 x 3.20 x 44.0 mm
