greenmagics/Ender5plus_greenmaker_mod/czesci_dodane/direct/nawiew_v3.SLDPRT

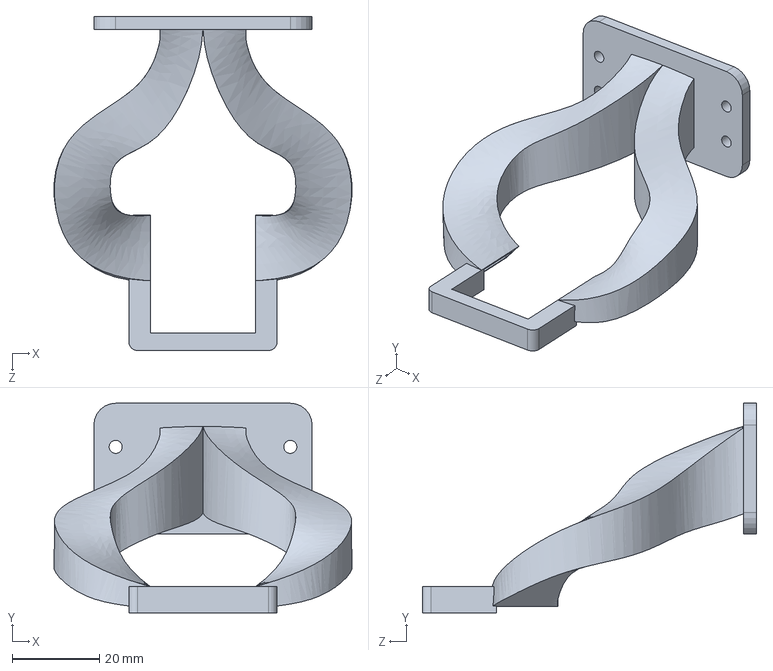
[picture p134: CAD file, 2021-08-12]
czesci_dodane/direct/nawiew_v3.SLDPRT
68.2 x 48.0 x 76.5 mm
