greenmagics/Ender5plus_greenmaker_mod/parts/x-axis-assem/x-axis-strut.SLDPRT

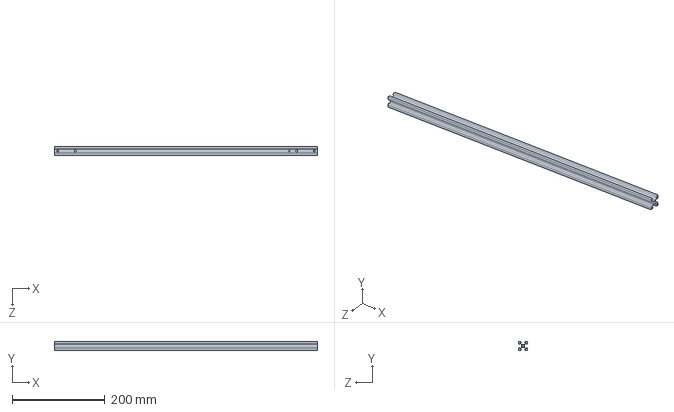
[picture p135: CAD file, 2021-08-12]
parts/x-axis-assem/x-axis-strut.SLDPRT
568.0 x 20.0 x 20.0 mm
