greenmagics/Ender5plus_greenmaker_mod/parts/z-axis-drive-assem/limit-switch.SLDPRT

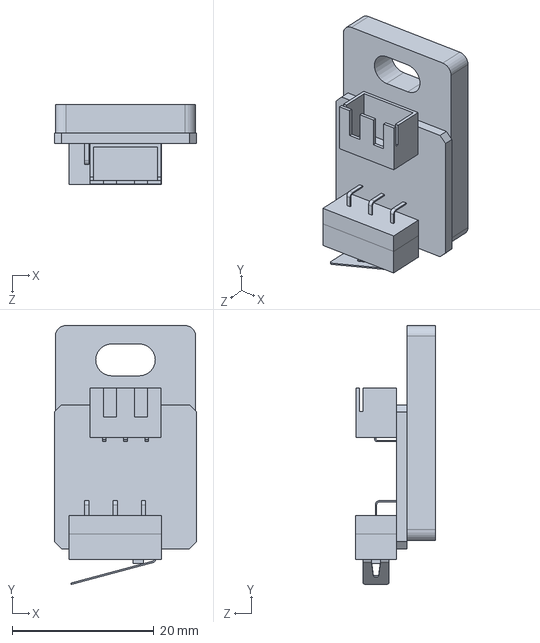
[picture p136: CAD file, 2021-08-12]
parts/z-axis-drive-assem/limit-switch.SLDPRT
20.1 x 36.5 x 11.3 mm
