greenmagics/Ender5plus_greenmaker_mod/parts/extruder/extruder-spring-bushing.SLDPRT

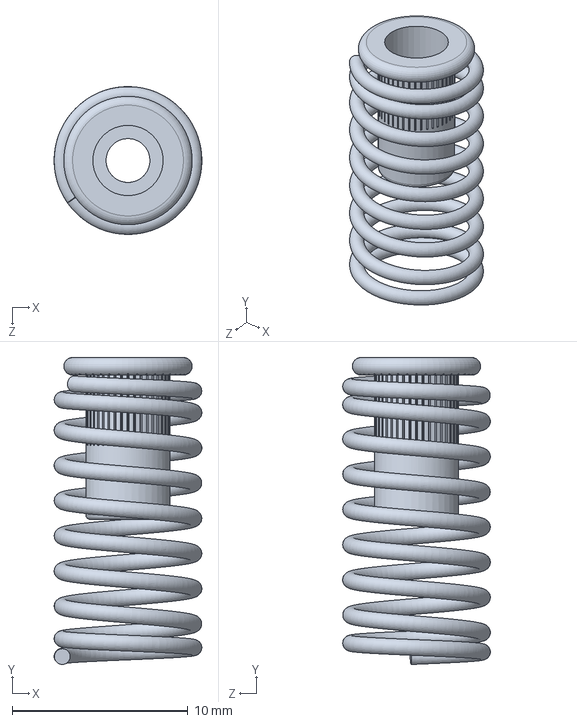
[picture p137: CAD file, 2021-08-12]
parts/extruder/extruder-spring-bushing.SLDPRT
8.40 x 17.4 x 8.40 mm
