greenmagics/Ender5plus_greenmaker_mod/parts/z-axis-drive-assem/shaft-coupling.SLDPRT

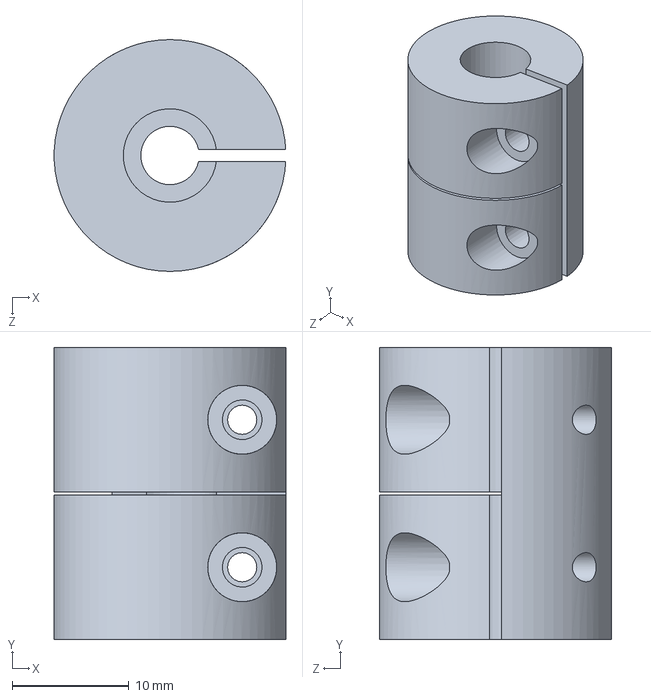
[picture p138: CAD file, 2021-08-12]
parts/z-axis-drive-assem/shaft-coupling.SLDPRT
19.8 x 25.0 x 19.8 mm
