greenmagics/Ender5plus_greenmaker_mod/parts/z-axis-drive-assem/z-axis-bearing-plate.SLDPRT

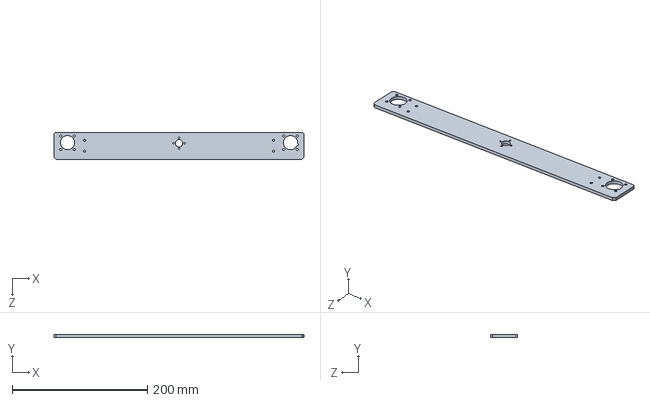
[picture p139: CAD file, 2021-08-12]
parts/z-axis-drive-assem/z-axis-bearing-plate.SLDPRT
370.0 x 4.00 x 40.0 mm
