greenmagics/Ender5plus_greenmaker_mod/parts/z-axis-drive-assem/flanged-bearing-10mm.SLDPRT

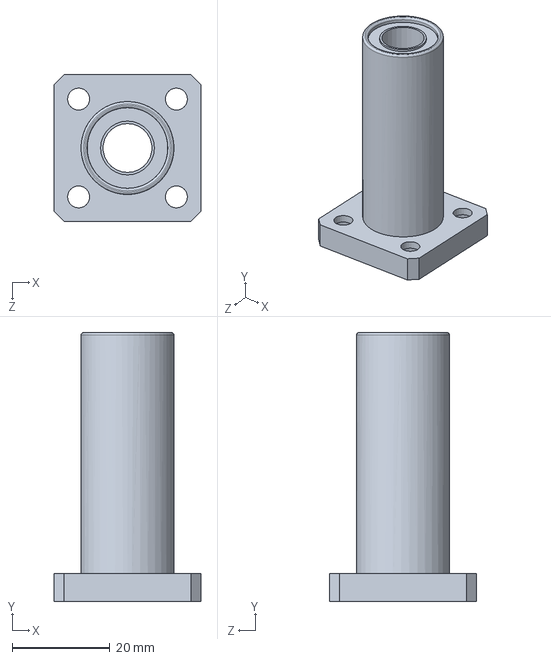
[picture p140: CAD file, 2021-08-12]
parts/z-axis-drive-assem/flanged-bearing-10mm.SLDPRT
30.0 x 55.0 x 30.0 mm
